Takazudo/zudo-scope10/reference/assets/pot/ASSET-NOTES.md

# RK09L1140A5L

Record: `c7419101`

3D status: **exact_manufacturer_step**

These assets support component selection and CAD inspection. Qualification of the selected manufacturing variant remains separate.

## Facts

{
  "electrical": [
    "Single 10 kΩ linear 1B; ±20%; 0.05 W; max 50 VAC / 10 VDC.",
    "Pins 1 and 3 are track ends; pin 2 is wiper."
  ],
  "mechanical": [
    "Vertical flat metal shaft, L1=15 mm; diameter 6 mm with drawing tolerances, flat dimension 4.5 mm.",
    "M9×0.75 bushing; LB=5 mm; flat length l1=7 mm.",
    "Drawing body width 12.1 mm; mounting-side hole drawing has three 1 mm electrical holes across a 5 mm span and 11.3 mm support spacing.",
    "300° ±5° rotation, no detent; drawing shows full CCW shaft position."
  ],
  "soldering": [
    "Manufacturer product page: dip 260±5 °C max, 5±1 s, max 2 passes; preheat underside 100 °C max, 2 min.",
    "Hand solder reference 350 °C max, 3 s, once; factory process must be agreed."
  ],
  "source": [
    "Exact product-page dimensional GIF and official RK09L catalog drawing 3."
  ]
}

## Gaps

[
  "Footprint must still be checked against the exact drawing and board stack.",
  "Factory process acceptance and current availability are not established by these files."
]
