Takazudo/zudo-scope10/doc/src/content/docs/components/records/c470p.mdx

---
# GENERATED by scripts/build_docs.py
title: "06035A471KAT2A"
sidebar_position: 24
---

## Identity

| Field | Value |
|---|---|
| Record | c470p |
| Manufacturer | Kyocera AVX |
| Orderable identity | 06035A471KAT2A |
| JLC/LCSC | C597169 |
| Package | 0603 |
| Identity | SPECIFICATION_ONLY |
| Fit | PROPOSED_NOT_ASSEMBLED |
| References | C101 C201 C301 C401 C501 C601 C701 C801 C901 C1001 |
| Footprint candidate | Capacitor_SMD:C_0603_1608Metric |

## Intended function

input filter

## Recorded findings

470pF; C0G 5% &gt;=25 V. Value specified by this design; not an exact orderable.

G08 candidate: LCSC C597169 (https://www.lcsc.com/product-detail/multilayer-ceramic-capacitors-mlcc-smd-smt_kyocera-avx-06035a471kat2a_C597169.html), checked 2026-09-26, stock 240. listing_not_allocation: a page listing is not allocated stock or an order.

## Pin map

Pin assignments below are electrical evidence or explicitly logical placeholders. They are not footprint qualification.

| Pin | Function |
|---|---|
| 1 | P1 |
| 2 | P2 |

## Documents and models

No original model or source binary was recovered for this record in this package. See the sources and the local download manifest; no nominal model is presented as an exact replacement.

## Coverage and unresolved questions

**Footprint independently qualified: NO. Factory order approved: NO. Bench result: NOT TESTED.**

- meets_spec: NO on tolerance. Value/dielectric/voltage/package match, but the page states +/-10% tolerance, looser than this design's stated 5% max. Do not fabricate against this candidate without a tighter-tolerance replacement or a design tolerance review.

The presence of a part number, datasheet or model closes none of these remaining gates automatically.

## Sources

Values and package constraints are authored design requirements, not manufacturer-verified specifications of a selected orderable part. Select the exact item and add its evidence before placement.
