Takazudo/zudo-scope10/doc/src/content/docs/components/records/display.mdx

---
# GENERATED by scripts/build_docs.py
title: "Pico-ResTouch-LCD-3.5 (SKU 19907)"
sidebar_position: 7
---

## Identity

| Field | Value |
|---|---|
| Record | display |
| Manufacturer | Waveshare |
| Orderable identity | Pico-ResTouch-LCD-3.5 (SKU 19907) |
| JLC/LCSC | NOT VERIFIED / NOT APPLICABLE |
| Package | 86 x 57.2 mm board |
| Identity | EXACT_MPN |
| Fit | PROPOSED_NOT_ASSEMBLED |
| References | External plug-in module |
| Footprint candidate | NOT ASSIGNED |

## Intended function

Single display with ten panes; touch and SD unused

## Recorded findings

480 x 320; portrait logical surface 320 x 480. Active area 48.96 x 73.44 mm in portrait.

5 V module; 3.3 V logic. Vendor module uses a serial-to-16-bit-parallel bridge and RGB565.

Factory female Pico socket headers are present.

Outline 86.00 x 57.20 x 1.6 mm PCB, R1.0 corners; two 1.0 mm recesses on the pin-1 edge (RUN 38.64-47.62, microSD 61.06-76.95 from the header-side edge).

Mounting holes 4.10 from each corner, 77.80 x 49.00 pitch; STEP models dia 5.5 x 4.0 mm standoffs (dia 2.5 bore) on the socket side. Drill diameter not dimensioned.

Female Pico sockets on the non-LCD side: pins 1-20 row 10.45 mm and pins 21-40 row 28.25 mm from the header-side edge (17.80 in STEP, 17.78 nominal); pin 1 and pin 40 at 1.62 mm from the pin-1 edge; pitch 2.54.

Socket housing extends 9.0 mm below the module PCB; modelled cavity depth 8.0 mm. Other underside parts &lt;= 4.0 mm (standoffs), RUN switch 3.5 mm.

Active area 73.44 x 48.96 mm at 3.60 (header side) / 8.96 / 3.97 (pin-1 edge) / 4.27 mm from the board edges; glass top 5.2 mm above module PCB top.

## Pin map

Pin assignments below are electrical evidence or explicitly logical placeholders. They are not footprint qualification.

| Pin | Function |
|---|---|
| 1 | GP0 |
| 2 | GP1 |
| 3 | GND |
| 4 | GP2 |
| 5 | GP3 |
| 6 | GP4 |
| 7 | GP5 |
| 8 | GND |
| 9 | GP6 |
| 10 | GP7 |
| 11 | GP8 |
| 12 | GP9 |
| 13 | GND |
| 14 | GP10 |
| 15 | GP11 |
| 16 | GP12 |
| 17 | GP13 |
| 18 | GND |
| 19 | GP14 |
| 20 | GP15 |
| 21 | GP16 |
| 22 | GP17 |
| 23 | GND |
| 24 | GP18 |
| 25 | GP19 |
| 26 | GP20 |
| 27 | GP21 |
| 28 | GND |
| 29 | GP22 |
| 30 | RUN |
| 31 | GP26_ADC0 |
| 32 | GP27_ADC1 |
| 33 | AGND |
| 34 | GP28_ADC2 |
| 35 | ADC_VREF |
| 36 | 3V3_OUT |
| 37 | 3V3_EN |
| 38 | GND |
| 39 | VSYS |
| 40 | VBUS |

## Documents and models

No original model or source binary was recovered for this record in this package. See the sources and the local download manifest; no nominal model is presented as an exact replacement.

## Coverage and unresolved questions

**Footprint independently qualified: NO. Factory order approved: NO. Bench result: NOT TESTED.**

- STOP: inspect R11/R12/R14/R15 regulator straps and module revision before connecting power.
- Do not tie Pico 3V3_OUT to the display regulator output.
- Verify high/low unused chip-select states and SPI word framing.
- Measure mounting-hole drill and standoff thread; confirm socket engagement spec on the received module.

The presence of a part number, datasheet or model closes none of these remaining gates automatically.

## Sources

### Waveshare SKU 19907

[https://www.waveshare.com/Pico-ResTouch-LCD-3.5.htm](https://www.waveshare.com/Pico-ResTouch-LCD-3.5.htm)

Evidence state: `read_online`. Manufacturer page: 480x320, 5 V, installed female Pico headers, 86x57.2 mm module.

### Waveshare interface and resources

[https://www.waveshare.net/wiki/Pico-ResTouch-LCD-3.5](https://www.waveshare.net/wiki/Pico-ResTouch-LCD-3.5)

Evidence state: `read_online`. Manufacturer pin assignment table and 16-bit parallel-to-SPI bridge explanation; RGB565.

### Waveshare module schematic

[https://files.waveshare.com/upload/8/85/Pico-ResTouch-LCD-3.5_Sch.pdf](https://files.waveshare.com/upload/8/85/Pico-ResTouch-LCD-3.5_Sch.pdf)

Evidence state: `read_online`. Parsed online. Page-image retrieval failed. Module regulator straps and power connections require visual verification locally.

### Waveshare module CAD archive

[https://files.waveshare.com/upload/e/e4/Pico-ResTouch-LCD-3_5.zip](https://files.waveshare.com/upload/e/e4/Pico-ResTouch-LCD-3_5.zip)

Evidence state: `download_unavailable`. Official link; binary download failed in this environment. NOT included.

### Waveshare example code

[https://files.waveshare.com/upload/f/fc/Pico-ResTouch-LCD-X_X_Code.zip](https://files.waveshare.com/upload/f/fc/Pico-ResTouch-LCD-X_X_Code.zip)

Evidence state: `download_unavailable`. Official link; binary download failed. Vendor driver integration remains open; do not use generic ILI9488 serial driver.
