Takazudo/zudo-scope10/doc/src/content/docs/components/records/fuse.mdx

---
# GENERATED by scripts/build_docs.py
title: "1206L050YR"
sidebar_position: 14
---

## Identity

| Field | Value |
|---|---|
| Record | fuse |
| Manufacturer | Littelfuse |
| Orderable identity | 1206L050YR |
| JLC/LCSC | C163512 |
| Package | 1206 PPTC candidate |
| Identity | SPECIFICATION_ONLY |
| Fit | PROPOSED_NOT_ASSEMBLED |
| References | F1 |
| Footprint candidate | NOT ASSIGNED |

## Intended function

Analog/display branch protection

## Recorded findings

Proposed 500 mA hold, &gt;=6 V. This does not limit Pico USB inrush before the carrier branch.

G08 candidate: LCSC C163512, Littelfuse 1206L050YR (https://lcsc.com/product-detail/Resettable-Fuses_Littelfuse-1206L050YR_C163512.html), checked 2026-09-26, stock 21130. listing_not_allocation: a page listing is not allocated stock or an order.

## Pin map

Pin assignments below are electrical evidence or explicitly logical placeholders. They are not footprint qualification.

| Pin | Function |
|---|---|
| 1 | IN |
| 2 | OUT |

## Documents and models

No original model or source binary was recovered for this record in this package. See the sources and the local download manifest; no nominal model is presented as an exact replacement.

## Coverage and unresolved questions

**Footprint independently qualified: NO. Factory order approved: NO. Bench result: NOT TESTED.**

- meets_spec: exact match at 500 mA hold / 6 V, no margin above the stated minimums. Sizing against the actual measured inrush budget is out of scope for this evidence pass (see G07). Select/confirm the actual part and qualify trip time, cold resistance and USB current budget before fabrication.

The presence of a part number, datasheet or model closes none of these remaining gates automatically.

## Sources

Values and package constraints are authored design requirements, not manufacturer-verified specifications of a selected orderable part. Select the exact item and add its evidence before placement.
