Takazudo/zudo-scope10/doc/src/content/docs/components/records/pico-h.mdx

---
# GENERATED by scripts/build_docs.py
title: "Raspberry Pi Pico H"
sidebar_position: 6
---

## Identity

| Field | Value |
|---|---|
| Record | pico-h |
| Manufacturer | Raspberry Pi |
| Orderable identity | Raspberry Pi Pico H |
| JLC/LCSC | NOT VERIFIED / NOT APPLICABLE |
| Package | 51 x 21 mm board |
| Identity | EXACT_MPN |
| Fit | PROPOSED_NOT_ASSEMBLED |
| References | External plug-in module |
| Footprint candidate | NOT ASSIGNED |

## Intended function

Socketed RP2040 module with factory-populated headers and USB

## Recorded findings

Factory H version only; the ordinary bare-header Pico does not meet the no-soldering purchase specification.

Pico ADC inputs are GP26-28; GP29 is not a free external ADC pin on this board.

500 kS/s is aggregate. Ten inputs are acquired sequentially.

51 x 21 x 1.0 mm; pin rows 17.78 apart, 48.26 first-to-last, 2.54 pitch; micro-USB overhangs the pin-1 edge by 1.3 mm; 4 x dia 2.1 holes 11.4 apart, 2.0 from the USB edge and 2.4 from the far edge.

Physical numbering: pin 1 top-left beside USB, 1-20 down the left, 40 top-right. Orderable SC0917.

## Pin map

Pin assignments below are electrical evidence or explicitly logical placeholders. They are not footprint qualification.

| Pin | Function |
|---|---|
| 1 | GP0 |
| 2 | GP1 |
| 3 | GND |
| 4 | GP2 |
| 5 | GP3 |
| 6 | GP4 |
| 7 | GP5 |
| 8 | GND |
| 9 | GP6 |
| 10 | GP7 |
| 11 | GP8 |
| 12 | GP9 |
| 13 | GND |
| 14 | GP10 |
| 15 | GP11 |
| 16 | GP12 |
| 17 | GP13 |
| 18 | GND |
| 19 | GP14 |
| 20 | GP15 |
| 21 | GP16 |
| 22 | GP17 |
| 23 | GND |
| 24 | GP18 |
| 25 | GP19 |
| 26 | GP20 |
| 27 | GP21 |
| 28 | GND |
| 29 | GP22 |
| 30 | RUN |
| 31 | GP26_ADC0 |
| 32 | GP27_ADC1 |
| 33 | AGND |
| 34 | GP28_ADC2 |
| 35 | ADC_VREF |
| 36 | 3V3_OUT |
| 37 | 3V3_EN |
| 38 | GND |
| 39 | VSYS |
| 40 | VBUS |

## Documents and models

No original model or source binary was recovered for this record in this package. See the sources and the local download manifest; no nominal model is presented as an exact replacement.

## Coverage and unresolved questions

**Footprint independently qualified: NO. Factory order approved: NO. Bench result: NOT TESTED.**

- Module socket exact MPN, standoff height and USB access; verify Pico H module pinout against assembly.
- Pico H factory header insulator height and pin length are not dimensioned in the Pico datasheet/product brief; measure a unit or obtain a Raspberry Pi drawing.

The presence of a part number, datasheet or model closes none of these remaining gates automatically.

## Sources

### Raspberry Pi Pico / Pico H

[https://www.raspberrypi.com/products/raspberry-pi-pico/](https://www.raspberrypi.com/products/raspberry-pi-pico/)

Evidence state: `read_online`. Manufacturer product page. Order H version with installed headers, not an unsoldered Pico.

### Pico pinout

[https://datasheets.raspberrypi.com/pico/Pico-R3-A4-Pinout.pdf](https://datasheets.raspberrypi.com/pico/Pico-R3-A4-Pinout.pdf)

Evidence state: `read_online`. Pinout inspected online as page image. Same header numbering used for both carrier interfaces.

### Pico SDK ADC documentation

[https://www.raspberrypi.com/documentation/pico-sdk/hardware.html](https://www.raspberrypi.com/documentation/pico-sdk/hardware.html)

Evidence state: `read_online`. RP2040: 12-bit ADC, 500 ksample/s aggregate; 8.7 ENOB. Sequential channels, not simultaneous sample-and-hold.
