Takazudo/zudo-scope10/doc/src/content/docs/components/records/r100.mdx

---
# GENERATED by scripts/build_docs.py
title: "0603 \u00b11% 100\u03a9 (VO)"
sidebar_position: 21
---

## Identity

| Field | Value |
|---|---|
| Record | r100 |
| Manufacturer | VO |
| Orderable identity | 0603 ±1% 100Ω (VO) |
| JLC/LCSC | C2889384 |
| Package | 0603 |
| Identity | SPECIFICATION_ONLY |
| Fit | PROPOSED_NOT_ASSEMBLED |
| References | R20 R21 R22 |
| Footprint candidate | Resistor_SMD:R_0603_1608Metric |

## Intended function

ADC isolation

## Recorded findings

100; 1%. Value specified by this design; not an exact orderable.

G08 candidate: LCSC C2889384 (https://www.lcsc.com/product-detail/Chip-Resistor-Surface-Mount_VO_C2889384.html), checked 2026-09-26, meets spec. Page states "Not available now". listing_not_allocation: a page listing is not allocated stock or an order.

## Pin map

Pin assignments below are electrical evidence or explicitly logical placeholders. They are not footprint qualification.

| Pin | Function |
|---|---|
| 1 | P1 |
| 2 | P2 |

## Documents and models

No original model or source binary was recovered for this record in this package. See the sources and the local download manifest; no nominal model is presented as an exact replacement.

## Coverage and unresolved questions

**Footprint independently qualified: NO. Factory order approved: NO. Bench result: NOT TESTED.**

- RFQ/allocate stock before fabrication; page shows zero availability at the time checked.

The presence of a part number, datasheet or model closes none of these remaining gates automatically.

## Sources

Values and package constraints are authored design requirements, not manufacturer-verified specifications of a selected orderable part. Select the exact item and add its evidence before placement.
