Takazudo/zudo-scope10/doc/src/content/docs/components/records/r100k.mdx

---
# GENERATED by scripts/build_docs.py
title: "0603WAF1003T5E"
sidebar_position: 20
---

## Identity

| Field | Value |
|---|---|
| Record | r100k |
| Manufacturer | UNI-ROYAL |
| Orderable identity | 0603WAF1003T5E |
| JLC/LCSC | C25803 |
| Package | 0603 |
| Identity | SPECIFICATION_ONLY |
| Fit | PROPOSED_NOT_ASSEMBLED |
| References | R80 R81 R82 R83 R84 R85 R86 R87 R88 |
| Footprint candidate | Resistor_SMD:R_0603_1608Metric |

## Intended function

digital/default pulls

## Recorded findings

100k; 1%. Value specified by this design; not an exact orderable.

G08 candidate: LCSC C25803 (https://www.lcsc.com/product-detail/C25803.html), checked 2026-09-26, meets spec, stock 17040200. listing_not_allocation: a page listing is not allocated stock or an order.

## Pin map

Pin assignments below are electrical evidence or explicitly logical placeholders. They are not footprint qualification.

| Pin | Function |
|---|---|
| 1 | P1 |
| 2 | P2 |

## Documents and models

No original model or source binary was recovered for this record in this package. See the sources and the local download manifest; no nominal model is presented as an exact replacement.

## Coverage and unresolved questions

**Footprint independently qualified: NO. Factory order approved: NO. Bench result: NOT TESTED.**

- RFQ/allocate stock before fabrication; listing is not an order.

The presence of a part number, datasheet or model closes none of these remaining gates automatically.

## Sources

Values and package constraints are authored design requirements, not manufacturer-verified specifications of a selected orderable part. Select the exact item and add its evidence before placement.
