Takazudo/zudo-scope10/doc/src/content/docs/components/records/r10k.mdx

---
# GENERATED by scripts/build_docs.py
title: "0603WAF1002T5E"
sidebar_position: 19
---

## Identity

| Field | Value |
|---|---|
| Record | r10k |
| Manufacturer | UNI-ROYAL |
| Orderable identity | 0603WAF1002T5E |
| JLC/LCSC | C25804 |
| Package | 0603 |
| Identity | SPECIFICATION_ONLY |
| Fit | PROPOSED_NOT_ASSEMBLED |
| References | R40 R41 R51 R52 |
| Footprint candidate | Resistor_SMD:R_0603_1608Metric |

## Intended function

switch ladder, pulls

## Recorded findings

10k; 1%. Value specified by this design; not an exact orderable.

G08 candidate: LCSC C25804 (https://www.lcsc.com/product-detail/C25804.html), checked 2026-09-26, meets spec. Page states "Out of Stock" with a "Notify Me" option. listing_not_allocation: a page listing is not allocated stock or an order.

## Pin map

Pin assignments below are electrical evidence or explicitly logical placeholders. They are not footprint qualification.

| Pin | Function |
|---|---|
| 1 | P1 |
| 2 | P2 |

## Documents and models

No original model or source binary was recovered for this record in this package. See the sources and the local download manifest; no nominal model is presented as an exact replacement.

## Coverage and unresolved questions

**Footprint independently qualified: NO. Factory order approved: NO. Bench result: NOT TESTED.**

- RFQ/allocate stock before fabrication; page shows zero stock at the time checked.

The presence of a part number, datasheet or model closes none of these remaining gates automatically.

## Sources

Values and package constraints are authored design requirements, not manufacturer-verified specifications of a selected orderable part. Select the exact item and add its evidence before placement.
