Takazudo/zudo-scope10/doc/src/content/docs/components/records/r1k.mdx

---
# GENERATED by scripts/build_docs.py
title: "0603WAF1001T5E"
sidebar_position: 22
---

## Identity

| Field | Value |
|---|---|
| Record | r1k |
| Manufacturer | UNI-ROYAL |
| Orderable identity | 0603WAF1001T5E |
| JLC/LCSC | C21190 |
| Package | 0603 |
| Identity | SPECIFICATION_ONLY |
| Fit | PROPOSED_NOT_ASSEMBLED |
| References | R1111 R1112 R1121 R1122 R1131 R1132 R1141 R1142 R1151 R1152 R1161 R1162 R1171 R1172 R1181 R1182 R1191 R1192 R1201 R1202 R30 |
| Footprint candidate | Resistor_SMD:R_0603_1608Metric |

## Intended function

control isolation/rail bleed

## Recorded findings

1k; 1%. Value specified by this design; not an exact orderable.

G08 candidate: LCSC C21190 (https://www.lcsc.com/product-detail/C21190.html), checked 2026-09-26, meets spec, stock 7514000. listing_not_allocation: a page listing is not allocated stock or an order.

## Pin map

Pin assignments below are electrical evidence or explicitly logical placeholders. They are not footprint qualification.

| Pin | Function |
|---|---|
| 1 | P1 |
| 2 | P2 |

## Documents and models

No original model or source binary was recovered for this record in this package. See the sources and the local download manifest; no nominal model is presented as an exact replacement.

## Coverage and unresolved questions

**Footprint independently qualified: NO. Factory order approved: NO. Bench result: NOT TESTED.**

- RFQ/allocate stock before fabrication; listing is not an order.

The presence of a part number, datasheet or model closes none of these remaining gates automatically.

## Sources

Values and package constraints are authored design requirements, not manufacturer-verified specifications of a selected orderable part. Select the exact item and add its evidence before placement.
