Takazudo/zudo-scope10/doc/src/content/docs/components/records/r1m.mdx

---
# GENERATED by scripts/build_docs.py
title: "RT0603BRD071ML"
sidebar_position: 15
---

## Identity

| Field | Value |
|---|---|
| Record | r1m |
| Manufacturer | YAGEO |
| Orderable identity | RT0603BRD071ML |
| JLC/LCSC | C326730 |
| Package | 0603 |
| Identity | SPECIFICATION_ONLY |
| Fit | PROPOSED_NOT_ASSEMBLED |
| References | R101 R201 R301 R401 R501 R601 R701 R801 R901 R1001 |
| Footprint candidate | Resistor_SMD:R_0603_1608Metric |

## Intended function

input impedance/current limit

## Recorded findings

1M; 0.1% 25 ppm/C; &gt;=50 V. Value specified by this design; not an exact orderable.

G08 candidate: LCSC C326730 (https://www.lcsc.com/product-detail/C326730.html), checked 2026-09-26, meets spec, stock 8540. listing_not_allocation: a page listing is not allocated stock or an order.

## Pin map

Pin assignments below are electrical evidence or explicitly logical placeholders. They are not footprint qualification.

| Pin | Function |
|---|---|
| 1 | P1 |
| 2 | P2 |

## Documents and models

No original model or source binary was recovered for this record in this package. See the sources and the local download manifest; no nominal model is presented as an exact replacement.

## Coverage and unresolved questions

**Footprint independently qualified: NO. Factory order approved: NO. Bench result: NOT TESTED.**

- RFQ/allocate stock before fabrication; listing is not an order.

The presence of a part number, datasheet or model closes none of these remaining gates automatically.

## Sources

Values and package constraints are authored design requirements, not manufacturer-verified specifications of a selected orderable part. Select the exact item and add its evidence before placement.
