Takazudo/zudo-scope10/doc/src/content/docs/components/records/r200k.mdx

---
# GENERATED by scripts/build_docs.py
title: "RT0603BRD07200KL"
sidebar_position: 16
---

## Identity

| Field | Value |
|---|---|
| Record | r200k |
| Manufacturer | YAGEO |
| Orderable identity | RT0603BRD07200KL |
| JLC/LCSC | C728585 |
| Package | 0603 |
| Identity | SPECIFICATION_ONLY |
| Fit | PROPOSED_NOT_ASSEMBLED |
| References | R102 R202 R302 R402 R502 R602 R702 R802 R902 R1002 |
| Footprint candidate | Resistor_SMD:R_0603_1608Metric |

## Intended function

bias divider

## Recorded findings

200k; 0.1% 25 ppm/C. Value specified by this design; not an exact orderable.

G08 candidate: LCSC C728585 (https://lcsc.com/product-detail/chip-resistor-surface-mount_yageo-rt0603brd07200kl_C728585.html), checked 2026-09-26, meets spec, stock 248120. listing_not_allocation: a page listing is not allocated stock or an order.

## Pin map

Pin assignments below are electrical evidence or explicitly logical placeholders. They are not footprint qualification.

| Pin | Function |
|---|---|
| 1 | P1 |
| 2 | P2 |

## Documents and models

No original model or source binary was recovered for this record in this package. See the sources and the local download manifest; no nominal model is presented as an exact replacement.

## Coverage and unresolved questions

**Footprint independently qualified: NO. Factory order approved: NO. Bench result: NOT TESTED.**

- RFQ/allocate stock before fabrication; listing is not an order.

The presence of a part number, datasheet or model closes none of these remaining gates automatically.

## Sources

Values and package constraints are authored design requirements, not manufacturer-verified specifications of a selected orderable part. Select the exact item and add its evidence before placement.
