Takazudo/zudo-scope10/doc/src/content/docs/components/records/r249k.mdx

---
# GENERATED by scripts/build_docs.py
title: "r249k / supplier selection open"
sidebar_position: 17
---

## Identity

| Field | Value |
|---|---|
| Record | r249k |
| Manufacturer | RFQ value/package selection |
| Orderable identity | NOT SELECTED |
| JLC/LCSC | NOT VERIFIED / NOT APPLICABLE |
| Package | 0603 |
| Identity | SPECIFICATION_ONLY |
| Fit | PROPOSED_NOT_ASSEMBLED |
| References | R103 R203 R303 R403 R503 R603 R703 R803 R903 R1003 |
| Footprint candidate | Resistor_SMD:R_0603_1608Metric |

## Intended function

bias divider

## Recorded findings

249k; 0.1% 25 ppm/C. Value specified by this design; not an exact orderable.

G08 (#9): manufacturer spec sheet confirms YAGEO RT0603BRD07249KL exists at this value, but no LCSC product-detail page was found or fetched; no C-number is recorded here without a fetched citation.

## Pin map

Pin assignments below are electrical evidence or explicitly logical placeholders. They are not footprint qualification.

| Pin | Function |
|---|---|
| 1 | P1 |
| 2 | P2 |

## Documents and models

No original model or source binary was recovered for this record in this package. See the sources and the local download manifest; no nominal model is presented as an exact replacement.

## Coverage and unresolved questions

**Footprint independently qualified: NO. Factory order approved: NO. Bench result: NOT TESTED.**

- OPEN: no cited LCSC/JLC listing found for the 249k value; assign a stocked exact MPN/C-code and source its datasheet before fabrication.

The presence of a part number, datasheet or model closes none of these remaining gates automatically.

## Sources

Values and package constraints are authored design requirements, not manufacturer-verified specifications of a selected orderable part. Select the exact item and add its evidence before placement.
