Takazudo/zudo-scope10/doc/src/content/docs/components/records/r33.mdx

---
# GENERATED by scripts/build_docs.py
title: "RC0603FR-0733RL"
sidebar_position: 23
---

## Identity

| Field | Value |
|---|---|
| Record | r33 |
| Manufacturer | YAGEO |
| Orderable identity | RC0603FR-0733RL |
| JLC/LCSC | C108661 |
| Package | 0603 |
| Identity | SPECIFICATION_ONLY |
| Fit | PROPOSED_NOT_ASSEMBLED |
| References | R60 R61 R62 R63 R64 R65 R66 R67 R68 R69 |
| Footprint candidate | Resistor_SMD:R_0603_1608Metric |

## Intended function

SPI source termination

## Recorded findings

33; 1%. Value specified by this design; not an exact orderable.

G08 candidate: LCSC C108661 (https://www.lcsc.com/product-detail/C108661.html), checked 2026-09-26, meets spec, stock 85500. listing_not_allocation: a page listing is not allocated stock or an order.

G08 rejected a false match found in the same search: 0603WAF3300T5E / C23138 is 330Ω, not 33Ω; not used.

## Pin map

Pin assignments below are electrical evidence or explicitly logical placeholders. They are not footprint qualification.

| Pin | Function |
|---|---|
| 1 | P1 |
| 2 | P2 |

## Documents and models

No original model or source binary was recovered for this record in this package. See the sources and the local download manifest; no nominal model is presented as an exact replacement.

## Coverage and unresolved questions

**Footprint independently qualified: NO. Factory order approved: NO. Bench result: NOT TESTED.**

- RFQ/allocate stock before fabrication; listing is not an order.

The presence of a part number, datasheet or model closes none of these remaining gates automatically.

## Sources

Values and package constraints are authored design requirements, not manufacturer-verified specifications of a selected orderable part. Select the exact item and add its evidence before placement.
