Takazudo/zudo-scope10/doc/src/content/docs/components/records/r4k7.mdx

---
# GENERATED by scripts/build_docs.py
title: "HoLTT0603-1/10W-4.7K-1%"
sidebar_position: 18
---

## Identity

| Field | Value |
|---|---|
| Record | r4k7 |
| Manufacturer | Milliohm |
| Orderable identity | HoLTT0603-1/10W-4.7K-1% |
| JLC/LCSC | C2904521 |
| Package | 0603 |
| Identity | SPECIFICATION_ONLY |
| Fit | PROPOSED_NOT_ASSEMBLED |
| References | R104 R204 R304 R404 R504 R604 R704 R804 R904 R1004 |
| Footprint candidate | Resistor_SMD:R_0603_1608Metric |

## Intended function

second filter

## Recorded findings

4.7k; 1%. Value specified by this design; not an exact orderable.

G08 candidate: LCSC C2904521 (https://www.lcsc.com/product-detail/C2904521.html), checked 2026-09-26, meets spec, stock 820. listing_not_allocation: a page listing is not allocated stock or an order.

## Pin map

Pin assignments below are electrical evidence or explicitly logical placeholders. They are not footprint qualification.

| Pin | Function |
|---|---|
| 1 | P1 |
| 2 | P2 |

## Documents and models

No original model or source binary was recovered for this record in this package. See the sources and the local download manifest; no nominal model is presented as an exact replacement.

## Coverage and unresolved questions

**Footprint independently qualified: NO. Factory order approved: NO. Bench result: NOT TESTED.**

- RFQ/allocate stock before fabrication; listing is not an order.

The presence of a part number, datasheet or model closes none of these remaining gates automatically.

## Sources

Values and package constraints are authored design requirements, not manufacturer-verified specifications of a selected orderable part. Select the exact item and add its evidence before placement.
