Takazudo/zudo-scope10/doc/src/content/docs/components/records/ref.mdx

---
# GENERATED by scripts/build_docs.py
title: "REF3330AIDBZR"
sidebar_position: 4
---

## Identity

| Field | Value |
|---|---|
| Record | ref |
| Manufacturer | Texas Instruments |
| Orderable identity | REF3330AIDBZR |
| JLC/LCSC | C140329 |
| Package | SOT-23-3 |
| Identity | EXACT_MPN |
| Fit | PROPOSED_NOT_ASSEMBLED |
| References | U11 |
| Footprint candidate | Package_TO_SOT_SMD:SOT-23 |

## Intended function

3.0 V reference buffered by U6D

## Recorded findings

3.0 V version; 0.15% initial accuracy and 30 ppm/C maximum drift are family specifications.

G08 (#9) fetched LCSC C140329 (https://www.lcsc.com/product-detail/C140329.html), checked 2026-09-26, exact MPN match confirmed (REF3330AIDBZR, TI, SOT-23, 3V, +/-0.15%, 30ppm/C max), stock 5102. This verifies, via LCSC, the previously unverified note; JLCPCB's own partdetail page was not independently fetched. listing_not_allocation: a page listing is not allocated stock or an order.

## Pin map

Pin assignments below are electrical evidence or explicitly logical placeholders. They are not footprint qualification.

| Pin | Function |
|---|---|
| 1 | IN |
| 2 | OUT |
| 3 | GND |

## Documents and models

No original model or source binary was recovered for this record in this package. See the sources and the local download manifest; no nominal model is presented as an exact replacement.

## Coverage and unresolved questions

**Footprint independently qualified: NO. Factory order approved: NO. Bench result: NOT TESTED.**

- Visual pin review, full supply/headroom check; no claim that reference fixes RP2040 ADC nonlinearity.

The presence of a part number, datasheet or model closes none of these remaining gates automatically.

## Sources

### TI REF33 datasheet

[https://www.ti.com/lit/ds/symlink/ref33.pdf](https://www.ti.com/lit/ds/symlink/ref33.pdf)

Evidence state: `read_online`. DBZ/SOT23 pin table parsed: 1 IN, 2 OUT, 3 GND. Pin diagram screenshot unavailable; independent visual check open.
