Takazudo/zudo-scope10/doc/src/content/docs/components/records/socket20.mdx

---
# GENERATED by scripts/build_docs.py
title: "socket20 / supplier selection open"
sidebar_position: 12
---

## Identity

| Field | Value |
|---|---|
| Record | socket20 |
| Manufacturer | RFQ exact manufacturer |
| Orderable identity | NOT SELECTED |
| JLC/LCSC | NOT VERIFIED / NOT APPLICABLE |
| Package | 2.54 mm; height TBD |
| Identity | SPECIFICATION_ONLY |
| Fit | PROPOSED_NOT_ASSEMBLED |
| References | J20 J21 |
| Footprint candidate | Connector_PinSocket_2.54mm:PinSocket_1x20_P2.54mm_Vertical |

## Intended function

Two 1x20 female sockets for Pico H

## Recorded findings

Exact mating length, insulator height, retention and shoulder clearance are NOT defined by 2.54 mm pitch alone.

Pico H clearance = socket height + Pico H seated header height (OPEN). Allow 1.3 mm USB overhang beyond the pin-1 edge plus plug access. If the Pico sits under the display, the display gap must exceed the Pico stack.

## Pin map

Pin assignments below are electrical evidence or explicitly logical placeholders. They are not footprint qualification.

| Pin | Function |
|---|---|
| 1 | CONTACT |
| 2 | CONTACT |
| 3 | CONTACT |
| 4 | CONTACT |
| 5 | CONTACT |
| 6 | CONTACT |
| 7 | CONTACT |
| 8 | CONTACT |
| 9 | CONTACT |
| 10 | CONTACT |
| 11 | CONTACT |
| 12 | CONTACT |
| 13 | CONTACT |
| 14 | CONTACT |
| 15 | CONTACT |
| 16 | CONTACT |
| 17 | CONTACT |
| 18 | CONTACT |
| 19 | CONTACT |
| 20 | CONTACT |

## Documents and models

No original model or source binary was recovered for this record in this package. See the sources and the local download manifest; no nominal model is presented as an exact replacement.

## Coverage and unresolved questions

**Footprint independently qualified: NO. Factory order approved: NO. Bench result: NOT TESTED.**

- STOP: select exact orderable and mechanical stack. Factory-populate all four strips.

The presence of a part number, datasheet or model closes none of these remaining gates automatically.

## Sources

### Pico pinout

[https://datasheets.raspberrypi.com/pico/Pico-R3-A4-Pinout.pdf](https://datasheets.raspberrypi.com/pico/Pico-R3-A4-Pinout.pdf)

Evidence state: `read_online`. Pinout inspected online as page image. Same header numbering used for both carrier interfaces.
