Takazudo/zudo-scope10/doc/src/content/docs/components/records/clamp.mdx

---
# GENERATED by scripts/build_docs.py
title: "BAV199,215"
sidebar_position: 5
---

## Identity

| Field | Value |
|---|---|
| Record | clamp |
| Manufacturer | Nexperia |
| Orderable identity | BAV199,215 |
| JLC/LCSC | C40919 |
| Package | SOT-23 |
| Identity | EXACT_MPN |
| Fit | PROPOSED_NOT_ASSEMBLED |
| References | D1 D2 D3 D4 D5 D6 D7 D8 D9 D10 |
| Footprint candidate | Package_TO_SOT_SMD:SOT-23 |

## Intended function

Low-leakage input clamp support

## Recorded findings

Two series silicon diodes, junction pin 3.

External diodes are not guaranteed to conduct before op-amp internal clamps; the 1 Mohm series resistor is the primary current limit.

## Pin map

Pin assignments below are electrical evidence or explicitly logical placeholders. They are not footprint qualification.

| Pin | Function |
|---|---|
| 1 | ANODE_LOW |
| 2 | CATHODE_HIGH |
| 3 | JUNCTION |

## Documents and models

No original model or source binary was recovered for this record in this package. See the sources and the local download manifest; no nominal model is presented as an exact replacement.

## Coverage and unresolved questions

**Footprint independently qualified: NO. Factory order approved: NO. Bench result: NOT TESTED.**

- Leakage at temperature; powered and unpowered ±24 V fault tests; combined-channel backfeed.

The presence of a part number, datasheet or model closes none of these remaining gates automatically.

## Sources

### Nexperia BAV199 datasheet

[https://assets.nexperia.com/documents/data-sheet/BAV199.pdf](https://assets.nexperia.com/documents/data-sheet/BAV199.pdf)

Evidence state: `read_online`. Pin diagram visually inspected: 1 A1, 2 K2, 3 K1/A2. Low-leakage silicon, NOT Schottky.

### TI TLV906x datasheet

[https://www.ti.com/lit/ds/symlink/tlv9064.pdf](https://www.ti.com/lit/ds/symlink/tlv9064.pdf)

Evidence state: `read_online`. D/SOIC14 pin diagram visually inspected; 1.8-5.5 V, RRIO, unity stable; overload-current limiting discussion. Parsed version N vs cached figure version M recorded: reacquire one consistent revision before release.
