Takazudo/zudo-scope10/doc/src/content/docs/components/records/ldo.mdx

---
# GENERATED by scripts/build_docs.py
title: "TLV75533PDBVR"
sidebar_position: 3
---

## Identity

| Field | Value |
|---|---|
| Record | ldo |
| Manufacturer | Texas Instruments |
| Orderable identity | TLV75533PDBVR |
| JLC/LCSC | C404027 |
| Package | SOT-23-5 |
| Identity | EXACT_MPN |
| Fit | PROPOSED_NOT_ASSEMBLED |
| References | U10 |
| Footprint candidate | Package_TO_SOT_SMD:SOT-23-5 |

## Intended function

Separate analog 3.3 V regulator

## Recorded findings

Recommended VIN at most 5.5 V; absolute max 6 V. No USB-PD voltages.

1 uF or larger input and output capacitors; actual effective capacitance must satisfy datasheet.

## Pin map

Pin assignments below are electrical evidence or explicitly logical placeholders. They are not footprint qualification.

| Pin | Function |
|---|---|
| 1 | IN |
| 2 | GND |
| 3 | EN |
| 4 | NC |
| 5 | OUT |

## Documents and models

No original model or source binary was recovered for this record in this package. See the sources and the local download manifest; no nominal model is presented as an exact replacement.

## Coverage and unresolved questions

**Footprint independently qualified: NO. Factory order approved: NO. Bench result: NOT TESTED.**

- Thermal, inrush and reverse current/power-down checks.

The presence of a part number, datasheet or model closes none of these remaining gates automatically.

## Sources

### TI TLV755P datasheet

[https://www.ti.com/lit/ds/symlink/tlv755p.pdf](https://www.ti.com/lit/ds/symlink/tlv755p.pdf)

Evidence state: `read_online`. DBV pin table parsed; ratings page visually inspected. 5.5 V recommended maximum input, 6 V absolute maximum.
