Takazudo/zudo-scope10/doc/src/content/docs/components/records/mux.mdx

---
# GENERATED by scripts/build_docs.py
title: "74HC4067PW,118"
sidebar_position: 2
---

## Identity

| Field | Value |
|---|---|
| Record | mux |
| Manufacturer | Nexperia |
| Orderable identity | 74HC4067PW,118 |
| JLC/LCSC | C179326 |
| Package | TSSOP-24 |
| Identity | EXACT_MPN |
| Fit | PROPOSED_NOT_ASSEMBLED |
| References | U7 U8 U9 |
| Footprint candidate | Package_SO:TSSOP-24_4.4x7.8mm_P0.65mm |

## Intended function

Separate signal, TIME and RANGE mux banks with shared four-bit address

## Recorded findings

16:1 analog multiplexer; enable HIGH disconnects all channels.

The 80 ohm headline is not a guaranteed 3.3 V on-resistance; do not use it as such.

## Pin map

Pin assignments below are electrical evidence or explicitly logical placeholders. They are not footprint qualification.

| Pin | Function |
|---|---|
| 1 | Z |
| 2 | Y7 |
| 3 | Y6 |
| 4 | Y5 |
| 5 | Y4 |
| 6 | Y3 |
| 7 | Y2 |
| 8 | Y1 |
| 9 | Y0 |
| 10 | S0 |
| 11 | S1 |
| 12 | GND |
| 13 | S3 |
| 14 | S2 |
| 15 | E_N |
| 16 | Y15 |
| 17 | Y14 |
| 18 | Y13 |
| 19 | Y12 |
| 20 | Y11 |
| 21 | Y10 |
| 22 | Y9 |
| 23 | Y8 |
| 24 | VCC |

## Documents and models

No original model or source binary was recovered for this record in this package. See the sources and the local download manifest; no nominal model is presented as an exact replacement.

## Coverage and unresolved questions

**Footprint independently qualified: NO. Factory order approved: NO. Bench result: NOT TESTED.**

- Measure full-scale channel-to-channel settling, charge injection and cross-talk at 3.3 V.

The presence of a part number, datasheet or model closes none of these remaining gates automatically.

## Sources

### Nexperia 74HC/HCT4067 datasheet

[https://assets.nexperia.com/documents/data-sheet/74HC_HCT4067.pdf](https://assets.nexperia.com/documents/data-sheet/74HC_HCT4067.pdf)

Evidence state: `read_online`. PW/TSSOP24 pin diagram visually inspected; HC part selected, not HCT.
