Takazudo/zudo-scope10/doc/src/content/docs/components/records/tlv9064.mdx

---
# GENERATED by scripts/build_docs.py
title: "TLV9064IDR"
sidebar_position: 1
---

## Identity

| Field | Value |
|---|---|
| Record | tlv9064 |
| Manufacturer | Texas Instruments |
| Orderable identity | TLV9064IDR |
| JLC/LCSC | C388176 |
| Package | SOIC-14 |
| Identity | EXACT_MPN |
| Fit | PROPOSED_NOT_ASSEMBLED |
| References | U1 U2 U3 U4 U5 U6 |
| Footprint candidate | Package_SO:SOIC-14_3.9x8.7mm_P1.27mm |

## Intended function

Six quad amplifiers: two stages per input plus three ADC buffers and reference buffer

## Recorded findings

Quad RRIO amplifier on +3V3A. Supply range 1.8-5.5 V. 10 MHz is a nominal device property, not system bandwidth.

The exact D package uses no shutdown pin. Catalog descriptions of an enable/shutdown feature apply to other variants.

## Pin map

Pin assignments below are electrical evidence or explicitly logical placeholders. They are not footprint qualification.

| Pin | Function |
|---|---|
| 1 | OUT_A |
| 2 | IN_A_MINUS |
| 3 | IN_A_PLUS |
| 4 | VCC |
| 5 | IN_B_PLUS |
| 6 | IN_B_MINUS |
| 7 | OUT_B |
| 8 | OUT_C |
| 9 | IN_C_MINUS |
| 10 | IN_C_PLUS |
| 11 | GND |
| 12 | IN_D_PLUS |
| 13 | IN_D_MINUS |
| 14 | OUT_D |

## Documents and models

No original model or source binary was recovered for this record in this package. See the sources and the local download manifest; no nominal model is presented as an exact replacement.

## Coverage and unresolved questions

**Footprint independently qualified: NO. Factory order approved: NO. Bench result: NOT TESTED.**

- Check worst-case offset and output drive at actual 3.3 V supply; stability with PCB parasitics.

The presence of a part number, datasheet or model closes none of these remaining gates automatically.

## Sources

### TI TLV906x datasheet

[https://www.ti.com/lit/ds/symlink/tlv9064.pdf](https://www.ti.com/lit/ds/symlink/tlv9064.pdf)

Evidence state: `read_online`. D/SOIC14 pin diagram visually inspected; 1.8-5.5 V, RRIO, unity stable; overload-current limiting discussion. Parsed version N vs cached figure version M recorded: reacquire one consistent revision before release.
