Takazudo/zudo-scope10/hardware/kicad/acquisition.kicad_sch

## KiCad design hardware/kicad/acquisition.kicad_sch (2026-09-26)

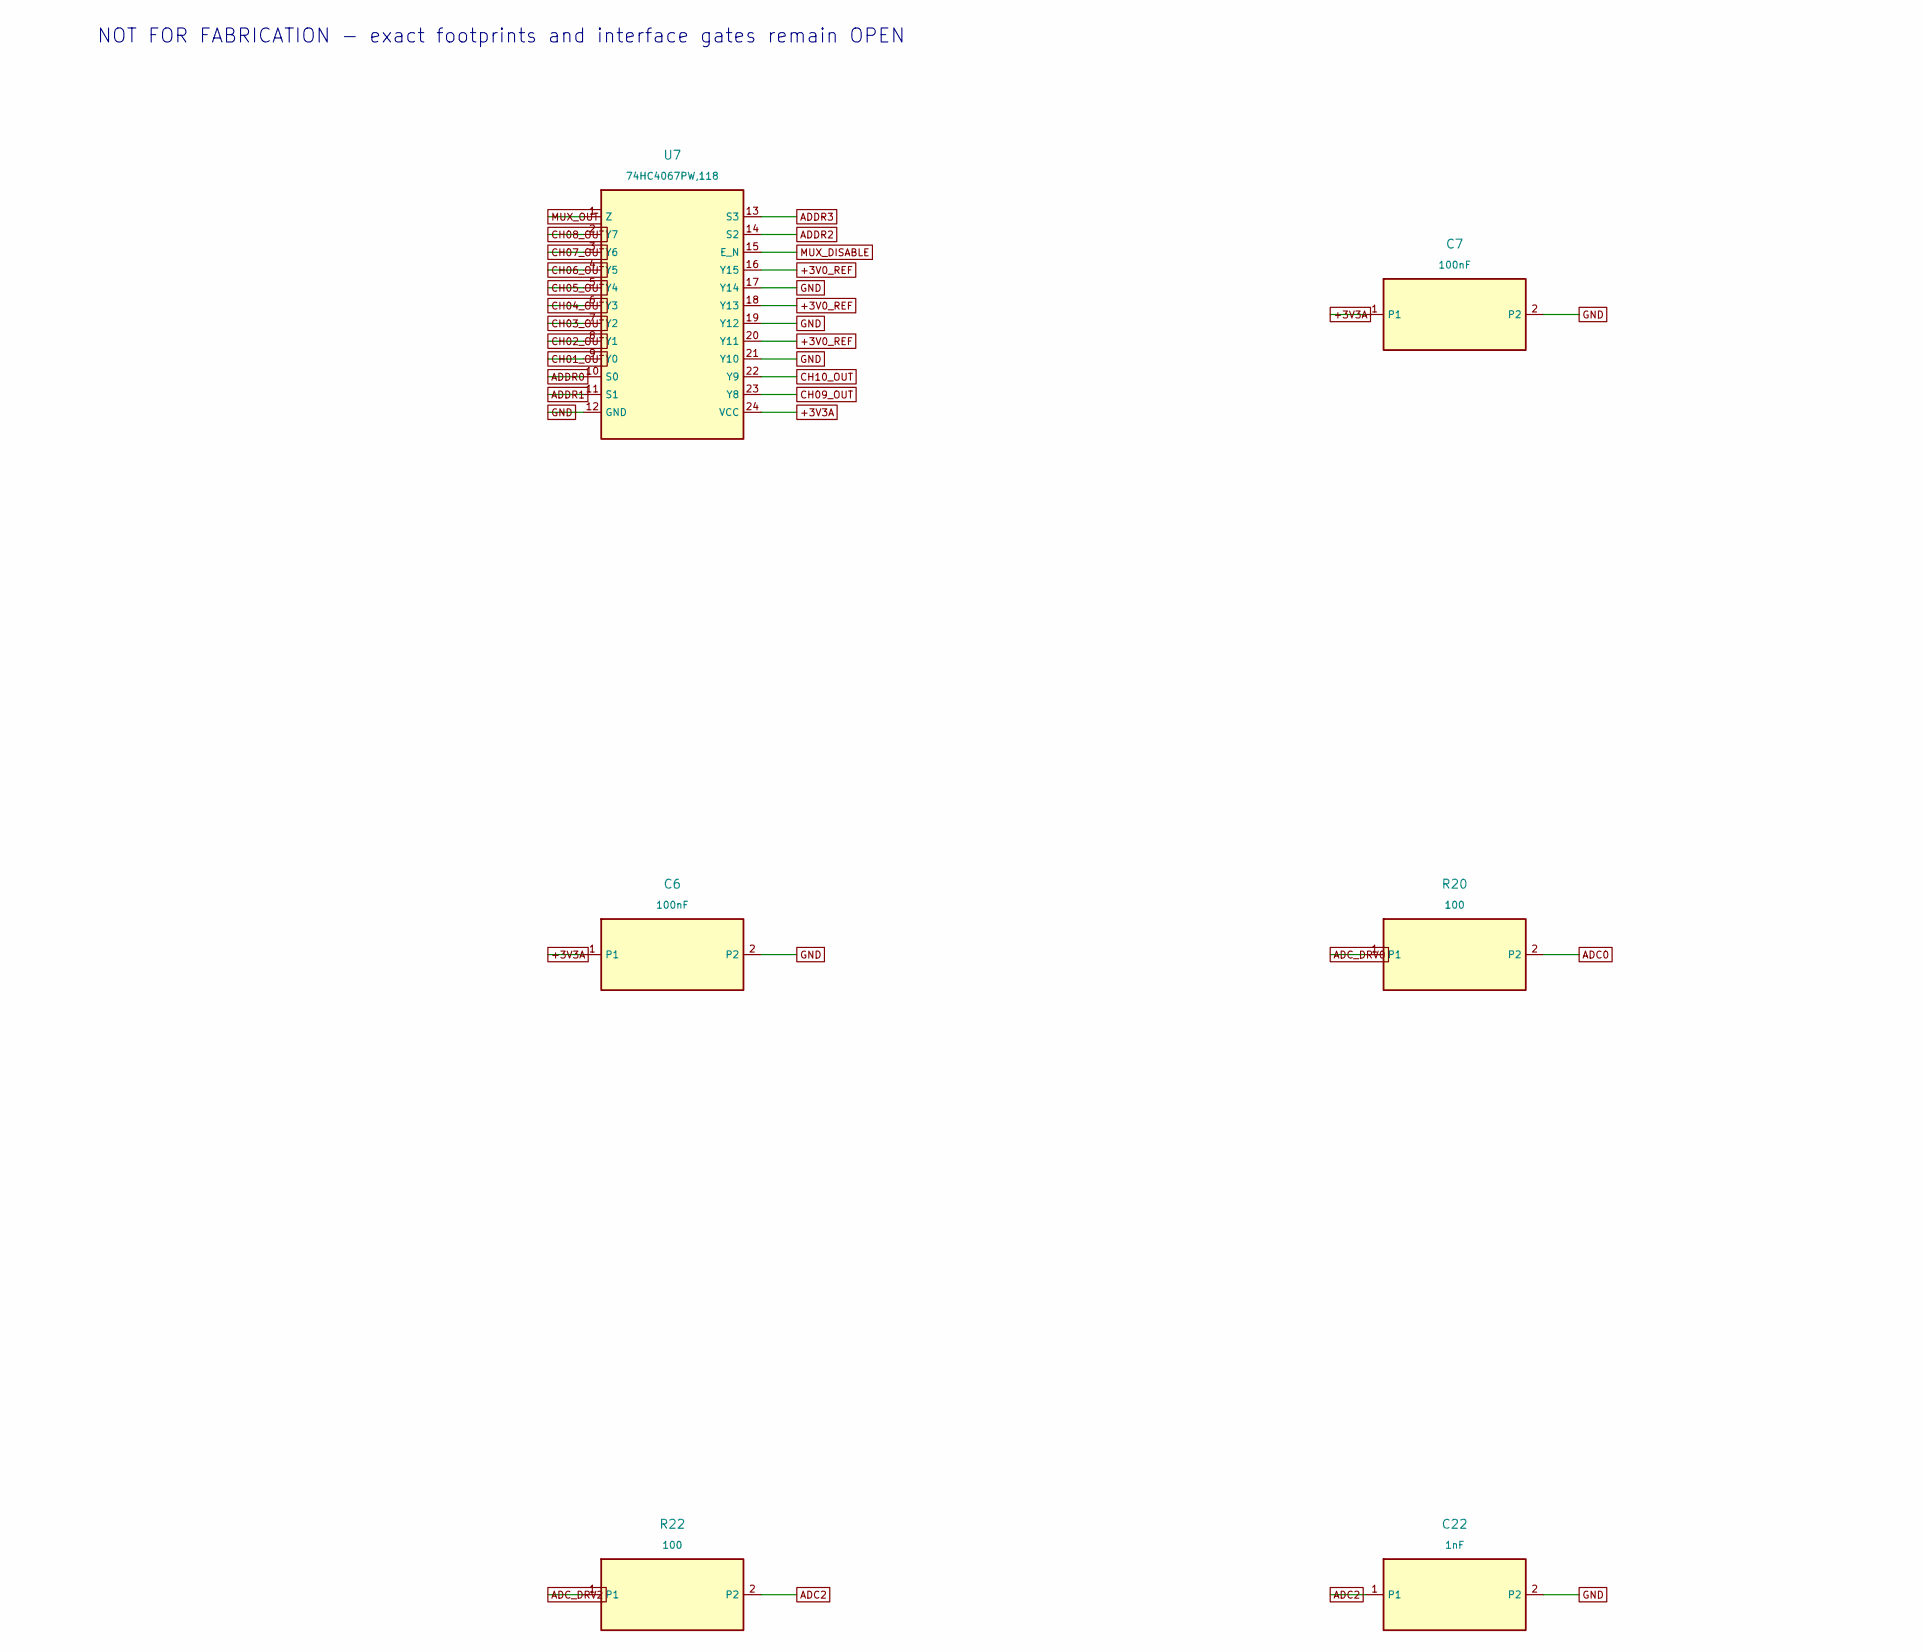
[picture p14: schematic acquisition.kicad_sch, part in row 1, column 1]

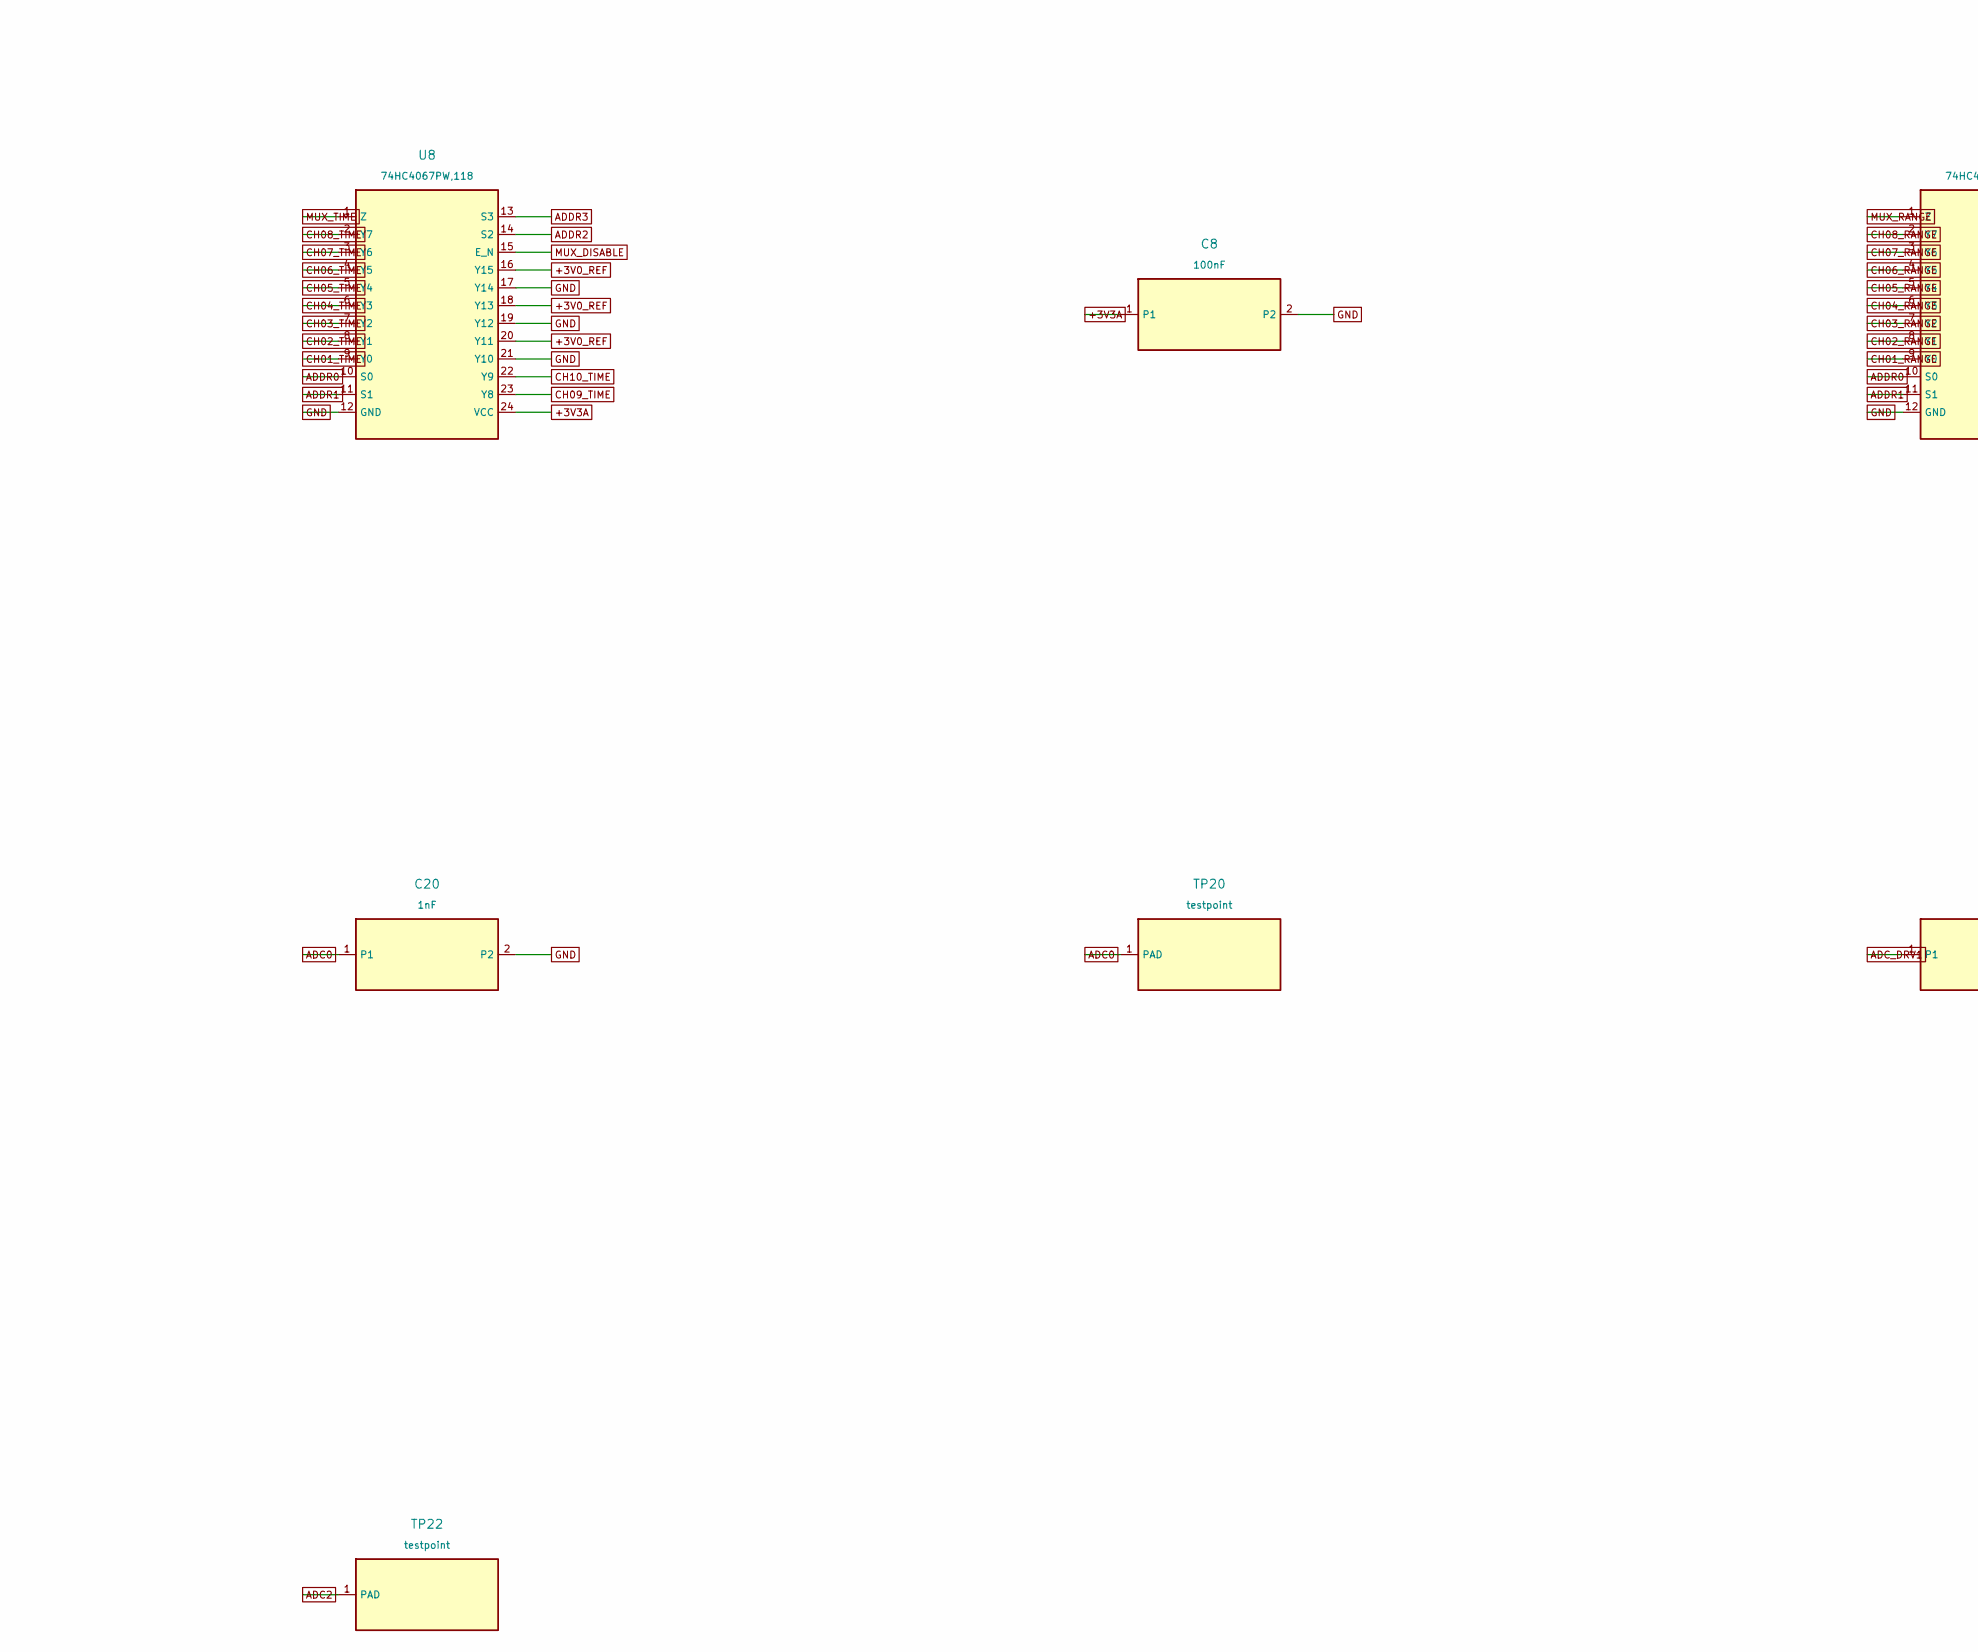
[picture p15: schematic acquisition.kicad_sch, part in row 1, column 2]

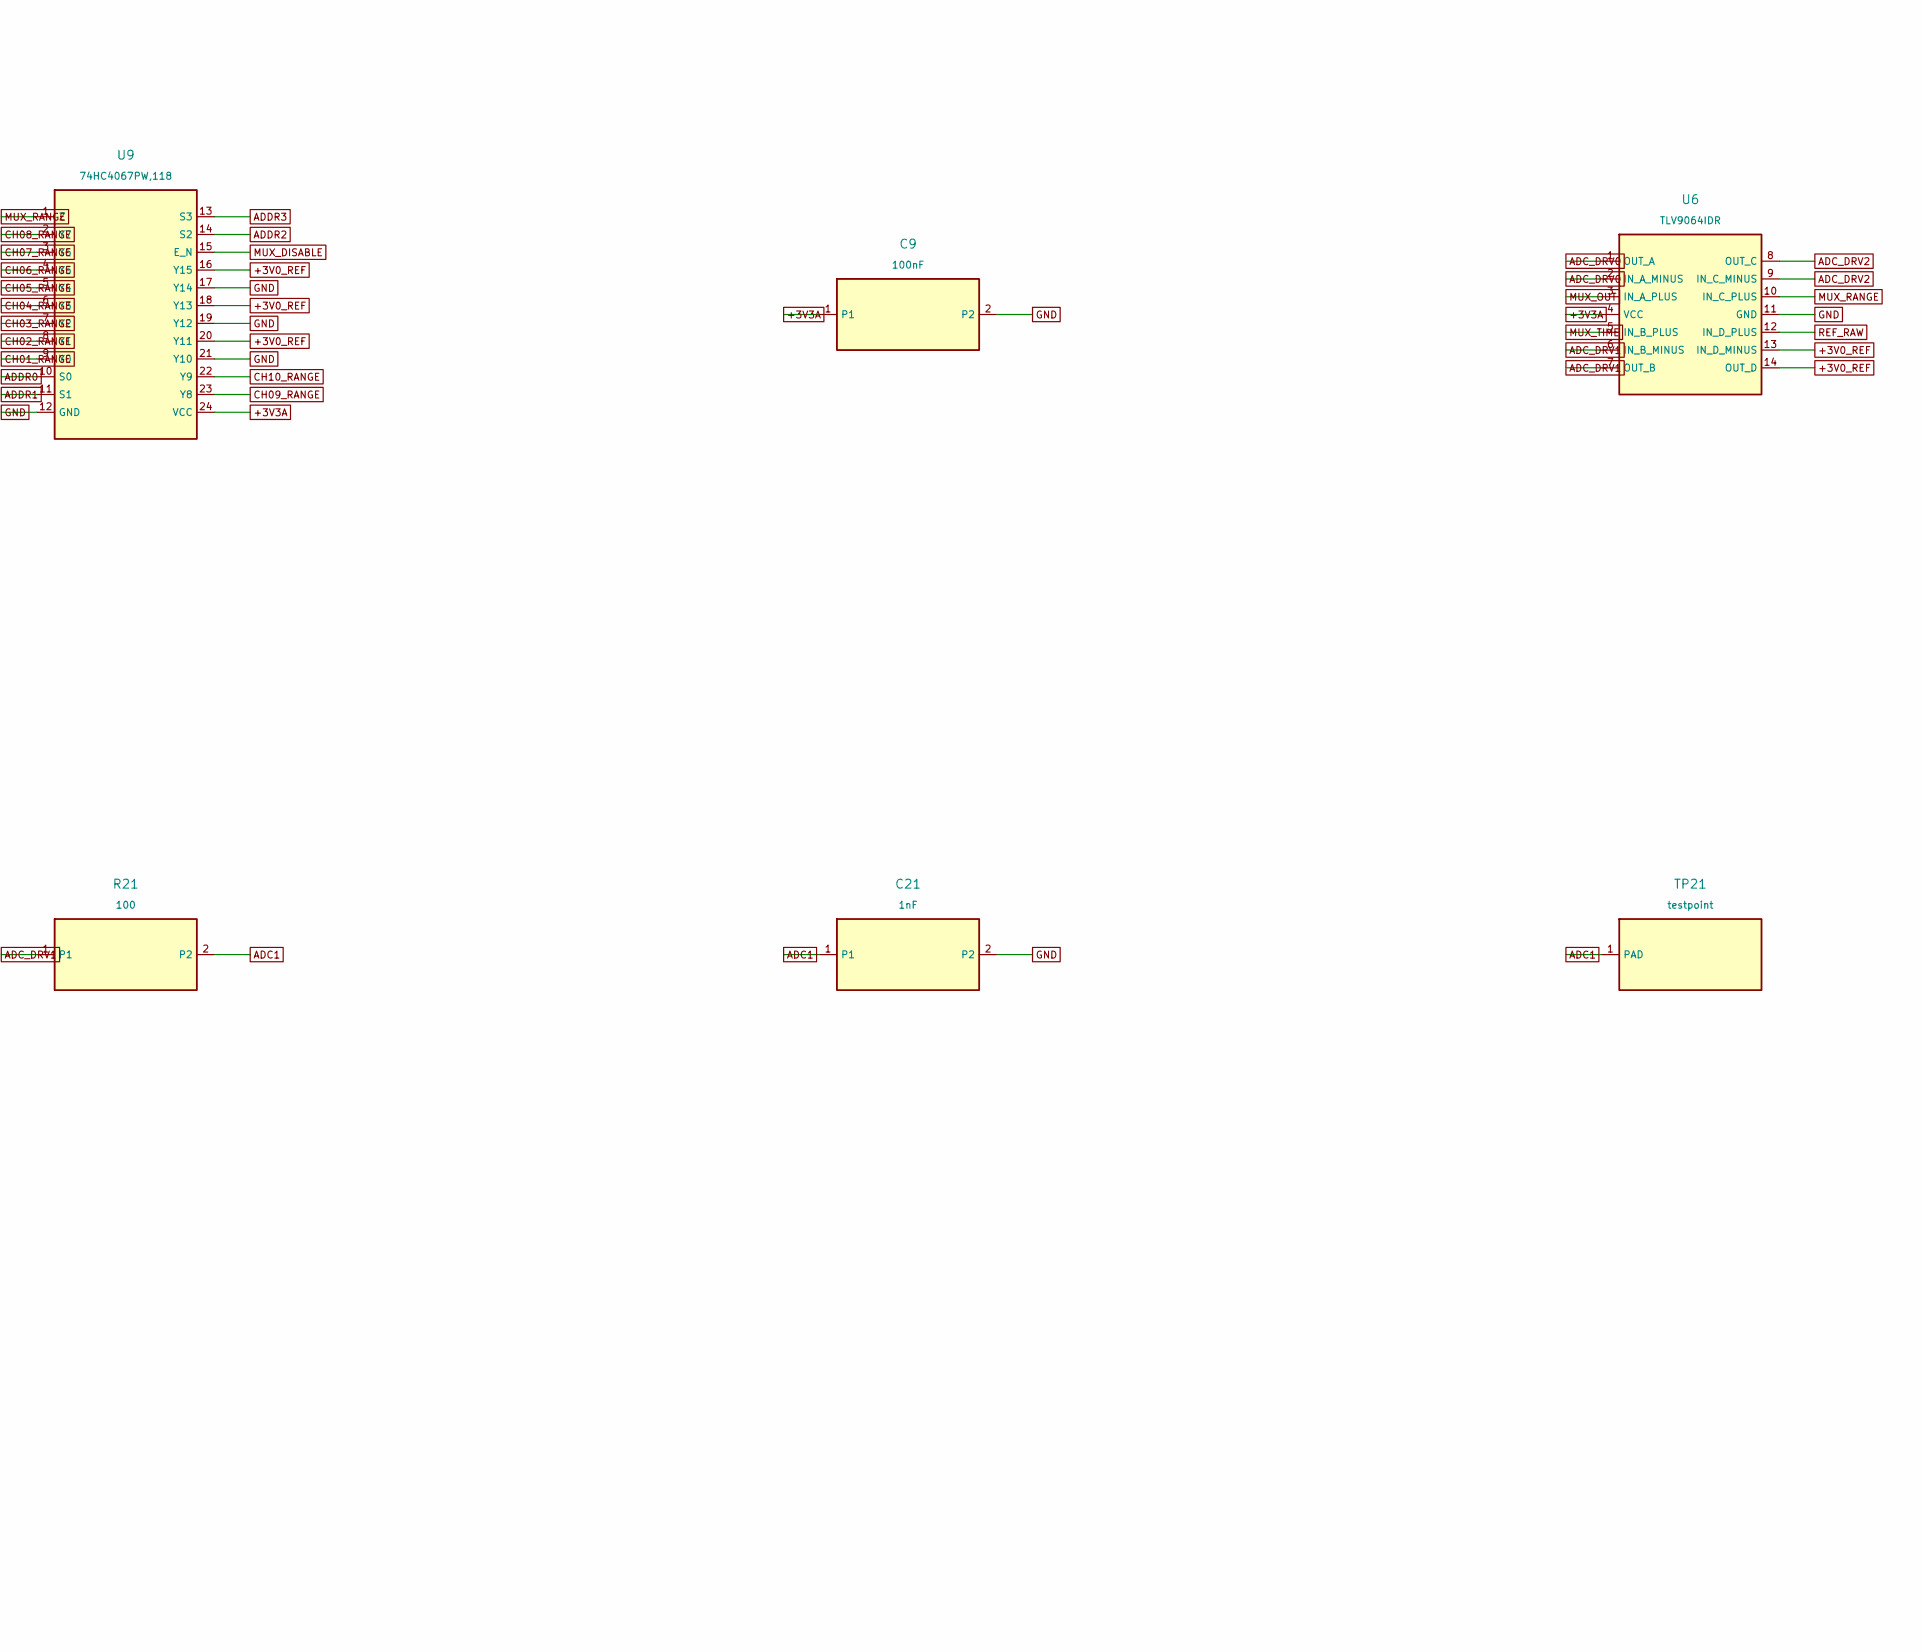
[picture p16: schematic acquisition.kicad_sch, part in row 1, column 3]

Parts:
C6, C7, C8, C9: 100nF; C_0603_1608Metric
C20, C21, C22: 1nF; C_0603_1608Metric
R20, R21, R22: 100; R_0603_1608Metric
TP20, TP21, TP22: testpoint; TestPoint_Pad_D1.0mm
U6: TLV9064IDR; SOIC-14_3.9x8.7mm_P1.27mm
U7, U8, U9: 74HC4067PW,118; TSSOP-24_4.4x7.8mm_P0.65mm

Connections:
+3V0_REF: U6.13 (IN_D_MINUS), U6.14 (OUT_D), U7.16 (Y15), U7.18 (Y13), U7.20 (Y11), U8.16 (Y15), U8.18 (Y13), U8.20 (Y11), U9.16 (Y15), U9.18 (Y13), U9.20 (Y11)
+3V3A: C6.1, C7.1, C8.1, C9.1, U6.4 (VCC), U7.24 (VCC), U8.24 (VCC), U9.24 (VCC)
ADC0: C20.1, R20.2, TP20.1
ADC1: C21.1, R21.2, TP21.1
ADC2: C22.1, R22.2, TP22.1
ADC_DRV0: R20.1, U6.1 (OUT_A), U6.2 (IN_A_MINUS)
ADC_DRV1: R21.1, U6.6 (IN_B_MINUS), U6.7 (OUT_B)
ADC_DRV2: R22.1, U6.8 (OUT_C), U6.9 (IN_C_MINUS)
ADDR0: U7.10 (S0), U8.10 (S0), U9.10 (S0)
ADDR1: U7.11 (S1), U8.11 (S1), U9.11 (S1)
ADDR2: U7.14 (S2), U8.14 (S2), U9.14 (S2)
ADDR3: U7.13 (S3), U8.13 (S3), U9.13 (S3)
CH01_OUT: U7.9 (Y0)
CH01_RANGE: U9.9 (Y0)
CH01_TIME: U8.9 (Y0)
CH02_OUT: U7.8 (Y1)
CH02_RANGE: U9.8 (Y1)
CH02_TIME: U8.8 (Y1)
CH03_OUT: U7.7 (Y2)
CH03_RANGE: U9.7 (Y2)
CH03_TIME: U8.7 (Y2)
CH04_OUT: U7.6 (Y3)
CH04_RANGE: U9.6 (Y3)
CH04_TIME: U8.6 (Y3)
CH05_OUT: U7.5 (Y4)
CH05_RANGE: U9.5 (Y4)
CH05_TIME: U8.5 (Y4)
CH06_OUT: U7.4 (Y5)
CH06_RANGE: U9.4 (Y5)
CH06_TIME: U8.4 (Y5)
CH07_OUT: U7.3 (Y6)
CH07_RANGE: U9.3 (Y6)
CH07_TIME: U8.3 (Y6)
CH08_OUT: U7.2 (Y7)
CH08_RANGE: U9.2 (Y7)
CH08_TIME: U8.2 (Y7)
CH09_OUT: U7.23 (Y8)
CH09_RANGE: U9.23 (Y8)
CH09_TIME: U8.23 (Y8)
CH10_OUT: U7.22 (Y9)
CH10_RANGE: U9.22 (Y9)
CH10_TIME: U8.22 (Y9)
GND: C6.2, C7.2, C8.2, C9.2, C20.2, C21.2, C22.2, U6.11 (GND), U7.12 (GND), U7.17 (Y14), U7.19 (Y12), U7.21 (Y10), U8.12 (GND), U8.17 (Y14), U8.19 (Y12), U8.21 (Y10), U9.12 (GND), U9.17 (Y14), U9.19 (Y12), U9.21 (Y10)
MUX_DISABLE: U7.15 (E_N), U8.15 (E_N), U9.15 (E_N)
MUX_OUT: U6.3 (IN_A_PLUS), U7.1 (Z)
MUX_RANGE: U6.10 (IN_C_PLUS), U9.1 (Z)
MUX_TIME: U6.5 (IN_B_PLUS), U8.1 (Z)
REF_RAW: U6.12 (IN_D_PLUS)

Notes on the sheet:
NOT FOR FABRICATION - exact footprints and interface gates remain OPEN
