Takazudo/zudo-scope10/hardware/kicad/controls-left.kicad_sch

## KiCad design hardware/kicad/controls-left.kicad_sch (2026-09-26)

Schematic: controls-left.kicad_sch

Parts:
C1111, C1112, C1121, C1122, C1131, C1132, C1141, C1142, C1151, C1152: 100nF; C_0603_1608Metric
R40, R41: 10k; R_0603_1608Metric
R1111, R1112, R1121, R1122, R1131, R1132, R1141, R1142, R1151, R1152: 1k; R_0603_1608Metric
RV1, RV2, RV3, RV4, RV5: RK09L1140A5L
SW1, SW2, SW3, SW4, SW5: SS14MDP2

Connections:
+3V3A: R40.1, RV1.3 (HIGH), RV2.3 (HIGH), RV3.3 (HIGH), RV4.3 (HIGH), RV5.3 (HIGH), SW1.4 (THROW_RIGHT), SW2.4 (THROW_RIGHT), SW3.4 (THROW_RIGHT), SW4.4 (THROW_RIGHT), SW5.4 (THROW_RIGHT)
CH01_RANGE: C1112.1, R1112.2
CH01_RANGE_W: R1112.1, SW1.3 (COMMON)
CH01_TIME: C1111.1, R1111.2
CH01_TIME_W: R1111.1, RV1.2 (WIPER)
CH02_RANGE: C1122.1, R1122.2
CH02_RANGE_W: R1122.1, SW2.3 (COMMON)
CH02_TIME: C1121.1, R1121.2
CH02_TIME_W: R1121.1, RV2.2 (WIPER)
CH03_RANGE: C1132.1, R1132.2
CH03_RANGE_W: R1132.1, SW3.3 (COMMON)
CH03_TIME: C1131.1, R1131.2
CH03_TIME_W: R1131.1, RV3.2 (WIPER)
CH04_RANGE: C1142.1, R1142.2
CH04_RANGE_W: R1142.1, SW4.3 (COMMON)
CH04_TIME: C1141.1, R1141.2
CH04_TIME_W: R1141.1, RV4.2 (WIPER)
CH05_RANGE: C1152.1, R1152.2
CH05_RANGE_W: R1152.1, SW5.3 (COMMON)
CH05_TIME: C1151.1, R1151.2
CH05_TIME_W: R1151.1, RV5.2 (WIPER)
GND: C1111.2, C1112.2, C1121.2, C1122.2, C1131.2, C1132.2, C1141.2, C1142.2, C1151.2, C1152.2, R41.2, RV1.1 (LOW), RV2.1 (LOW), RV3.1 (LOW), RV4.1 (LOW), RV5.1 (LOW), SW1.1 (THROW_LEFT), SW2.1 (THROW_LEFT), SW3.1 (THROW_LEFT), SW4.1 (THROW_LEFT), SW5.1 (THROW_LEFT)
RANGE_MID: R40.2, R41.1, SW1.2 (THROW_CENTER), SW2.2 (THROW_CENTER), SW3.2 (THROW_CENTER), SW4.2 (THROW_CENTER), SW5.2 (THROW_CENTER)

Notes on the sheet:
NOT FOR FABRICATION - exact footprints and interface gates remain OPEN
