Takazudo/zudo-scope10/hardware/kicad/controls-right.kicad_sch

## KiCad design hardware/kicad/controls-right.kicad_sch (2026-09-26)

Schematic: controls-right.kicad_sch

Parts:
C51, C52, C1161, C1162, C1171, C1172, C1181, C1182, C1191, C1192, C1201, C1202: 100nF; C_0603_1608Metric
R51, R52: 10k; R_0603_1608Metric
R1161, R1162, R1171, R1172, R1181, R1182, R1191, R1192, R1201, R1202: 1k; R_0603_1608Metric
RV6, RV7, RV8, RV9, RV10: RK09L1140A5L
SW6, SW7, SW8, SW9, SW10: SS14MDP2
SW11, SW12: TS-1088-AR02016; SW_XUNPU_TS1088_AR02016_REVIEW

Connections:
+3V3A: RV6.3 (HIGH), RV7.3 (HIGH), RV8.3 (HIGH), RV9.3 (HIGH), RV10.3 (HIGH), SW6.4 (THROW_RIGHT), SW7.4 (THROW_RIGHT), SW8.4 (THROW_RIGHT), SW9.4 (THROW_RIGHT), SW10.4 (THROW_RIGHT)
+3V3D: R51.1, R52.1
CH06_RANGE: C1162.1, R1162.2
CH06_RANGE_W: R1162.1, SW6.3 (COMMON)
CH06_TIME: C1161.1, R1161.2
CH06_TIME_W: R1161.1, RV6.2 (WIPER)
CH07_RANGE: C1172.1, R1172.2
CH07_RANGE_W: R1172.1, SW7.3 (COMMON)
CH07_TIME: C1171.1, R1171.2
CH07_TIME_W: R1171.1, RV7.2 (WIPER)
CH08_RANGE: C1182.1, R1182.2
CH08_RANGE_W: R1182.1, SW8.3 (COMMON)
CH08_TIME: C1181.1, R1181.2
CH08_TIME_W: R1181.1, RV8.2 (WIPER)
CH09_RANGE: C1192.1, R1192.2
CH09_RANGE_W: R1192.1, SW9.3 (COMMON)
CH09_TIME: C1191.1, R1191.2
CH09_TIME_W: R1191.1, RV9.2 (WIPER)
CH10_RANGE: C1202.1, R1202.2
CH10_RANGE_W: R1202.1, SW10.3 (COMMON)
CH10_TIME: C1201.1, R1201.2
CH10_TIME_W: R1201.1, RV10.2 (WIPER)
GND: C51.2, C52.2, C1161.2, C1162.2, C1171.2, C1172.2, C1181.2, C1182.2, C1191.2, C1192.2, C1201.2, C1202.2, RV6.1 (LOW), RV7.1 (LOW), RV8.1 (LOW), RV9.1 (LOW), RV10.1 (LOW), SW6.1 (THROW_LEFT), SW7.1 (THROW_LEFT), SW8.1 (THROW_LEFT), SW9.1 (THROW_LEFT), SW10.1 (THROW_LEFT), SW11.2 (NO_CONTACT_2), SW12.2 (NO_CONTACT_2)
HOLD_N: C51.1, R51.2, SW11.1 (NO_CONTACT_1)
LINK_N: C52.1, R52.2, SW12.1 (NO_CONTACT_1)
RANGE_MID: SW6.2 (THROW_CENTER), SW7.2 (THROW_CENTER), SW8.2 (THROW_CENTER), SW9.2 (THROW_CENTER), SW10.2 (THROW_CENTER)

Notes on the sheet:
NOT FOR FABRICATION - exact footprints and interface gates remain OPEN
