Takazudo/zudo-scope10/hardware/kicad/inputs-01-02.kicad_sch

## KiCad design hardware/kicad/inputs-01-02.kicad_sch (2026-09-26)

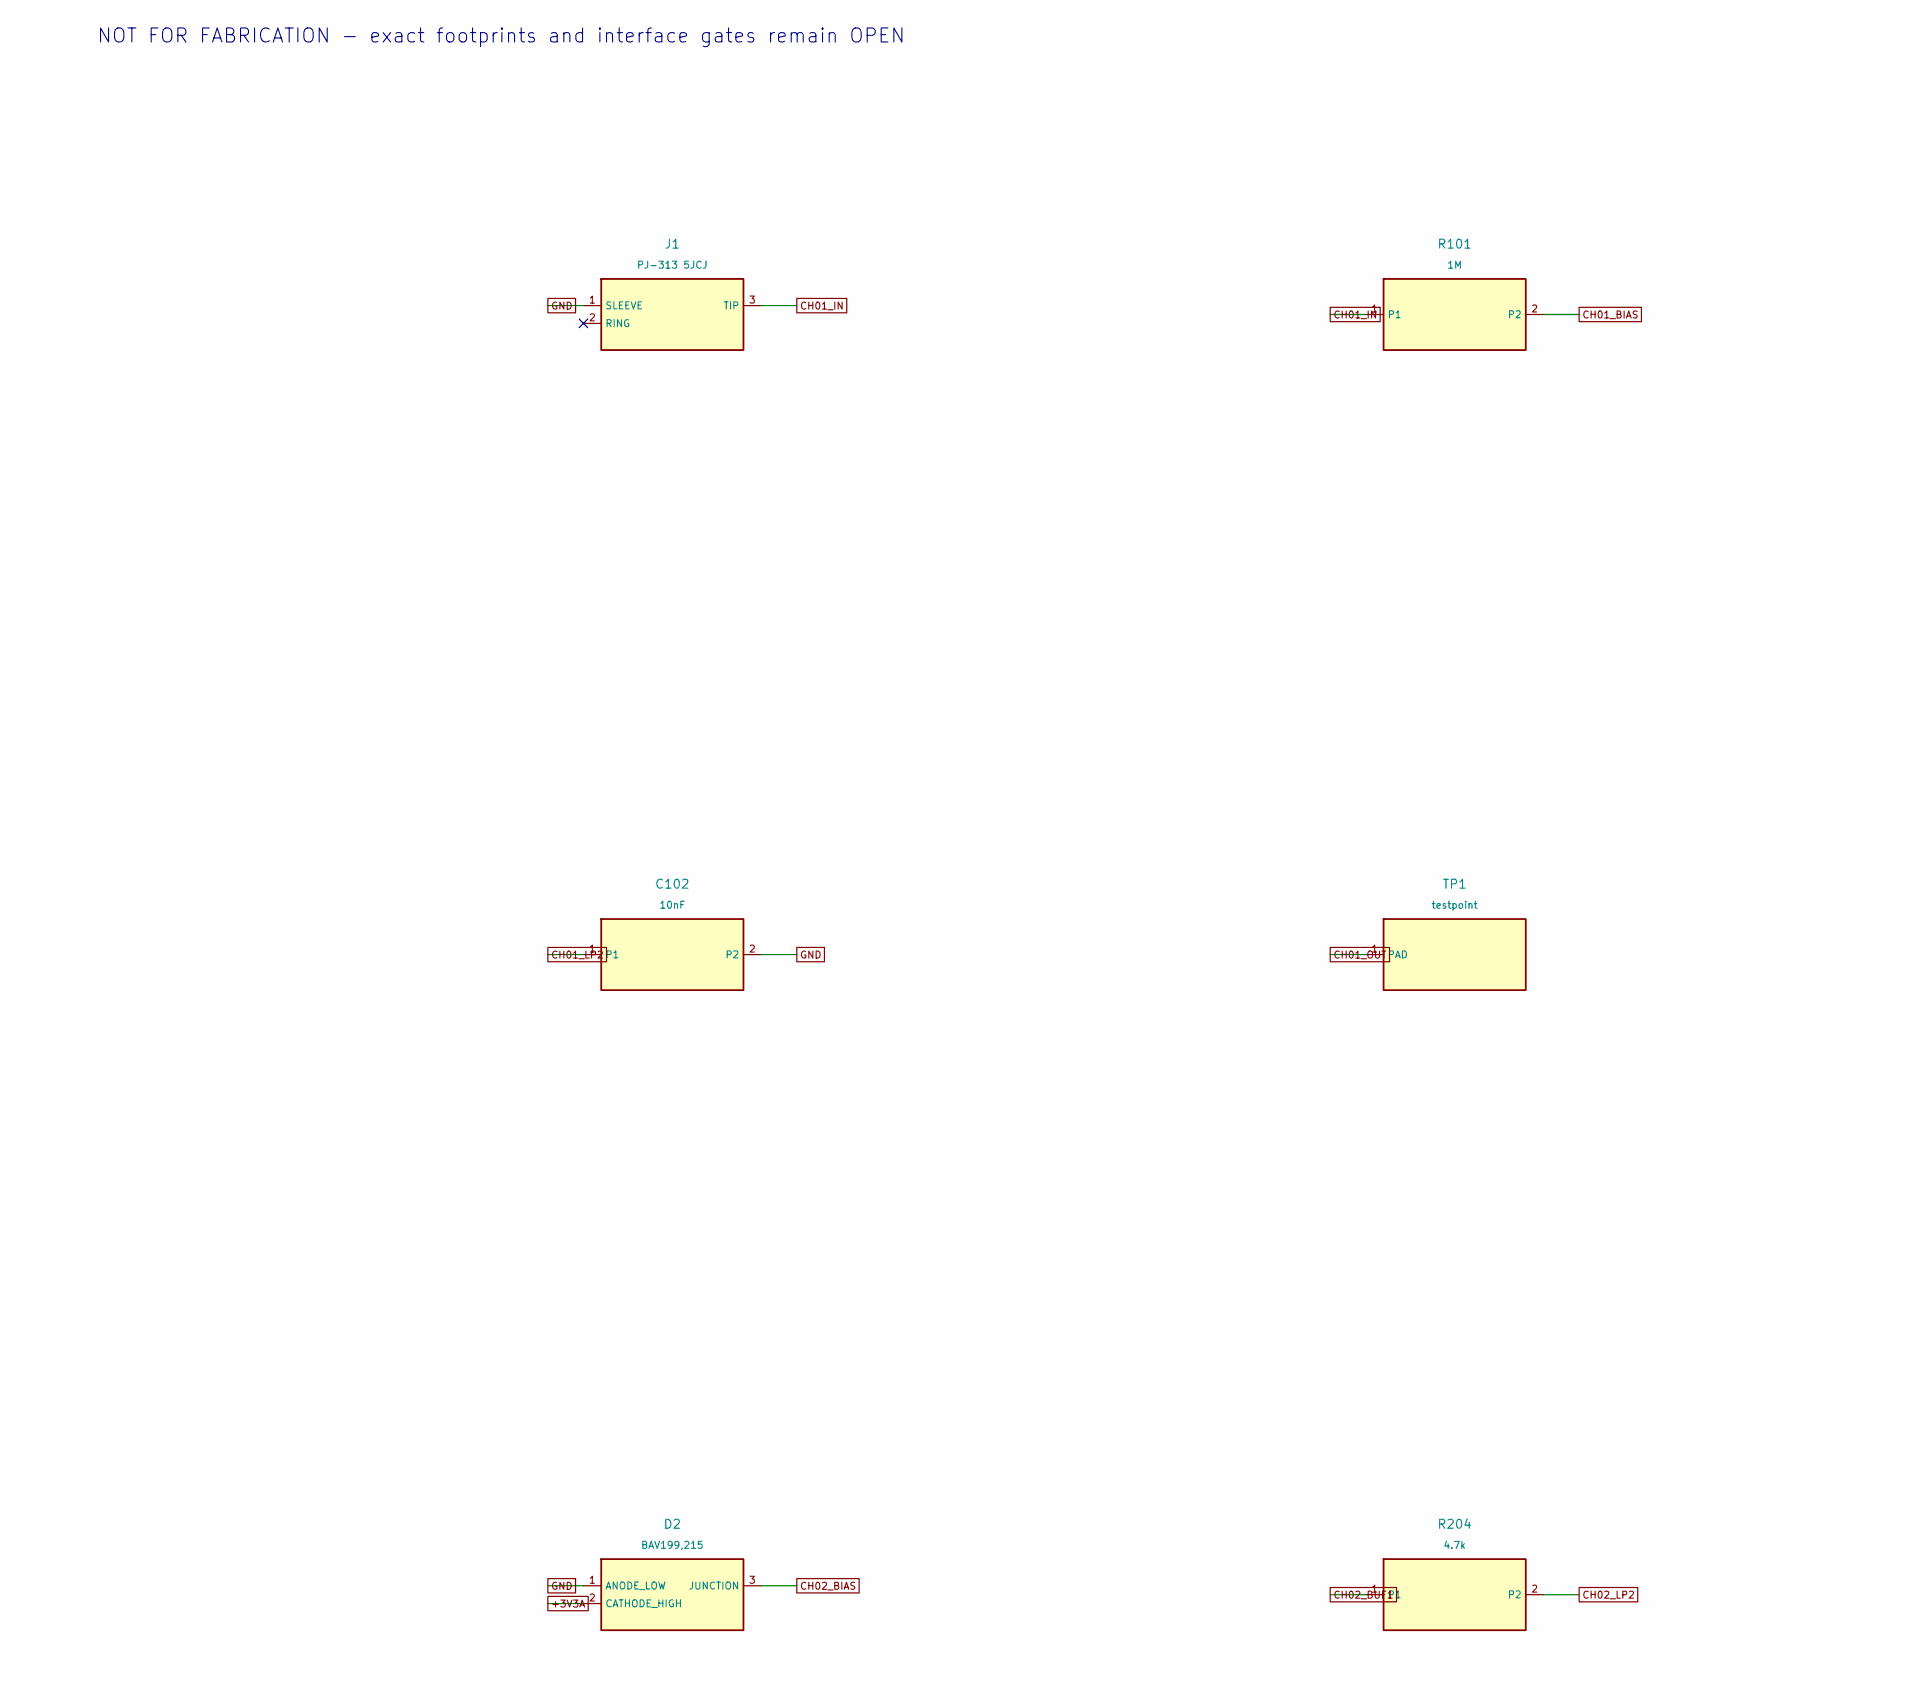
[picture p17: schematic inputs-01-02.kicad_sch, part in row 1, column 1]

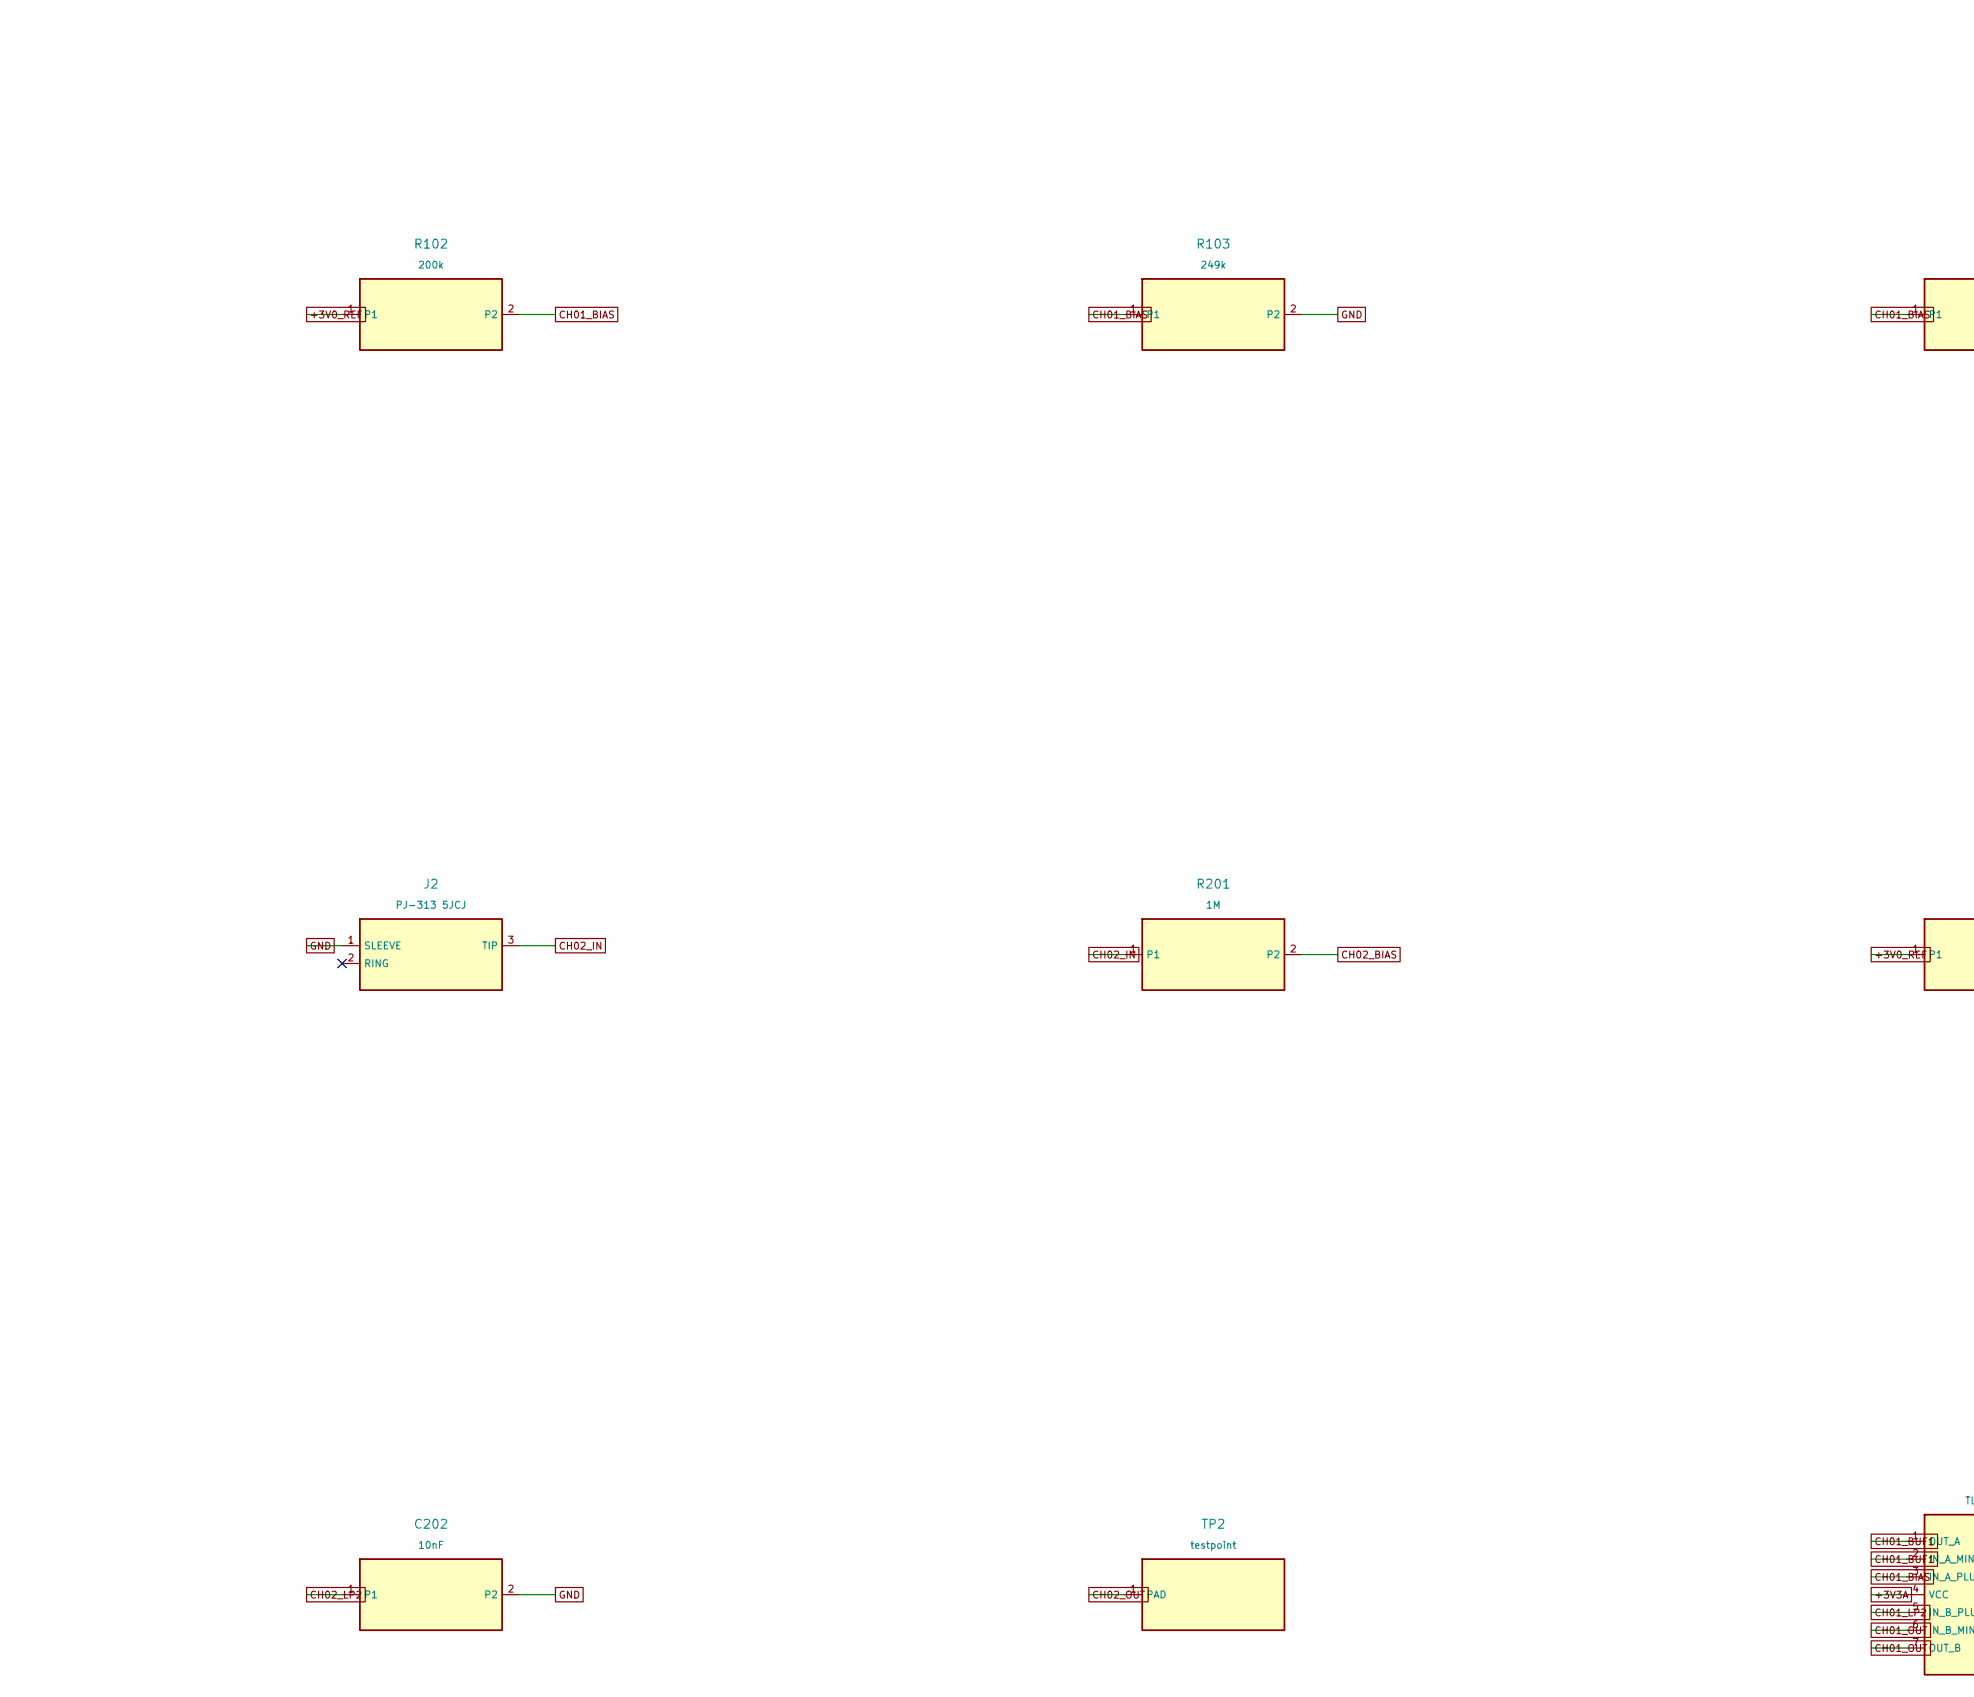
[picture p18: schematic inputs-01-02.kicad_sch, part in row 1, column 2]

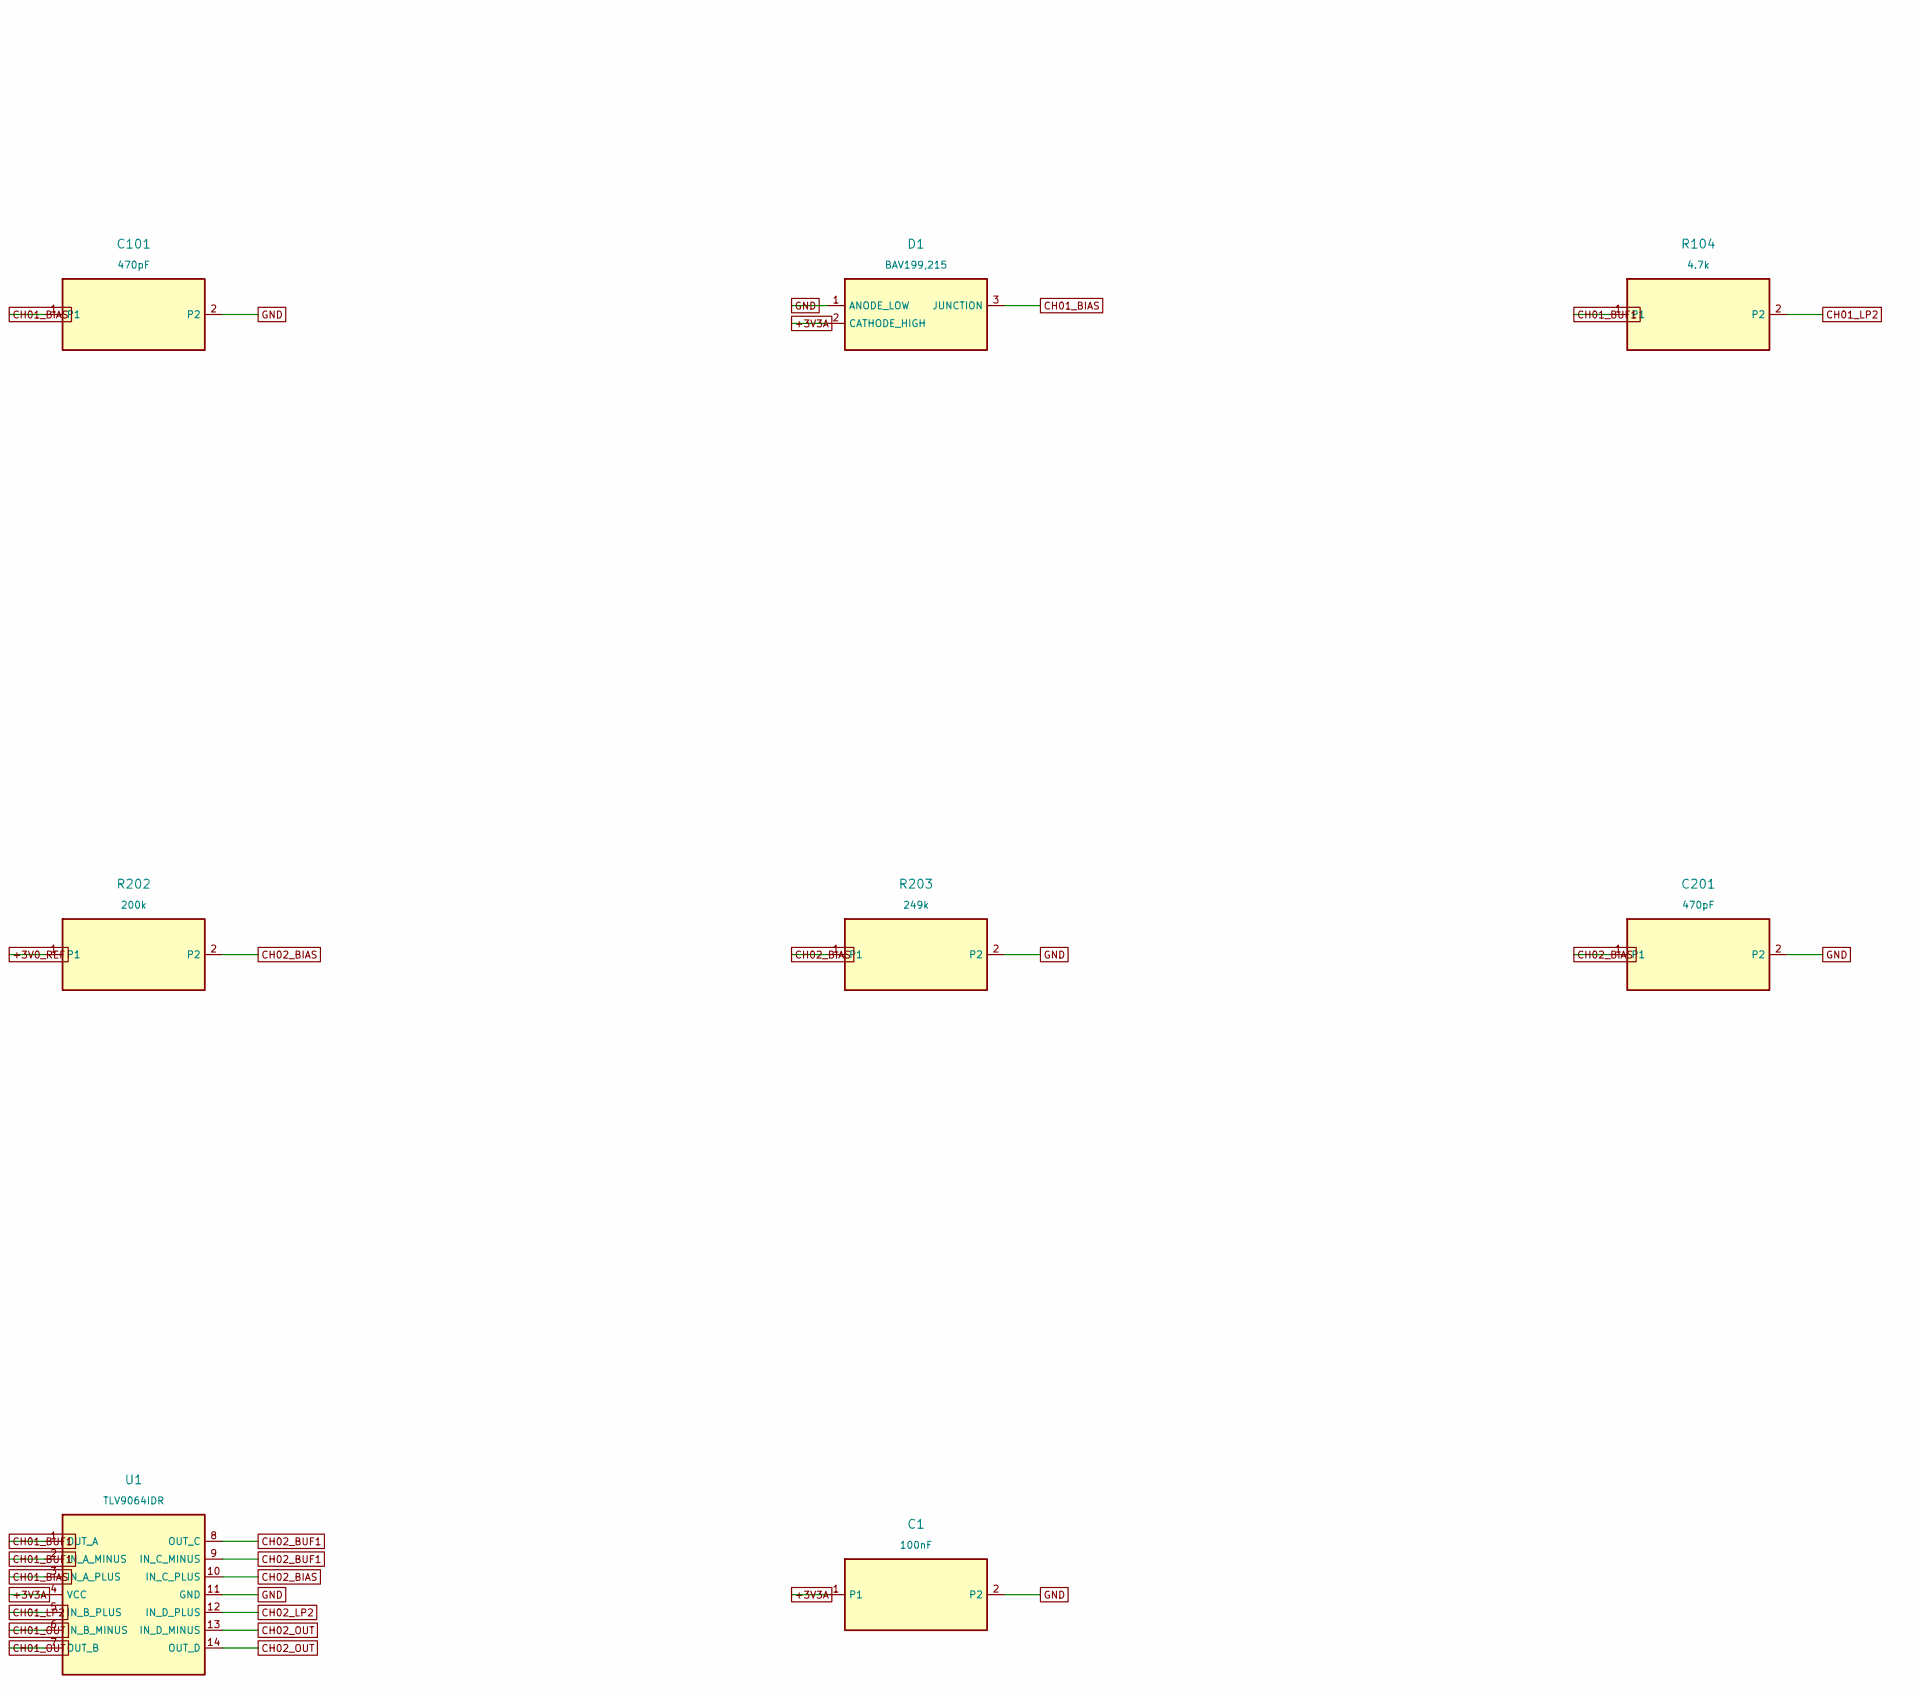
[picture p19: schematic inputs-01-02.kicad_sch, part in row 1, column 3]

Parts:
C1: 100nF; C_0603_1608Metric
C101, C201: 470pF; C_0603_1608Metric
C102, C202: 10nF; C_0603_1608Metric
D1, D2: BAV199,215; SOT-23
J1, J2: PJ-313 5JCJ
R101, R201: 1M; R_0603_1608Metric
R102, R202: 200k; R_0603_1608Metric
R103, R203: 249k; R_0603_1608Metric
R104, R204: 4.7k; R_0603_1608Metric
TP1, TP2: testpoint; TestPoint_Pad_D1.0mm
U1: TLV9064IDR; SOIC-14_3.9x8.7mm_P1.27mm

Connections:
+3V0_REF: R102.1, R202.1
+3V3A: C1.1, D1.2 (CATHODE_HIGH), D2.2 (CATHODE_HIGH), U1.4 (VCC)
CH01_BIAS: C101.1, D1.3 (JUNCTION), R101.2, R102.2, R103.1, U1.3 (IN_A_PLUS)
CH01_BUF1: R104.1, U1.1 (OUT_A), U1.2 (IN_A_MINUS)
CH01_IN: J1.3 (TIP), R101.1
CH01_LP2: C102.1, R104.2, U1.5 (IN_B_PLUS)
CH01_OUT: TP1.1, U1.6 (IN_B_MINUS), U1.7 (OUT_B)
CH02_BIAS: C201.1, D2.3 (JUNCTION), R201.2, R202.2, R203.1, U1.10 (IN_C_PLUS)
CH02_BUF1: R204.1, U1.8 (OUT_C), U1.9 (IN_C_MINUS)
CH02_IN: J2.3 (TIP), R201.1
CH02_LP2: C202.1, R204.2, U1.12 (IN_D_PLUS)
CH02_OUT: TP2.1, U1.13 (IN_D_MINUS), U1.14 (OUT_D)
GND: C1.2, C101.2, C102.2, C201.2, C202.2, D1.1 (ANODE_LOW), D2.1 (ANODE_LOW), J1.1 (SLEEVE), J2.1 (SLEEVE), R103.2, R203.2, U1.11 (GND)

Notes on the sheet:
NOT FOR FABRICATION - exact footprints and interface gates remain OPEN
