Takazudo/zudo-scope10/hardware/kicad/inputs-03-04.kicad_sch

## KiCad design hardware/kicad/inputs-03-04.kicad_sch (2026-09-26)

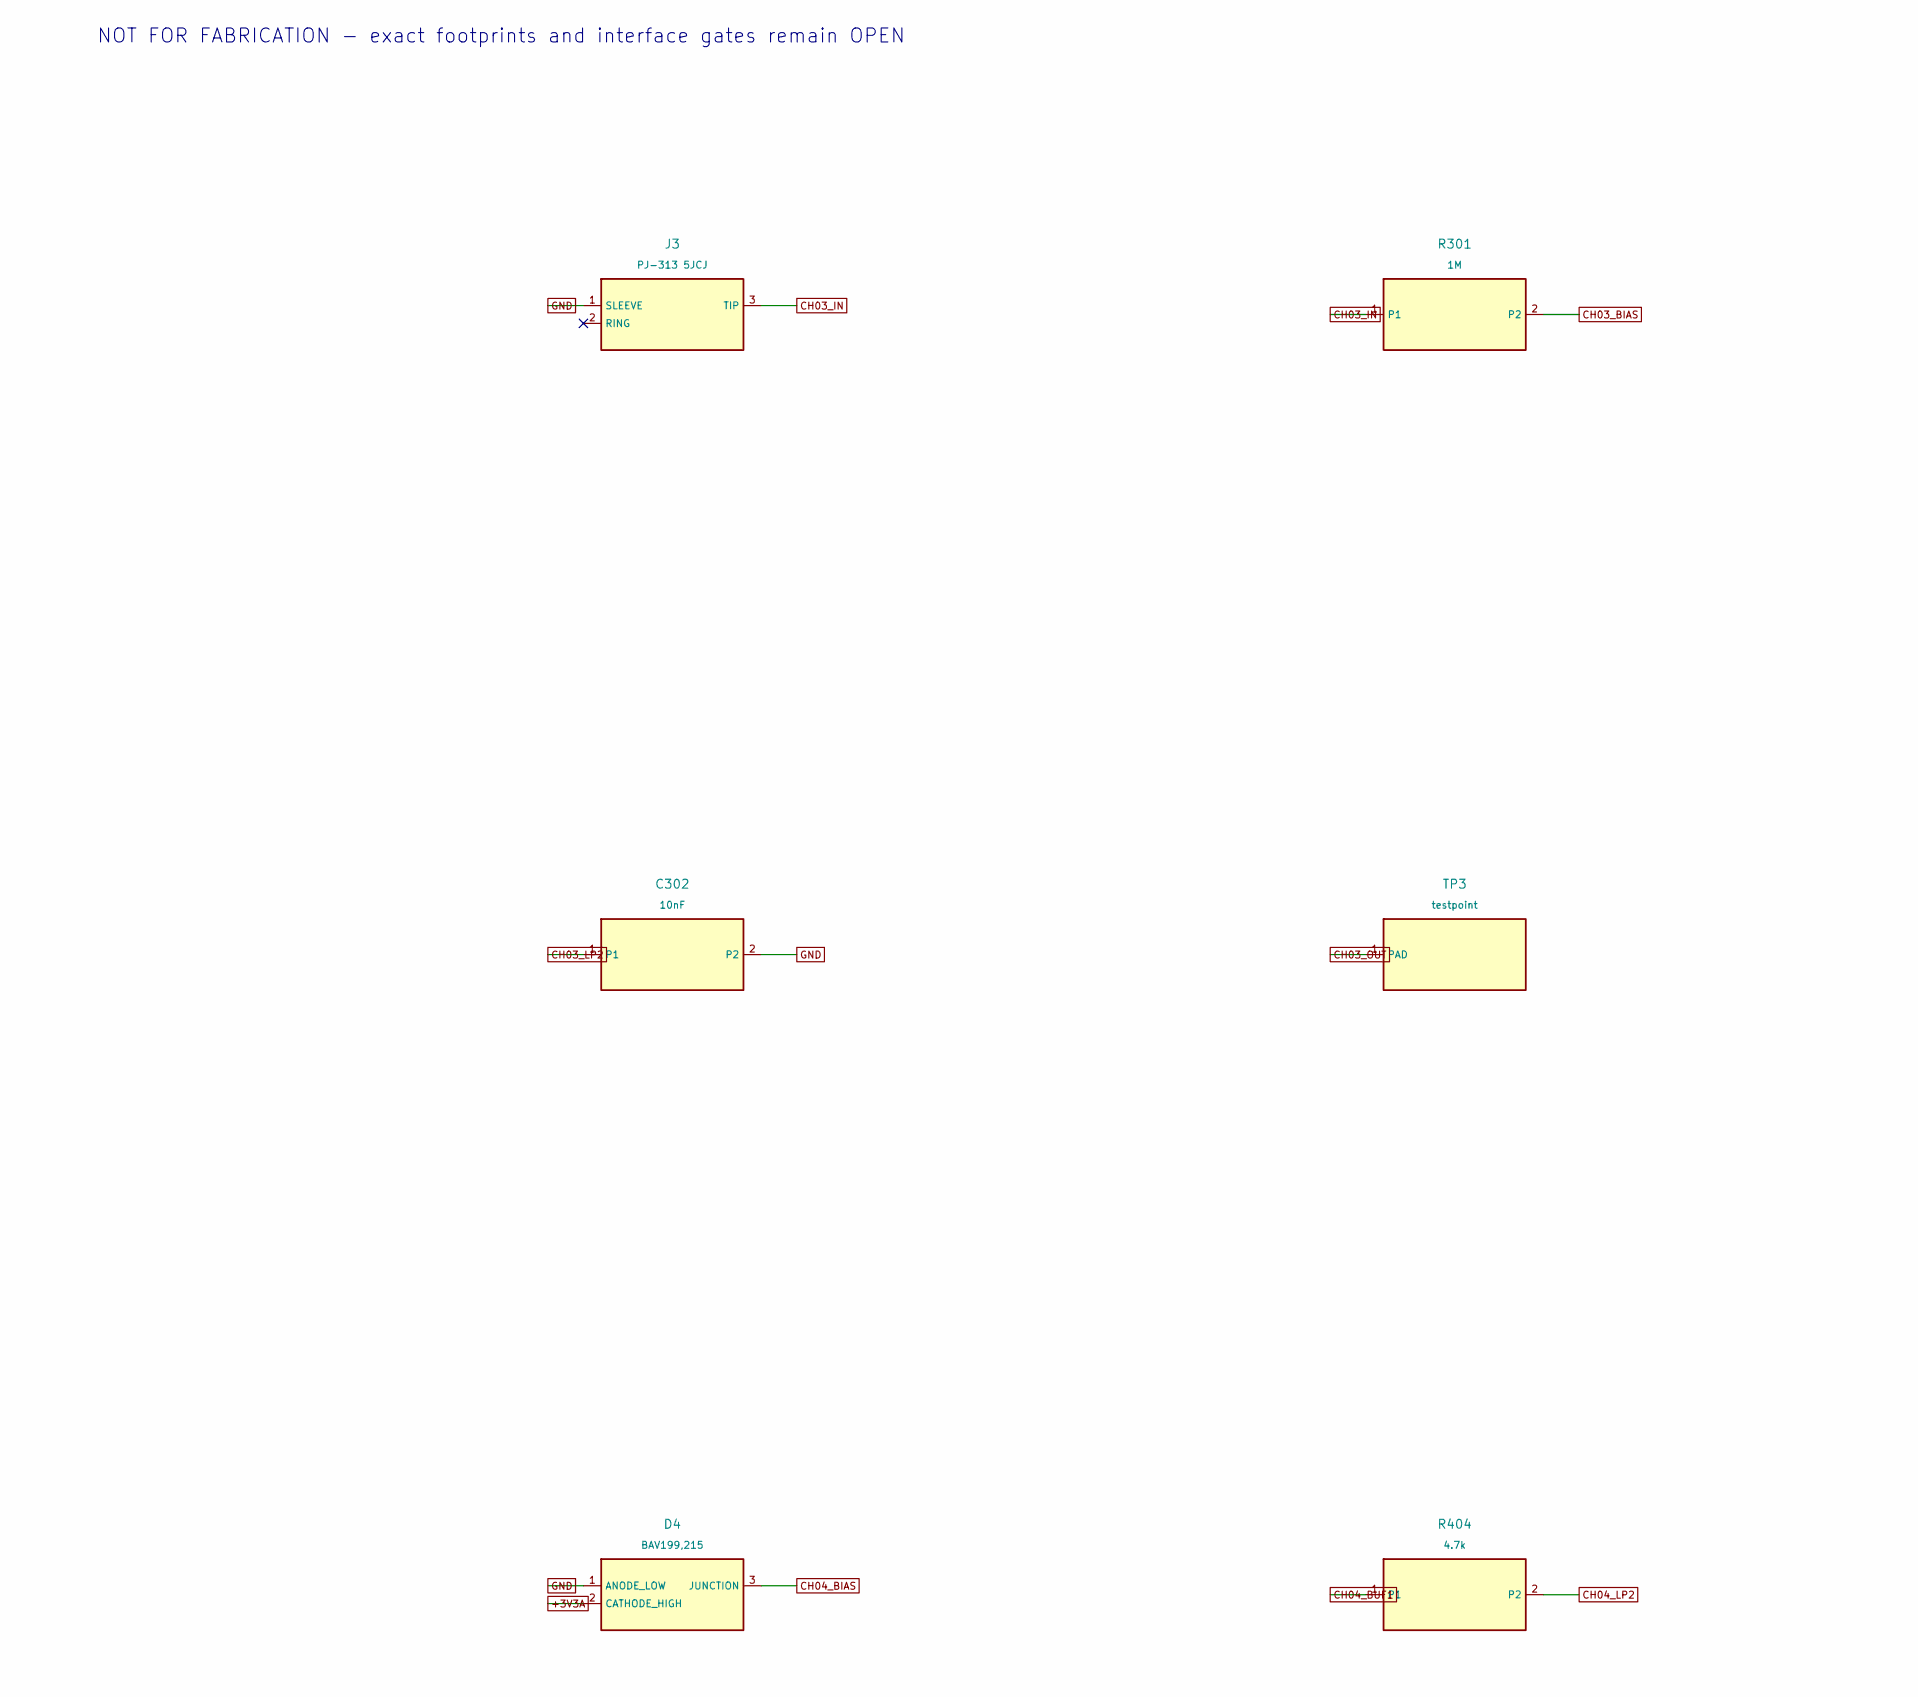
[picture p20: schematic inputs-03-04.kicad_sch, part in row 1, column 1]

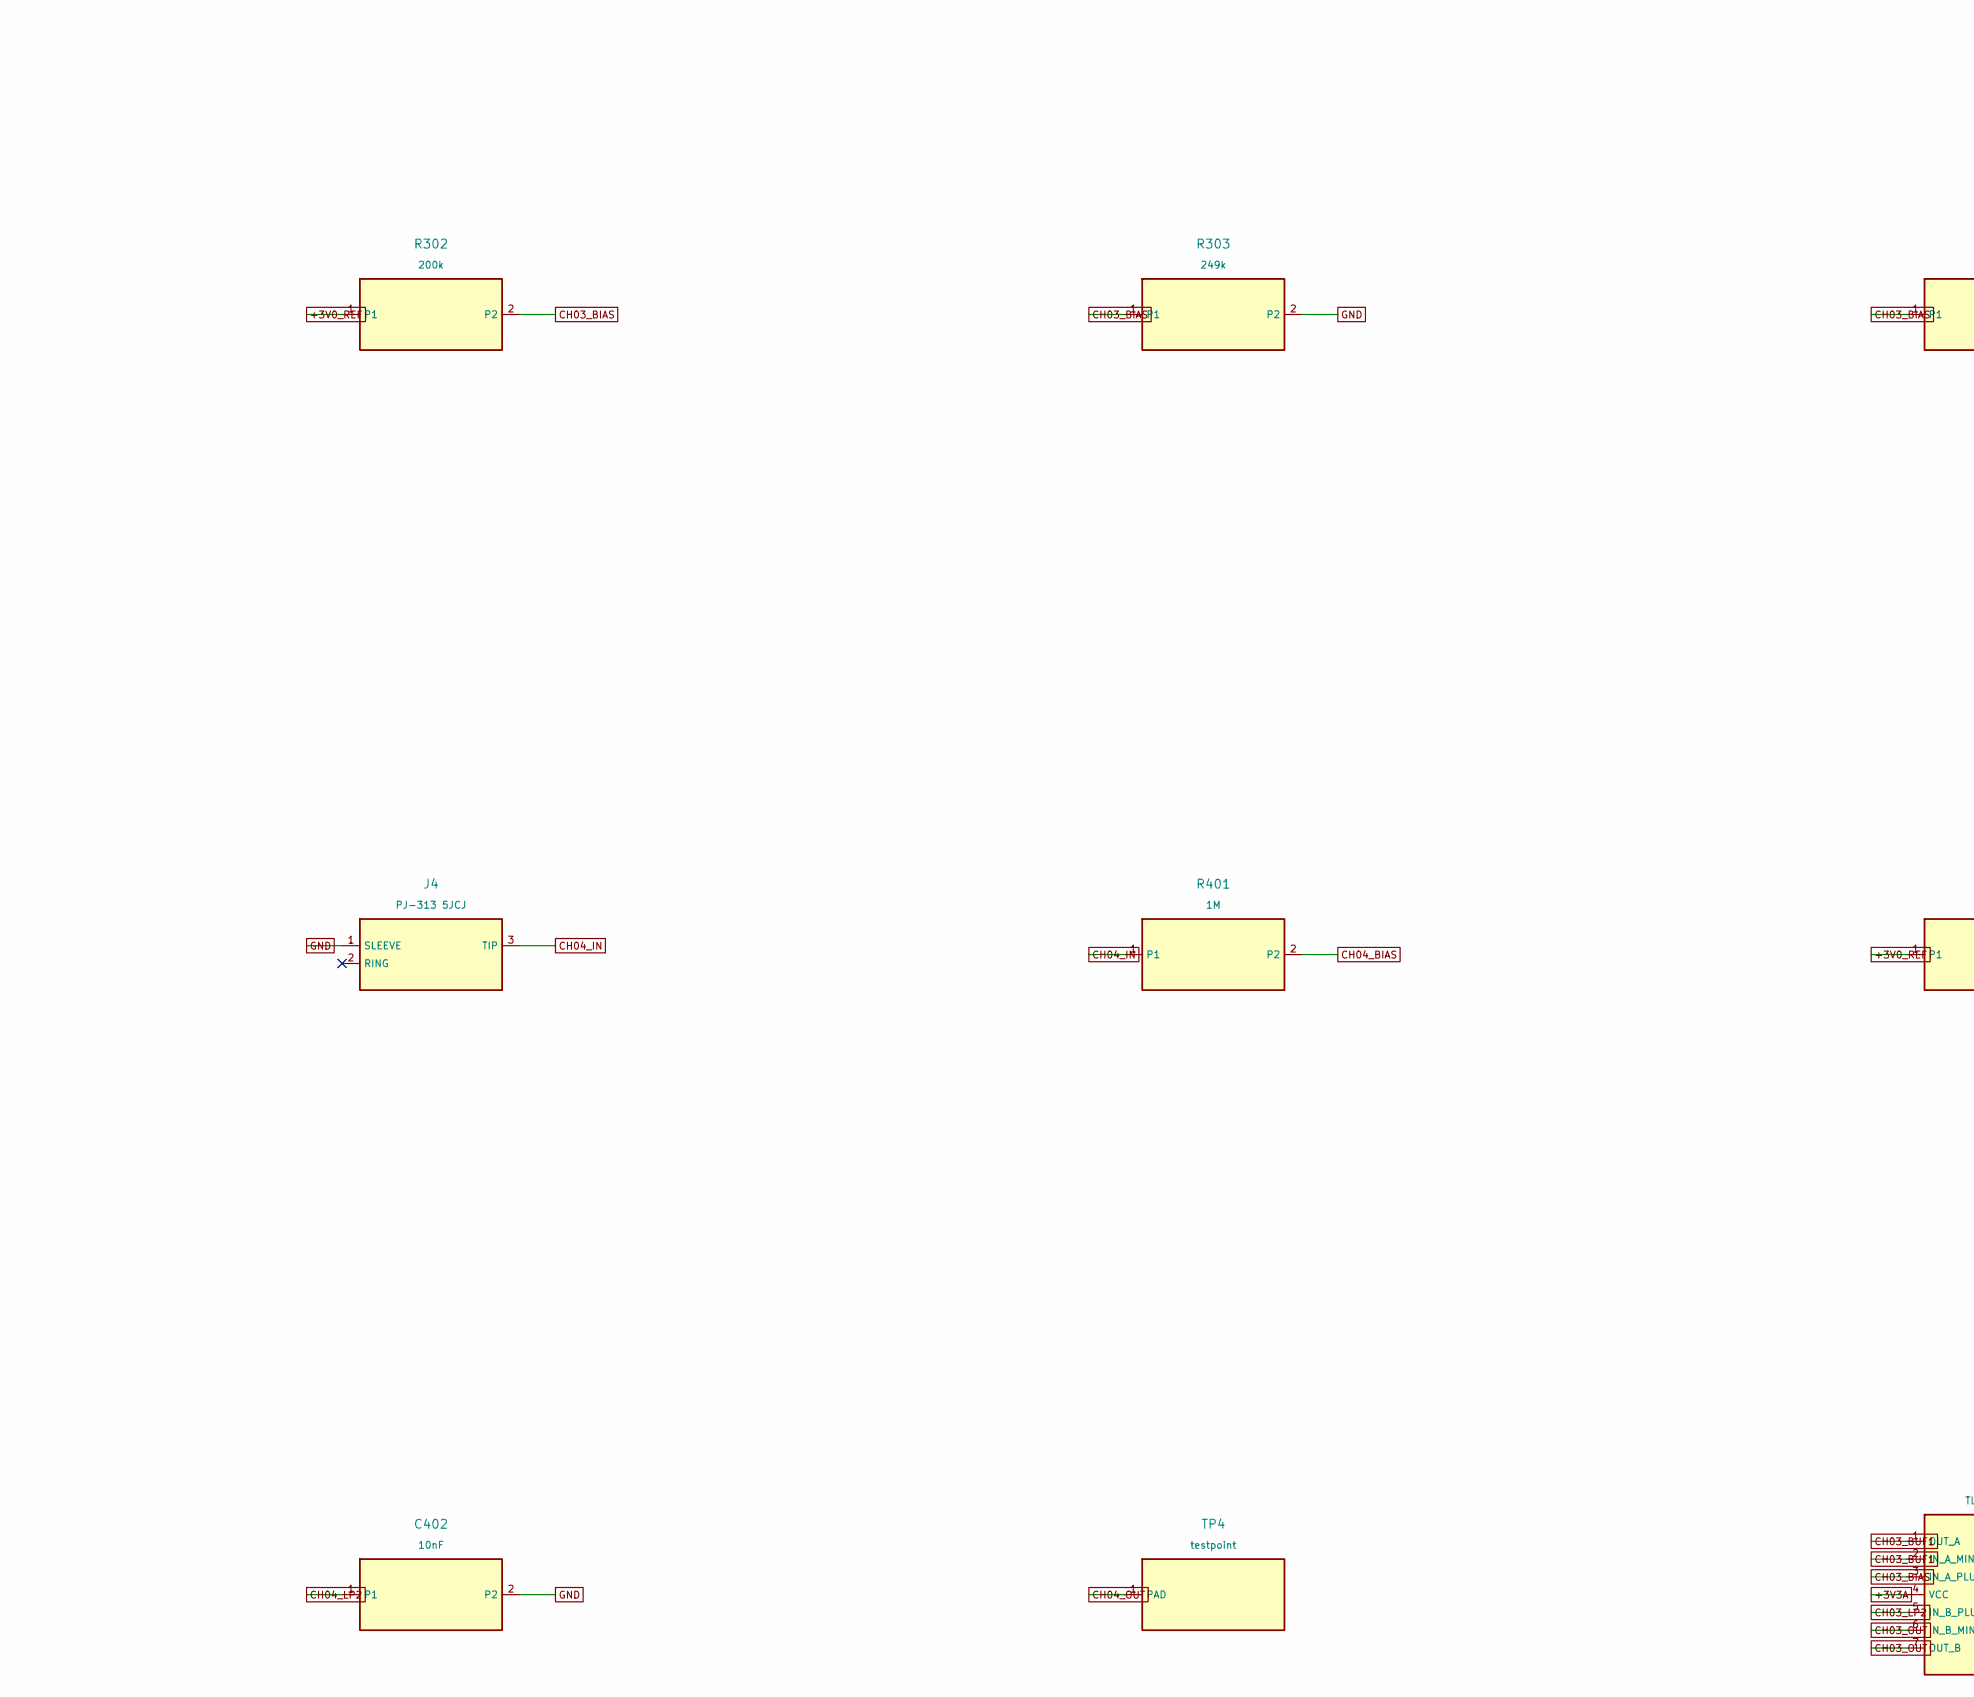
[picture p21: schematic inputs-03-04.kicad_sch, part in row 1, column 2]

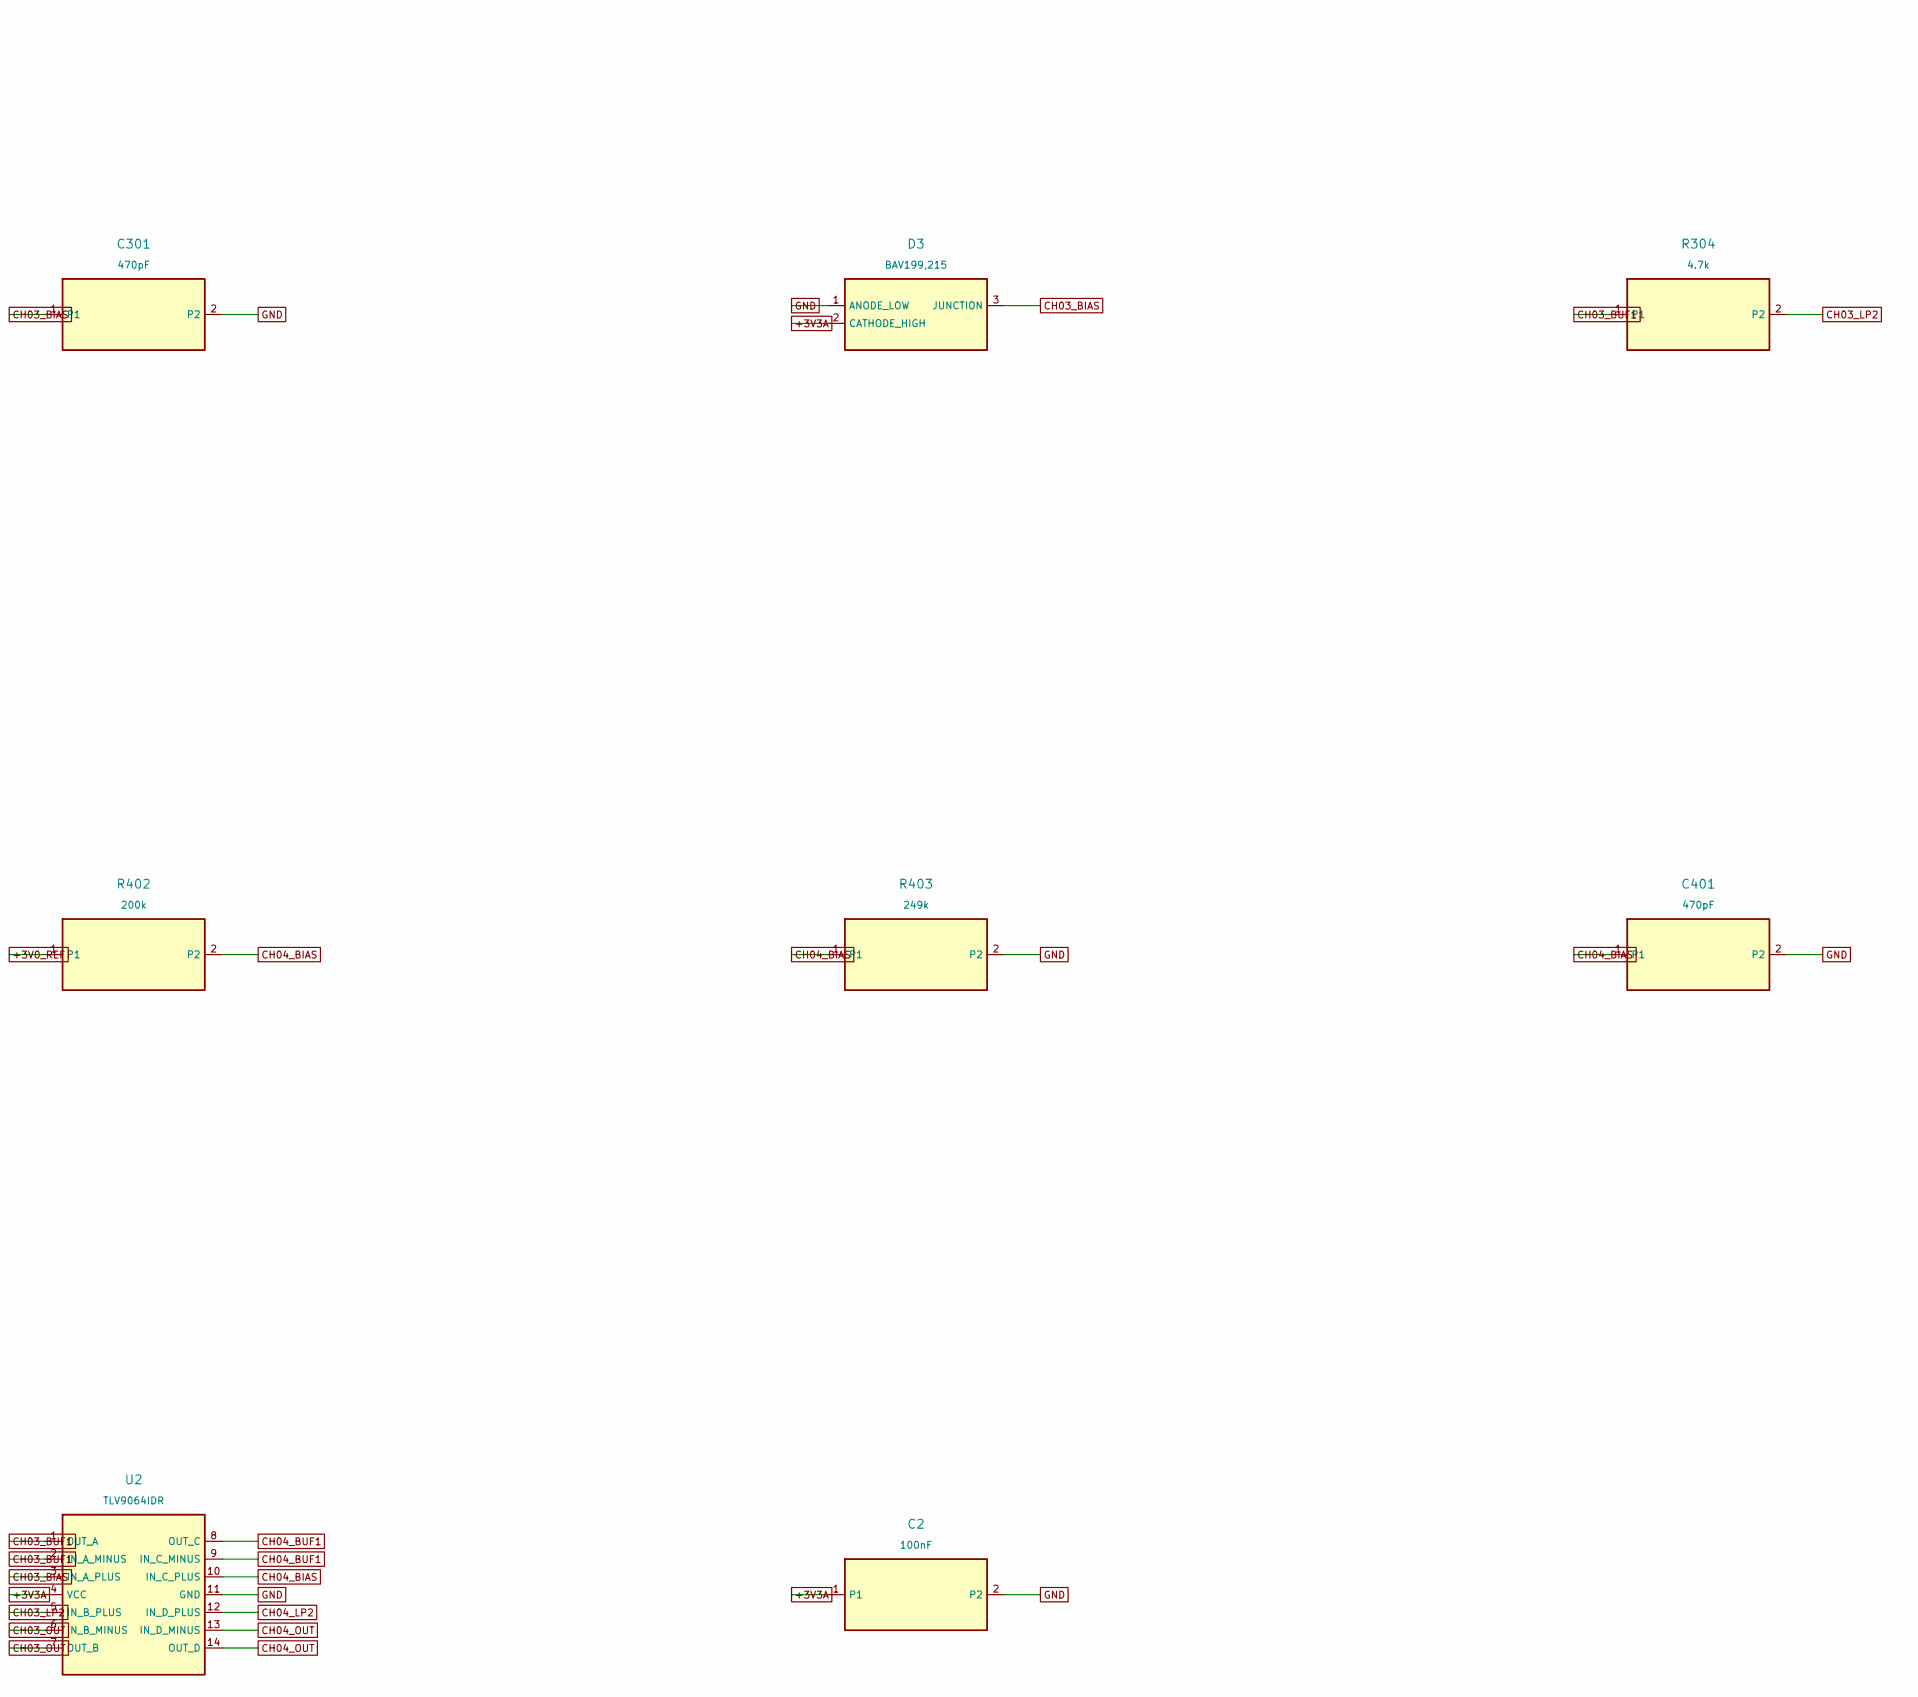
[picture p22: schematic inputs-03-04.kicad_sch, part in row 1, column 3]

Parts:
C2: 100nF; C_0603_1608Metric
C301, C401: 470pF; C_0603_1608Metric
C302, C402: 10nF; C_0603_1608Metric
D3, D4: BAV199,215; SOT-23
J3, J4: PJ-313 5JCJ
R301, R401: 1M; R_0603_1608Metric
R302, R402: 200k; R_0603_1608Metric
R303, R403: 249k; R_0603_1608Metric
R304, R404: 4.7k; R_0603_1608Metric
TP3, TP4: testpoint; TestPoint_Pad_D1.0mm
U2: TLV9064IDR; SOIC-14_3.9x8.7mm_P1.27mm

Connections:
+3V0_REF: R302.1, R402.1
+3V3A: C2.1, D3.2 (CATHODE_HIGH), D4.2 (CATHODE_HIGH), U2.4 (VCC)
CH03_BIAS: C301.1, D3.3 (JUNCTION), R301.2, R302.2, R303.1, U2.3 (IN_A_PLUS)
CH03_BUF1: R304.1, U2.1 (OUT_A), U2.2 (IN_A_MINUS)
CH03_IN: J3.3 (TIP), R301.1
CH03_LP2: C302.1, R304.2, U2.5 (IN_B_PLUS)
CH03_OUT: TP3.1, U2.6 (IN_B_MINUS), U2.7 (OUT_B)
CH04_BIAS: C401.1, D4.3 (JUNCTION), R401.2, R402.2, R403.1, U2.10 (IN_C_PLUS)
CH04_BUF1: R404.1, U2.8 (OUT_C), U2.9 (IN_C_MINUS)
CH04_IN: J4.3 (TIP), R401.1
CH04_LP2: C402.1, R404.2, U2.12 (IN_D_PLUS)
CH04_OUT: TP4.1, U2.13 (IN_D_MINUS), U2.14 (OUT_D)
GND: C2.2, C301.2, C302.2, C401.2, C402.2, D3.1 (ANODE_LOW), D4.1 (ANODE_LOW), J3.1 (SLEEVE), J4.1 (SLEEVE), R303.2, R403.2, U2.11 (GND)

Notes on the sheet:
NOT FOR FABRICATION - exact footprints and interface gates remain OPEN
