Takazudo/zudo-scope10/hardware/kicad/inputs-05-06.kicad_sch

## KiCad design hardware/kicad/inputs-05-06.kicad_sch (2026-09-26)

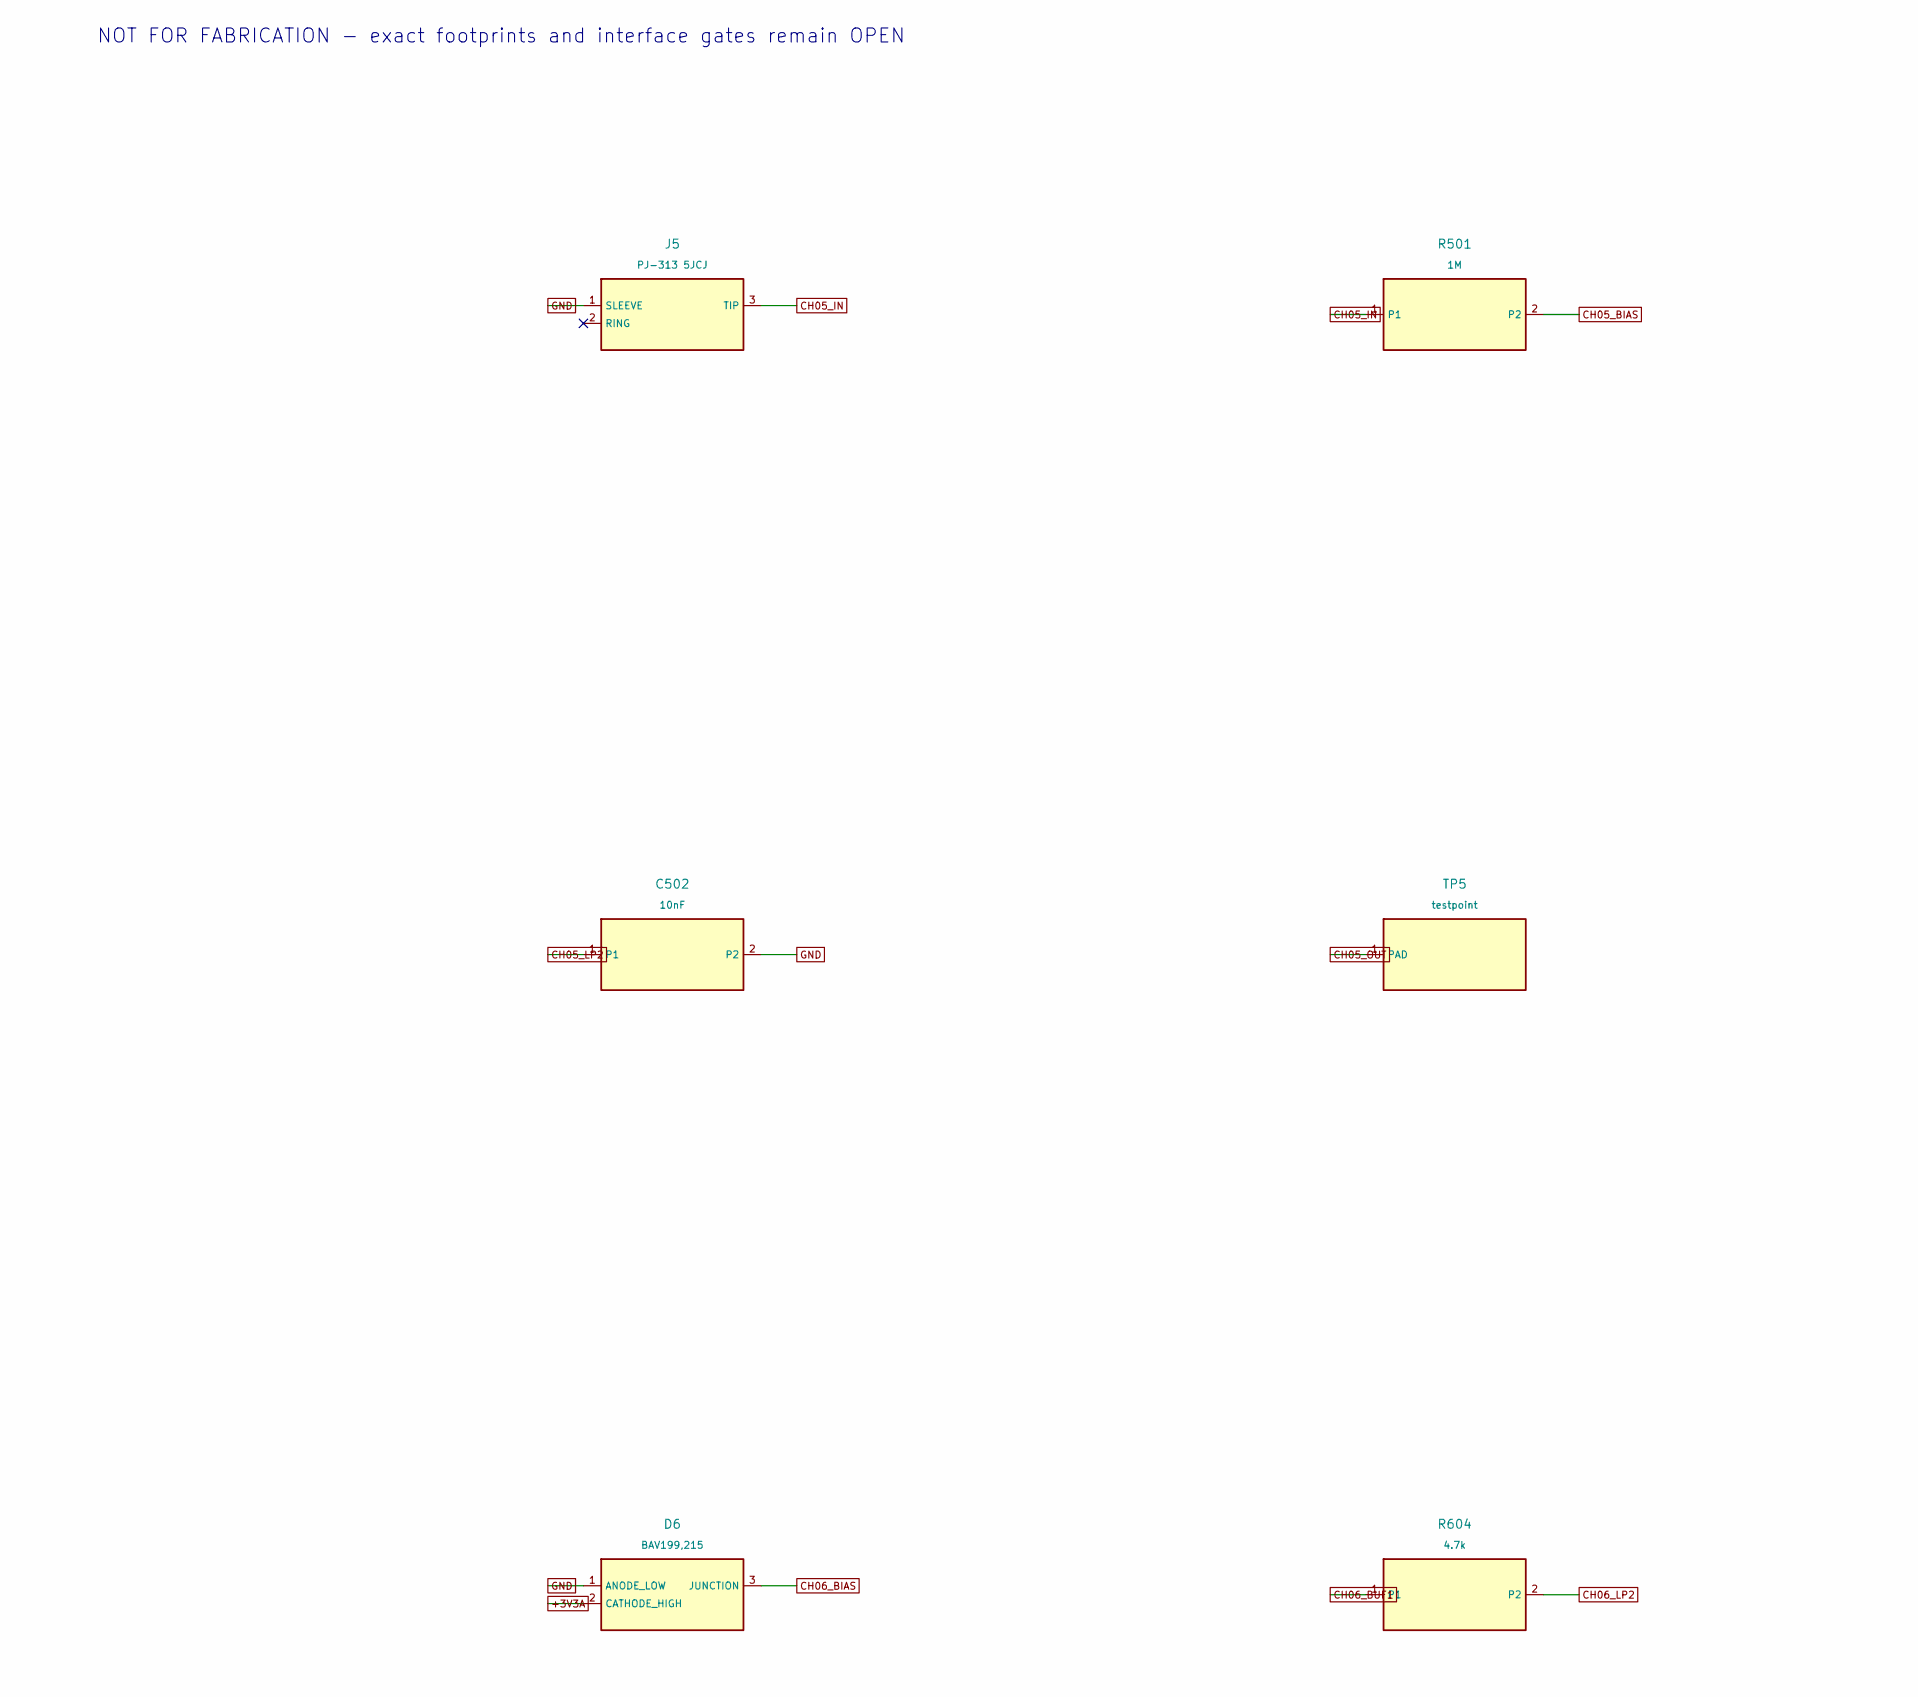
[picture p23: schematic inputs-05-06.kicad_sch, part in row 1, column 1]

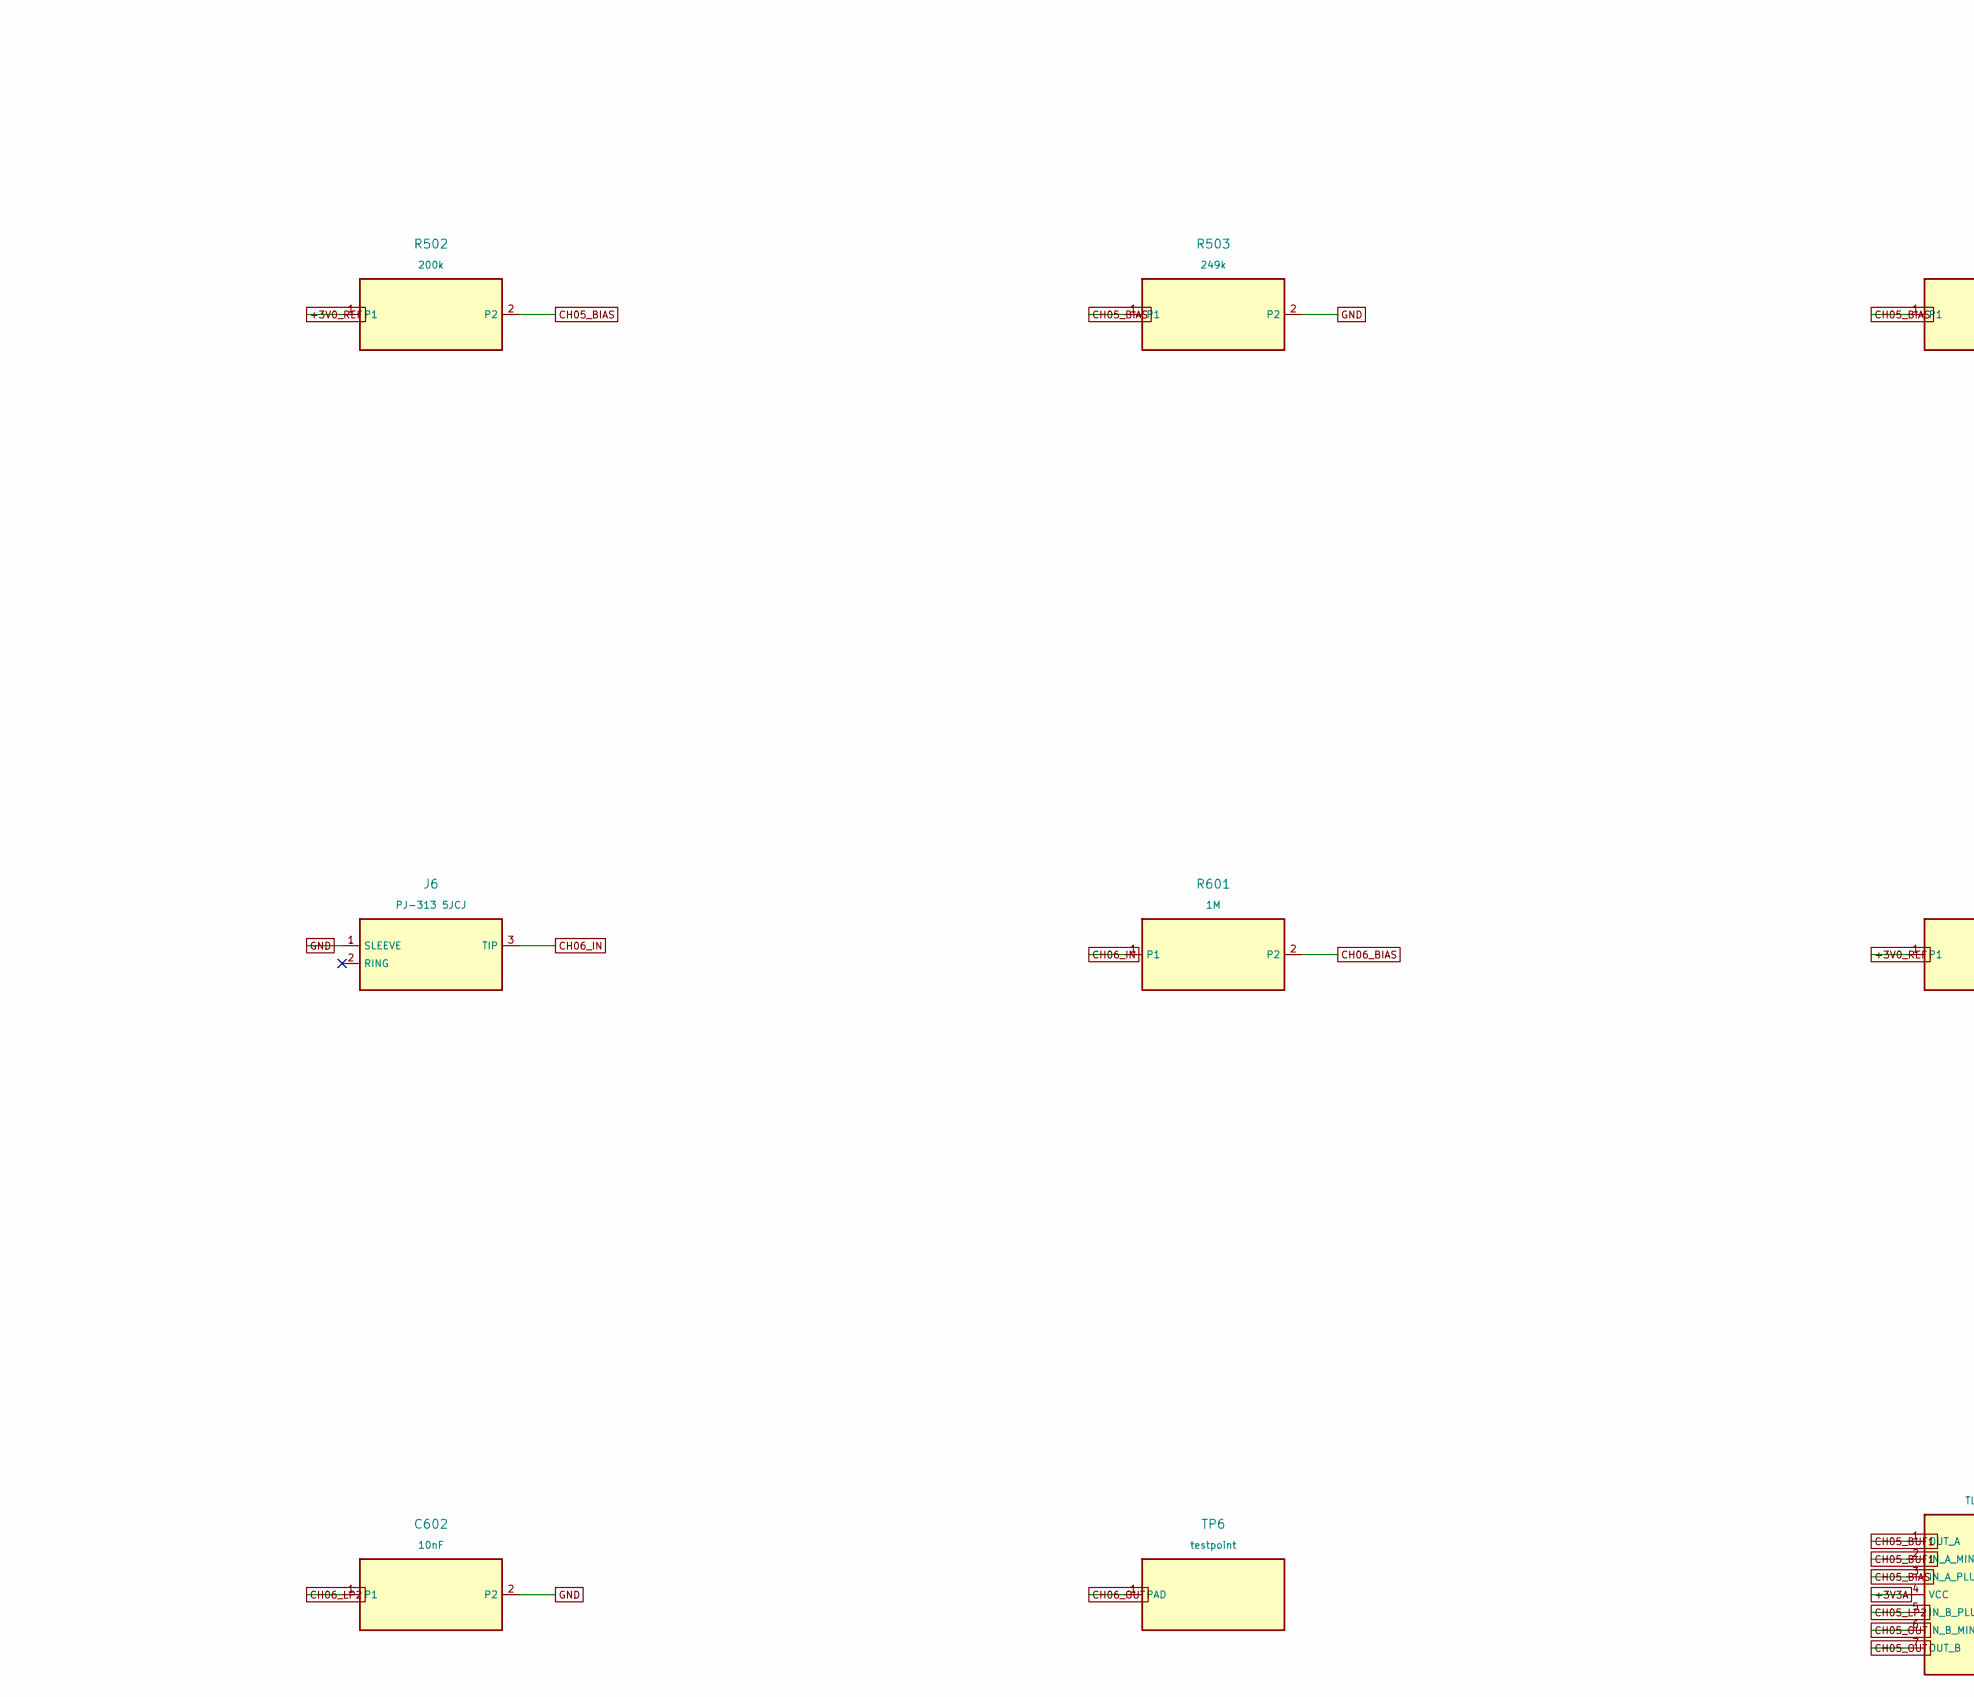
[picture p24: schematic inputs-05-06.kicad_sch, part in row 1, column 2]

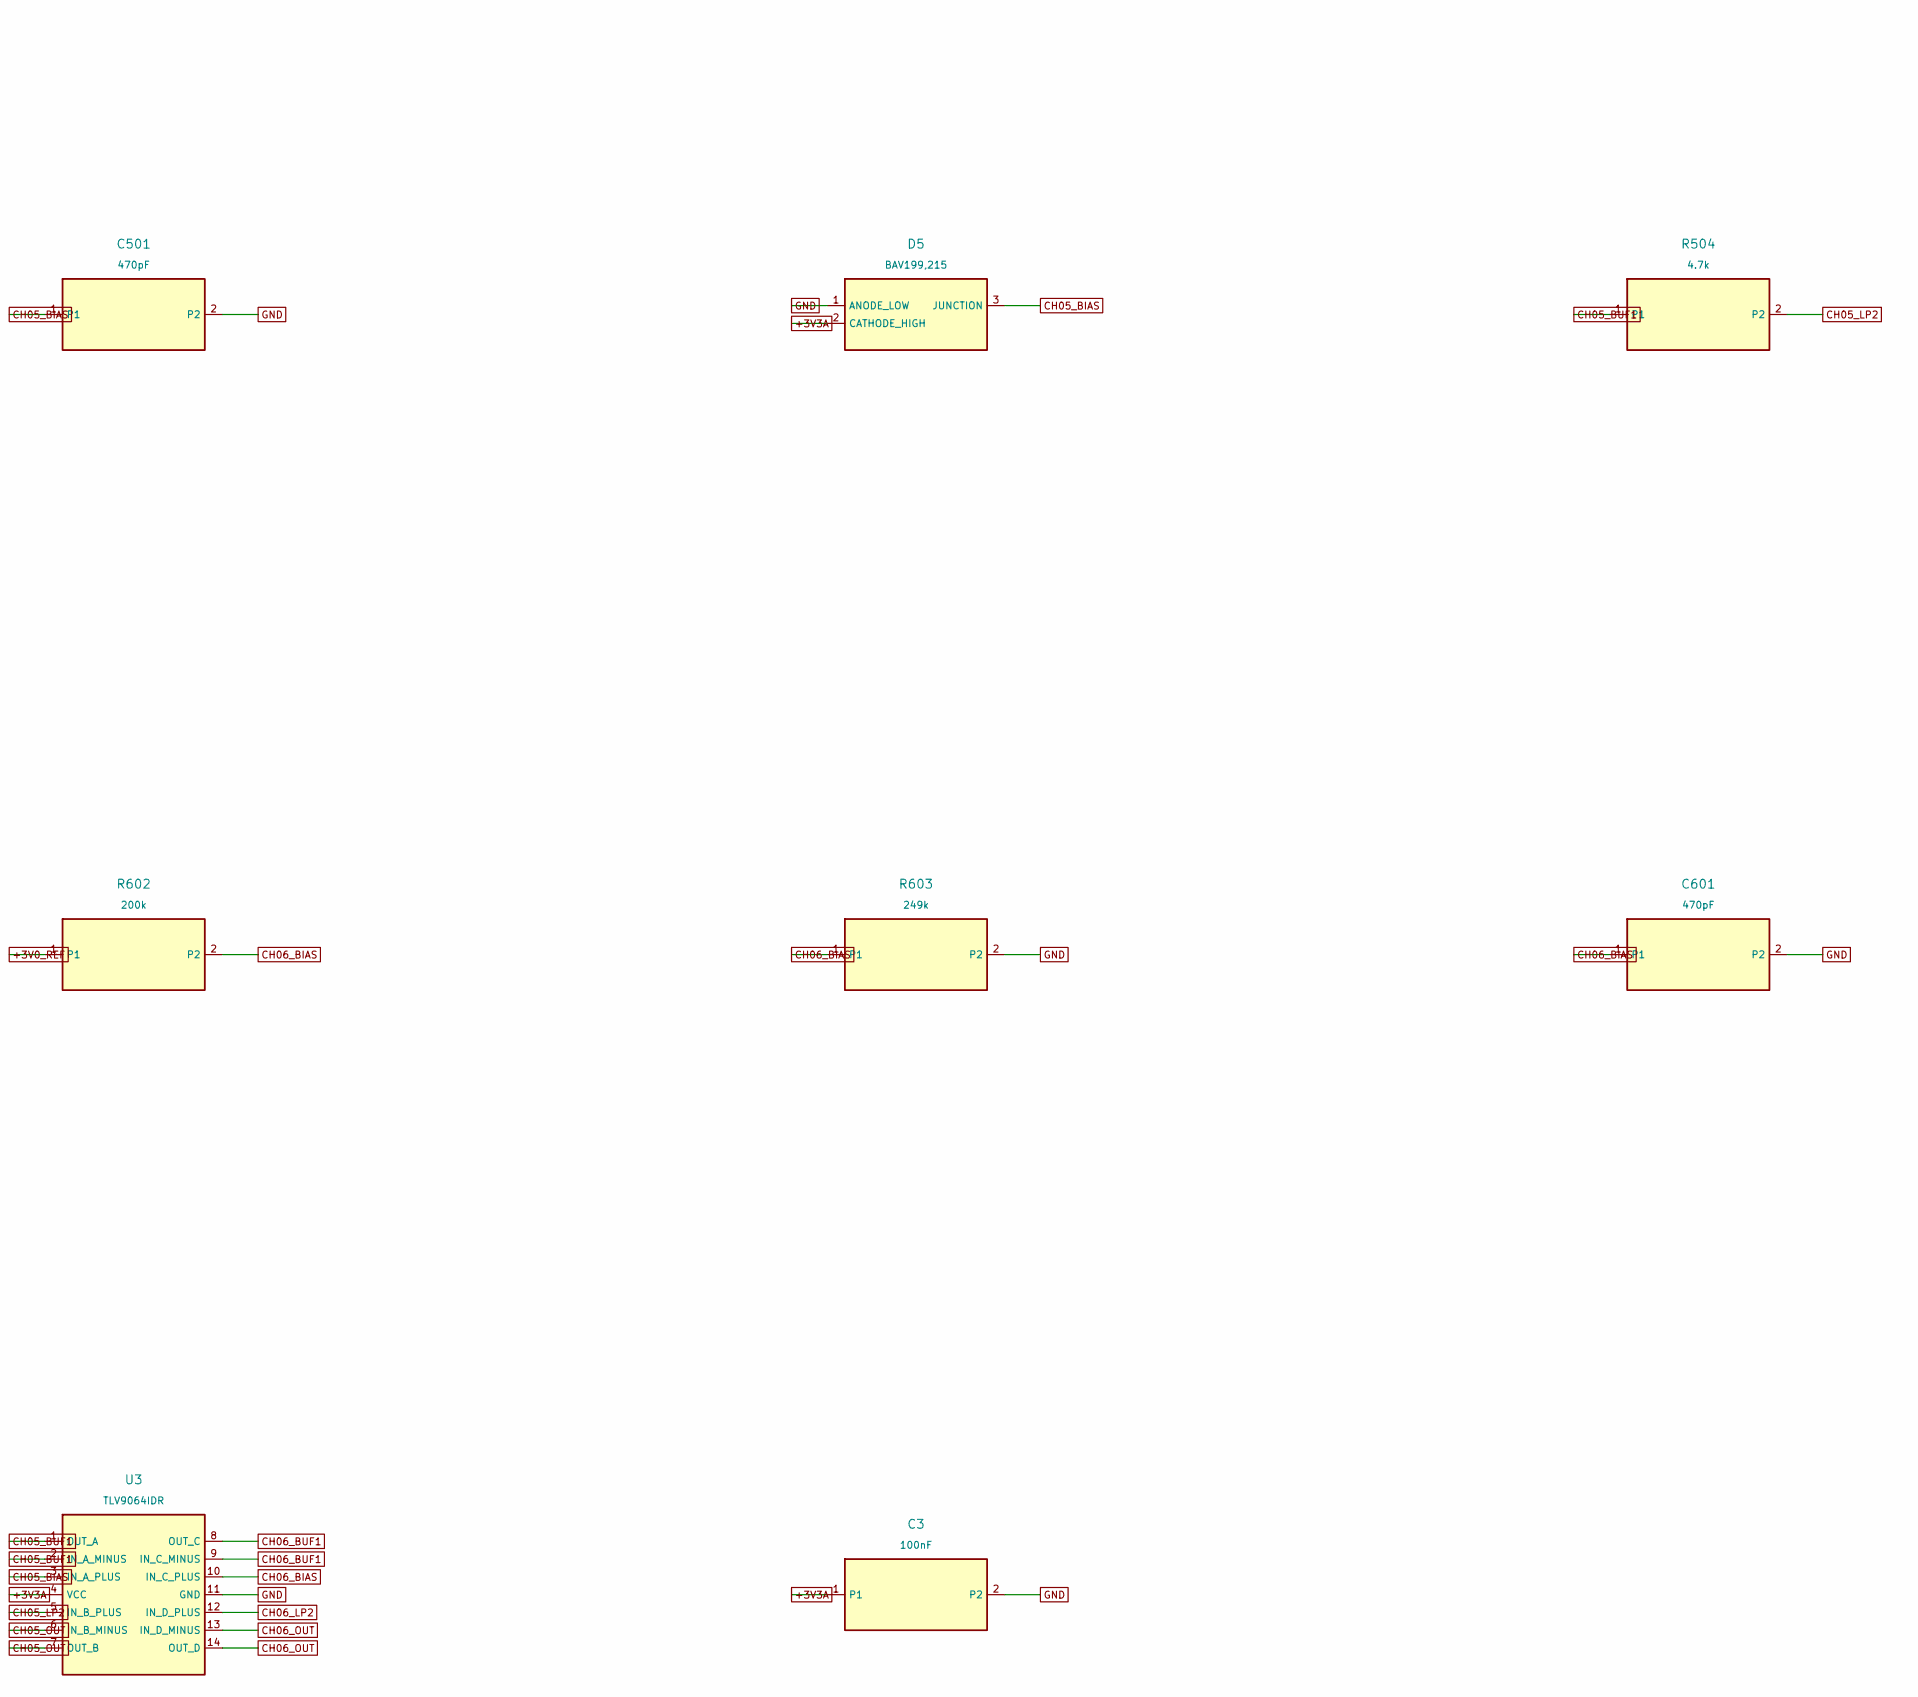
[picture p25: schematic inputs-05-06.kicad_sch, part in row 1, column 3]

Parts:
C3: 100nF; C_0603_1608Metric
C501, C601: 470pF; C_0603_1608Metric
C502, C602: 10nF; C_0603_1608Metric
D5, D6: BAV199,215; SOT-23
J5, J6: PJ-313 5JCJ
R501, R601: 1M; R_0603_1608Metric
R502, R602: 200k; R_0603_1608Metric
R503, R603: 249k; R_0603_1608Metric
R504, R604: 4.7k; R_0603_1608Metric
TP5, TP6: testpoint; TestPoint_Pad_D1.0mm
U3: TLV9064IDR; SOIC-14_3.9x8.7mm_P1.27mm

Connections:
+3V0_REF: R502.1, R602.1
+3V3A: C3.1, D5.2 (CATHODE_HIGH), D6.2 (CATHODE_HIGH), U3.4 (VCC)
CH05_BIAS: C501.1, D5.3 (JUNCTION), R501.2, R502.2, R503.1, U3.3 (IN_A_PLUS)
CH05_BUF1: R504.1, U3.1 (OUT_A), U3.2 (IN_A_MINUS)
CH05_IN: J5.3 (TIP), R501.1
CH05_LP2: C502.1, R504.2, U3.5 (IN_B_PLUS)
CH05_OUT: TP5.1, U3.6 (IN_B_MINUS), U3.7 (OUT_B)
CH06_BIAS: C601.1, D6.3 (JUNCTION), R601.2, R602.2, R603.1, U3.10 (IN_C_PLUS)
CH06_BUF1: R604.1, U3.8 (OUT_C), U3.9 (IN_C_MINUS)
CH06_IN: J6.3 (TIP), R601.1
CH06_LP2: C602.1, R604.2, U3.12 (IN_D_PLUS)
CH06_OUT: TP6.1, U3.13 (IN_D_MINUS), U3.14 (OUT_D)
GND: C3.2, C501.2, C502.2, C601.2, C602.2, D5.1 (ANODE_LOW), D6.1 (ANODE_LOW), J5.1 (SLEEVE), J6.1 (SLEEVE), R503.2, R603.2, U3.11 (GND)

Notes on the sheet:
NOT FOR FABRICATION - exact footprints and interface gates remain OPEN
