Takazudo/zudo-scope10/hardware/kicad/inputs-07-08.kicad_sch

## KiCad design hardware/kicad/inputs-07-08.kicad_sch (2026-09-26)

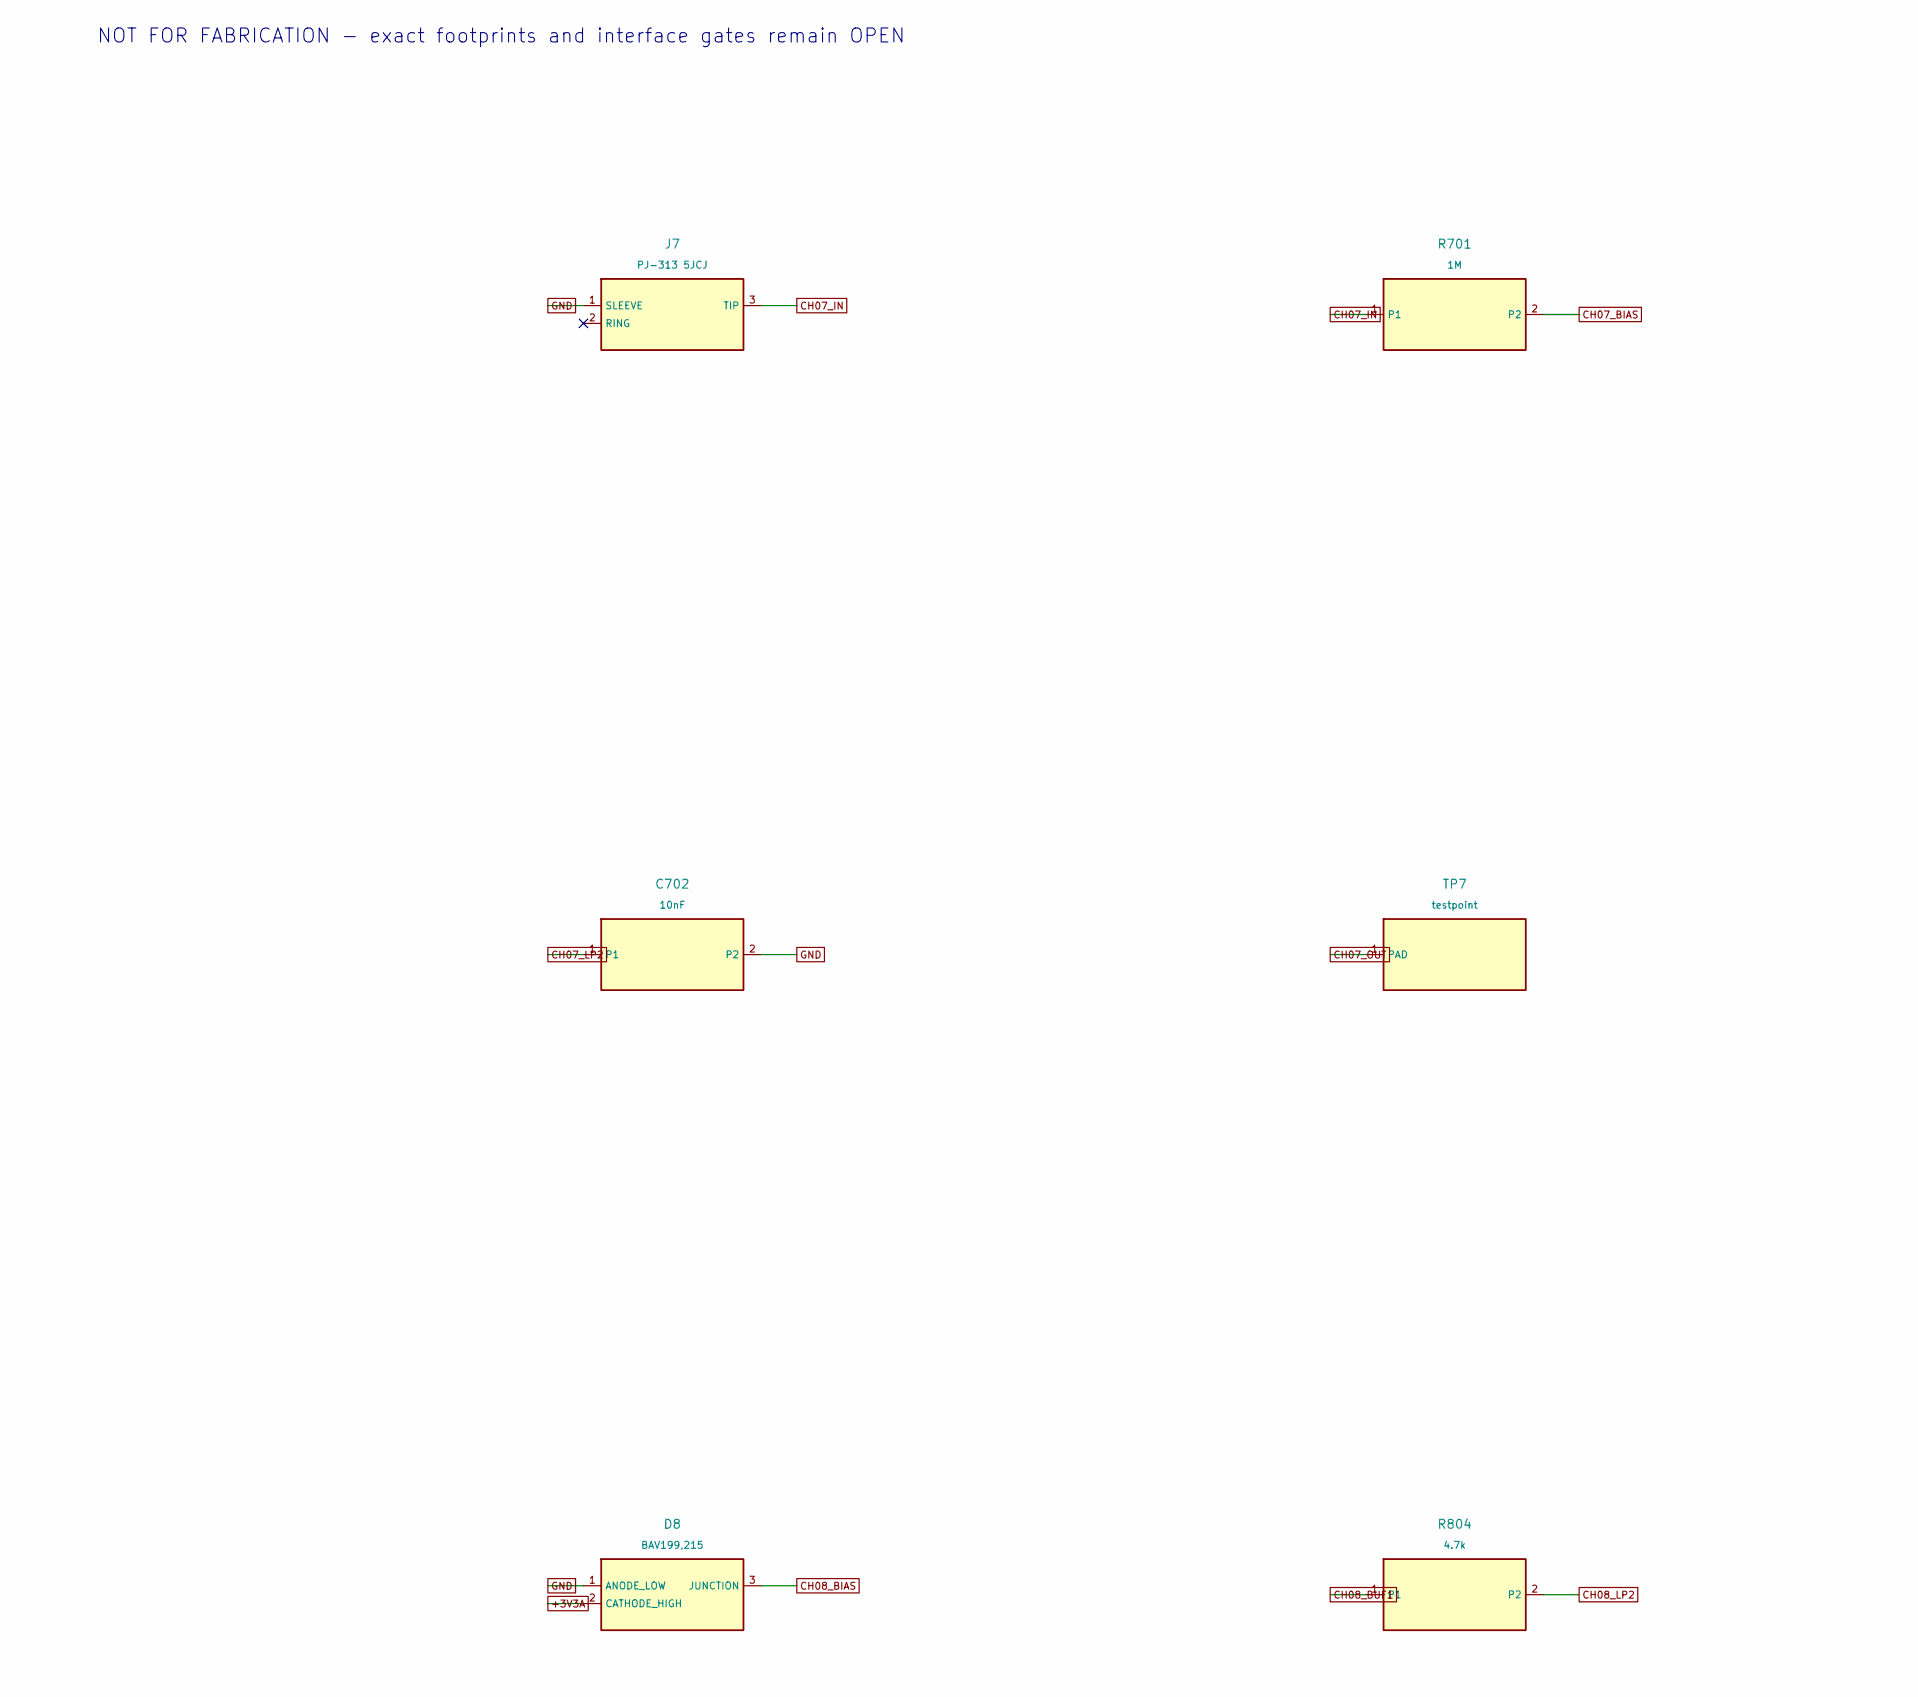
[picture p26: schematic inputs-07-08.kicad_sch, part in row 1, column 1]

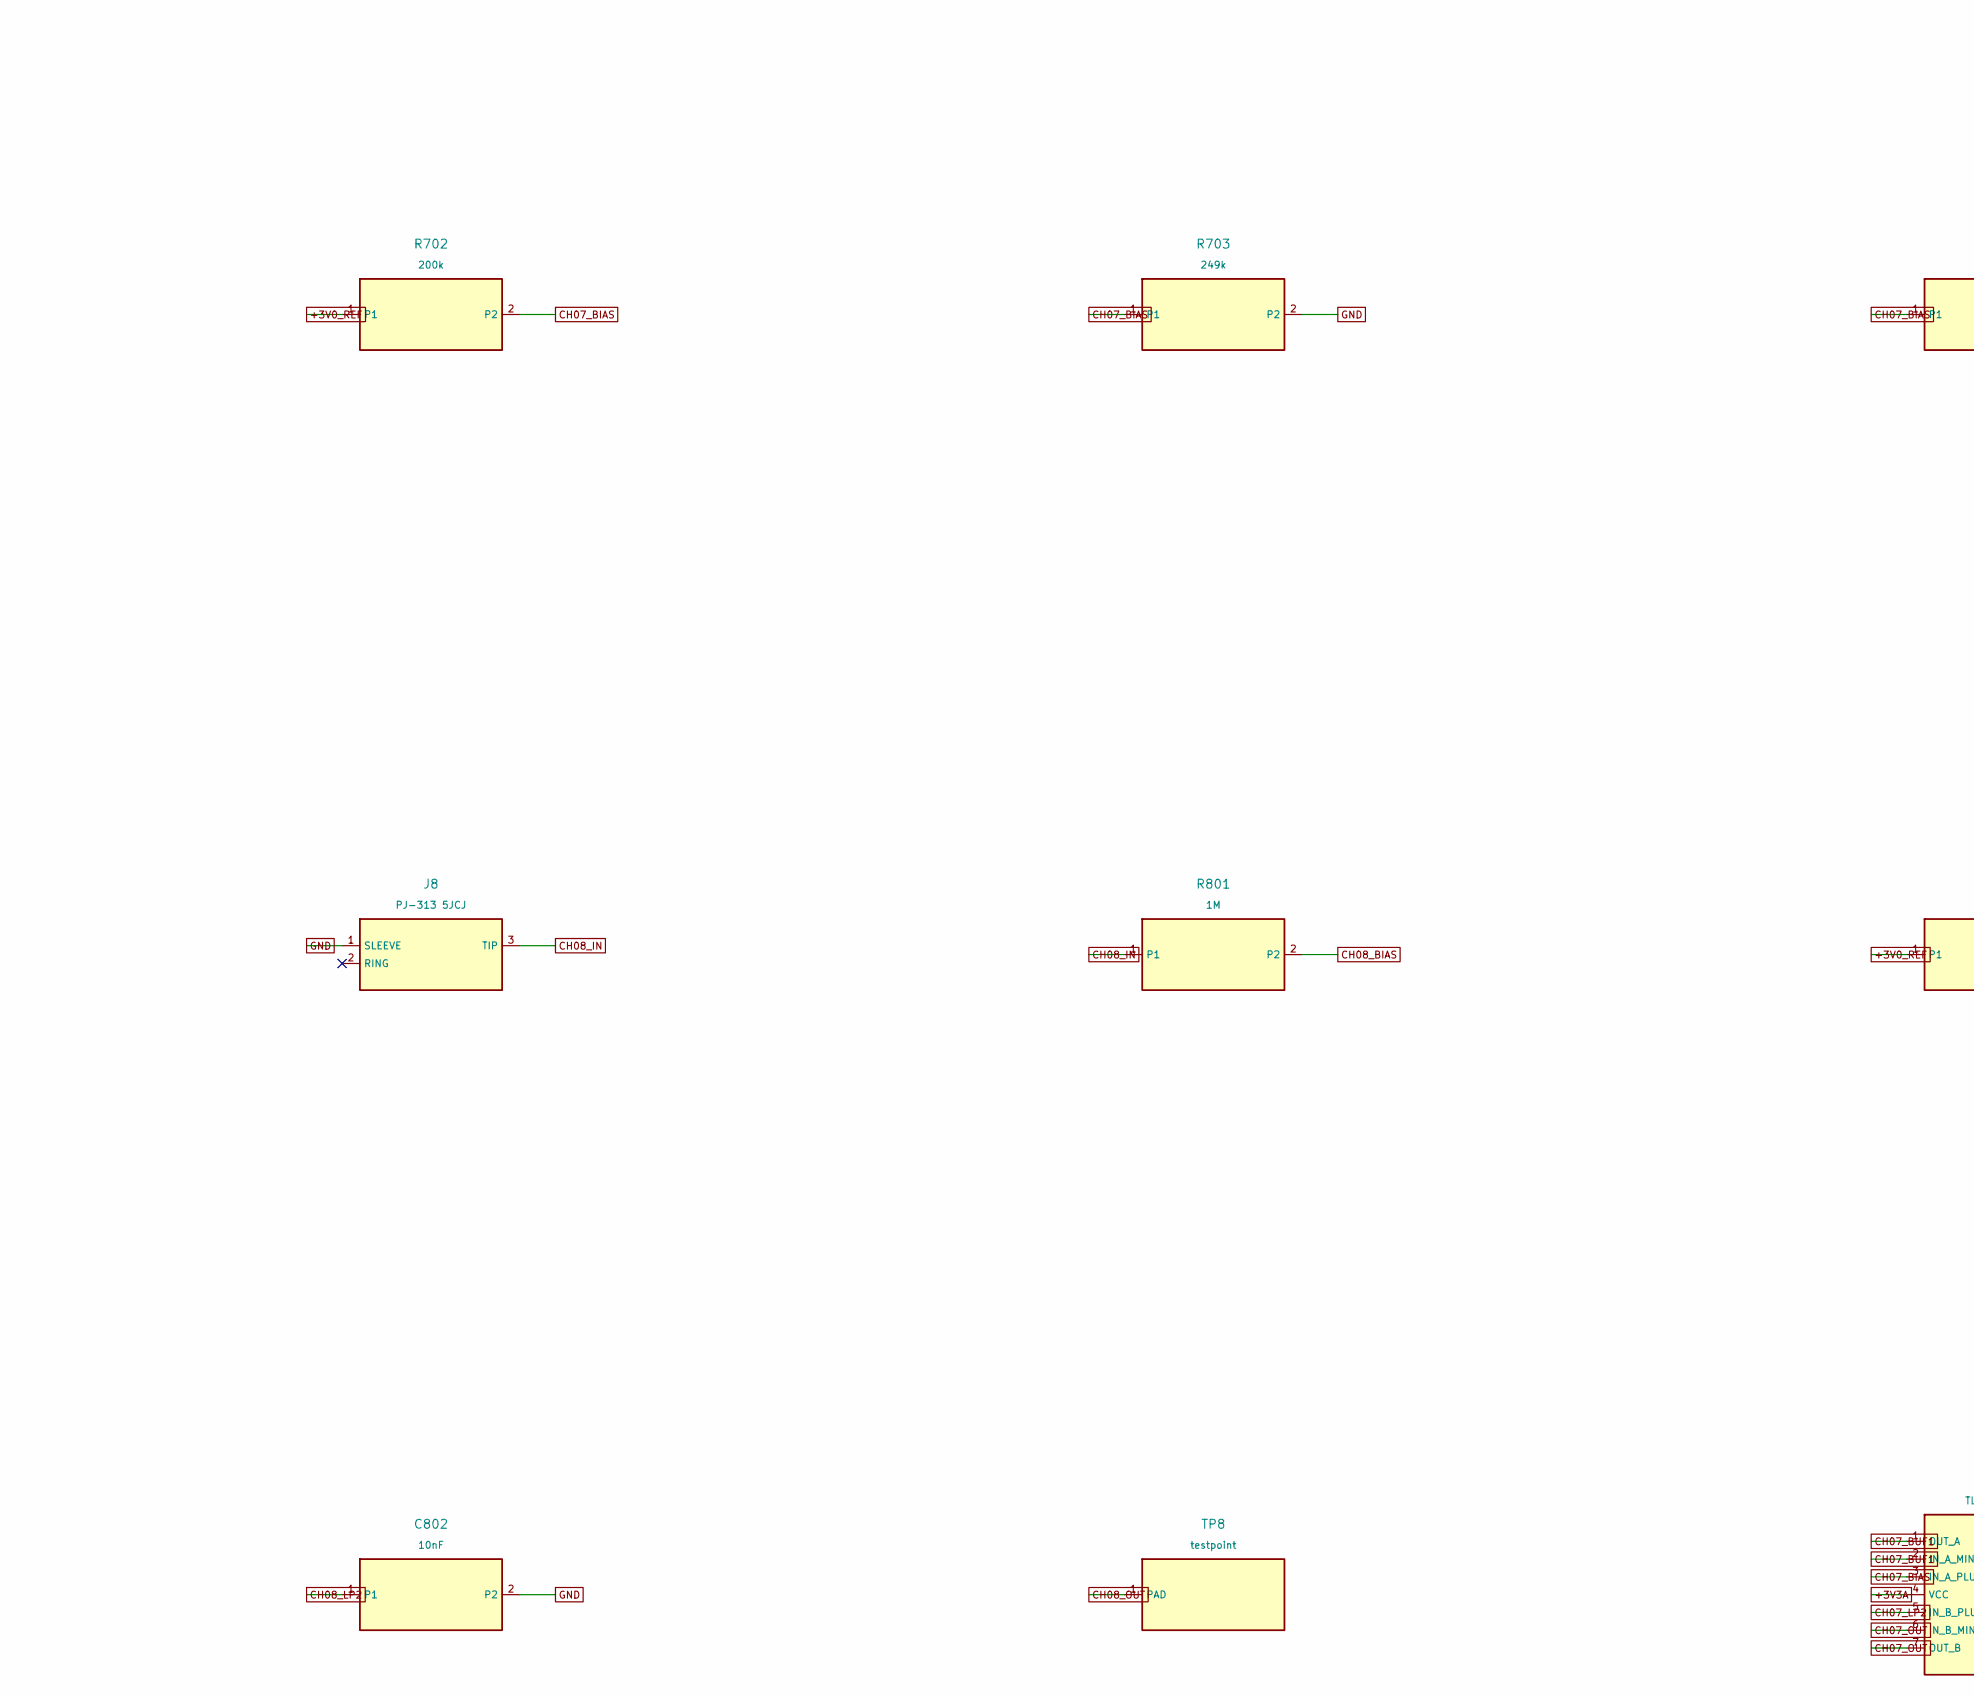
[picture p27: schematic inputs-07-08.kicad_sch, part in row 1, column 2]

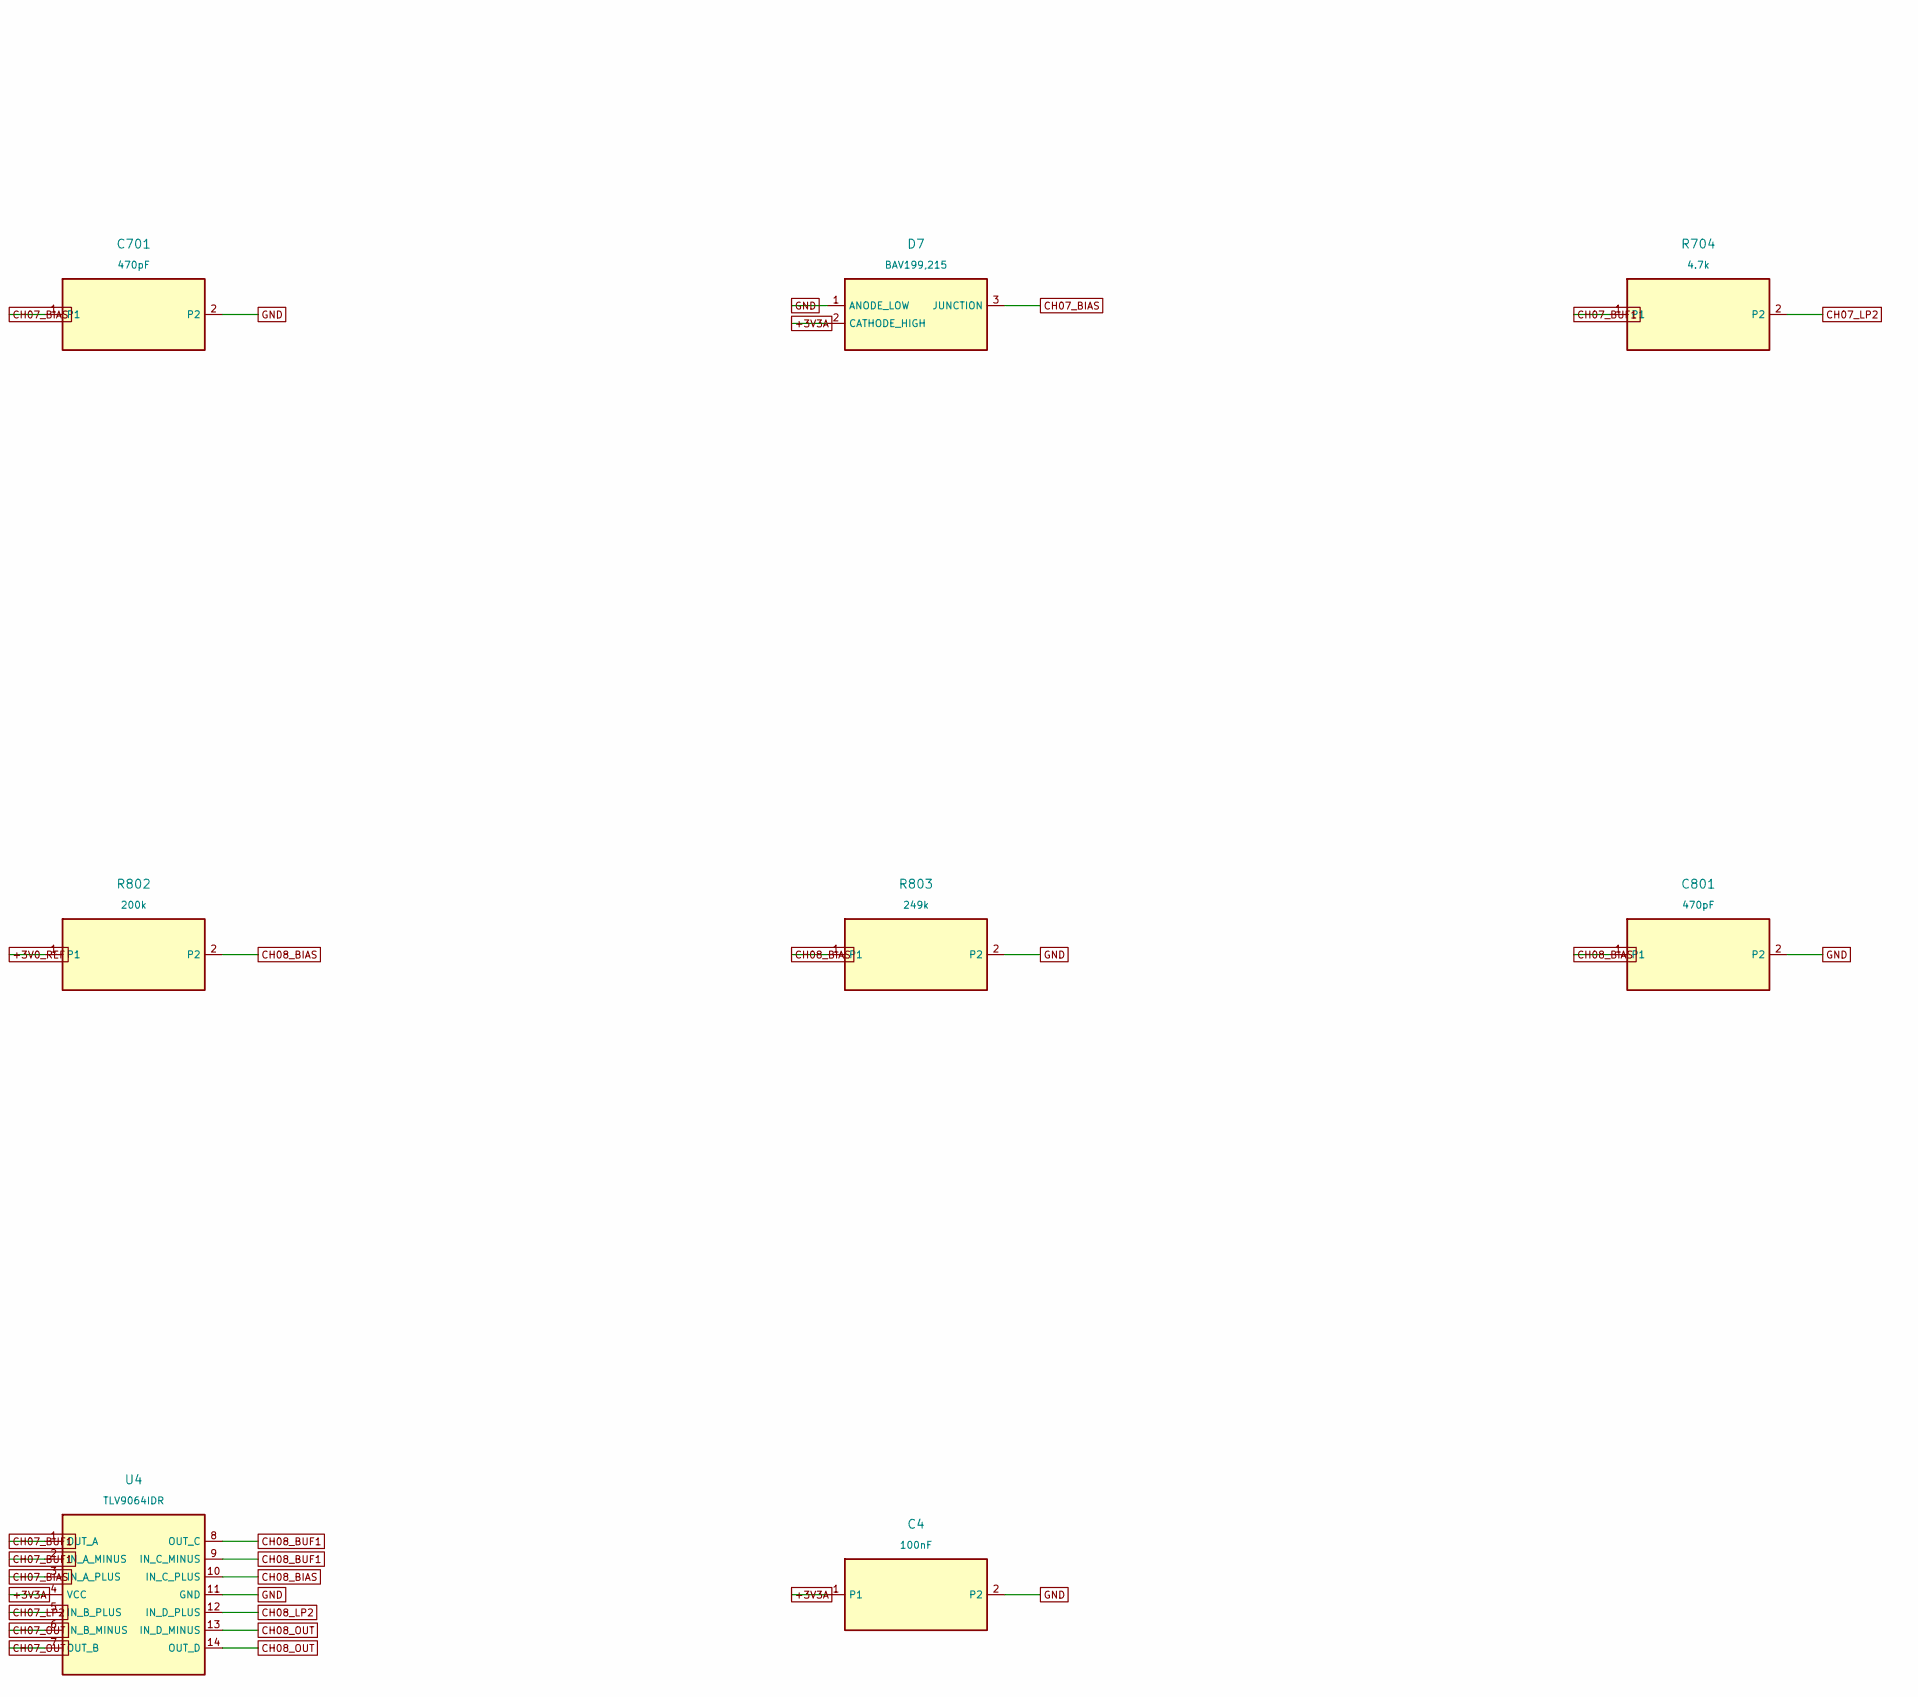
[picture p28: schematic inputs-07-08.kicad_sch, part in row 1, column 3]

Parts:
C4: 100nF; C_0603_1608Metric
C701, C801: 470pF; C_0603_1608Metric
C702, C802: 10nF; C_0603_1608Metric
D7, D8: BAV199,215; SOT-23
J7, J8: PJ-313 5JCJ
R701, R801: 1M; R_0603_1608Metric
R702, R802: 200k; R_0603_1608Metric
R703, R803: 249k; R_0603_1608Metric
R704, R804: 4.7k; R_0603_1608Metric
TP7, TP8: testpoint; TestPoint_Pad_D1.0mm
U4: TLV9064IDR; SOIC-14_3.9x8.7mm_P1.27mm

Connections:
+3V0_REF: R702.1, R802.1
+3V3A: C4.1, D7.2 (CATHODE_HIGH), D8.2 (CATHODE_HIGH), U4.4 (VCC)
CH07_BIAS: C701.1, D7.3 (JUNCTION), R701.2, R702.2, R703.1, U4.3 (IN_A_PLUS)
CH07_BUF1: R704.1, U4.1 (OUT_A), U4.2 (IN_A_MINUS)
CH07_IN: J7.3 (TIP), R701.1
CH07_LP2: C702.1, R704.2, U4.5 (IN_B_PLUS)
CH07_OUT: TP7.1, U4.6 (IN_B_MINUS), U4.7 (OUT_B)
CH08_BIAS: C801.1, D8.3 (JUNCTION), R801.2, R802.2, R803.1, U4.10 (IN_C_PLUS)
CH08_BUF1: R804.1, U4.8 (OUT_C), U4.9 (IN_C_MINUS)
CH08_IN: J8.3 (TIP), R801.1
CH08_LP2: C802.1, R804.2, U4.12 (IN_D_PLUS)
CH08_OUT: TP8.1, U4.13 (IN_D_MINUS), U4.14 (OUT_D)
GND: C4.2, C701.2, C702.2, C801.2, C802.2, D7.1 (ANODE_LOW), D8.1 (ANODE_LOW), J7.1 (SLEEVE), J8.1 (SLEEVE), R703.2, R803.2, U4.11 (GND)

Notes on the sheet:
NOT FOR FABRICATION - exact footprints and interface gates remain OPEN
