Takazudo/zudo-scope10/hardware/kicad/inputs-09-10.kicad_sch

## KiCad design hardware/kicad/inputs-09-10.kicad_sch (2026-09-26)

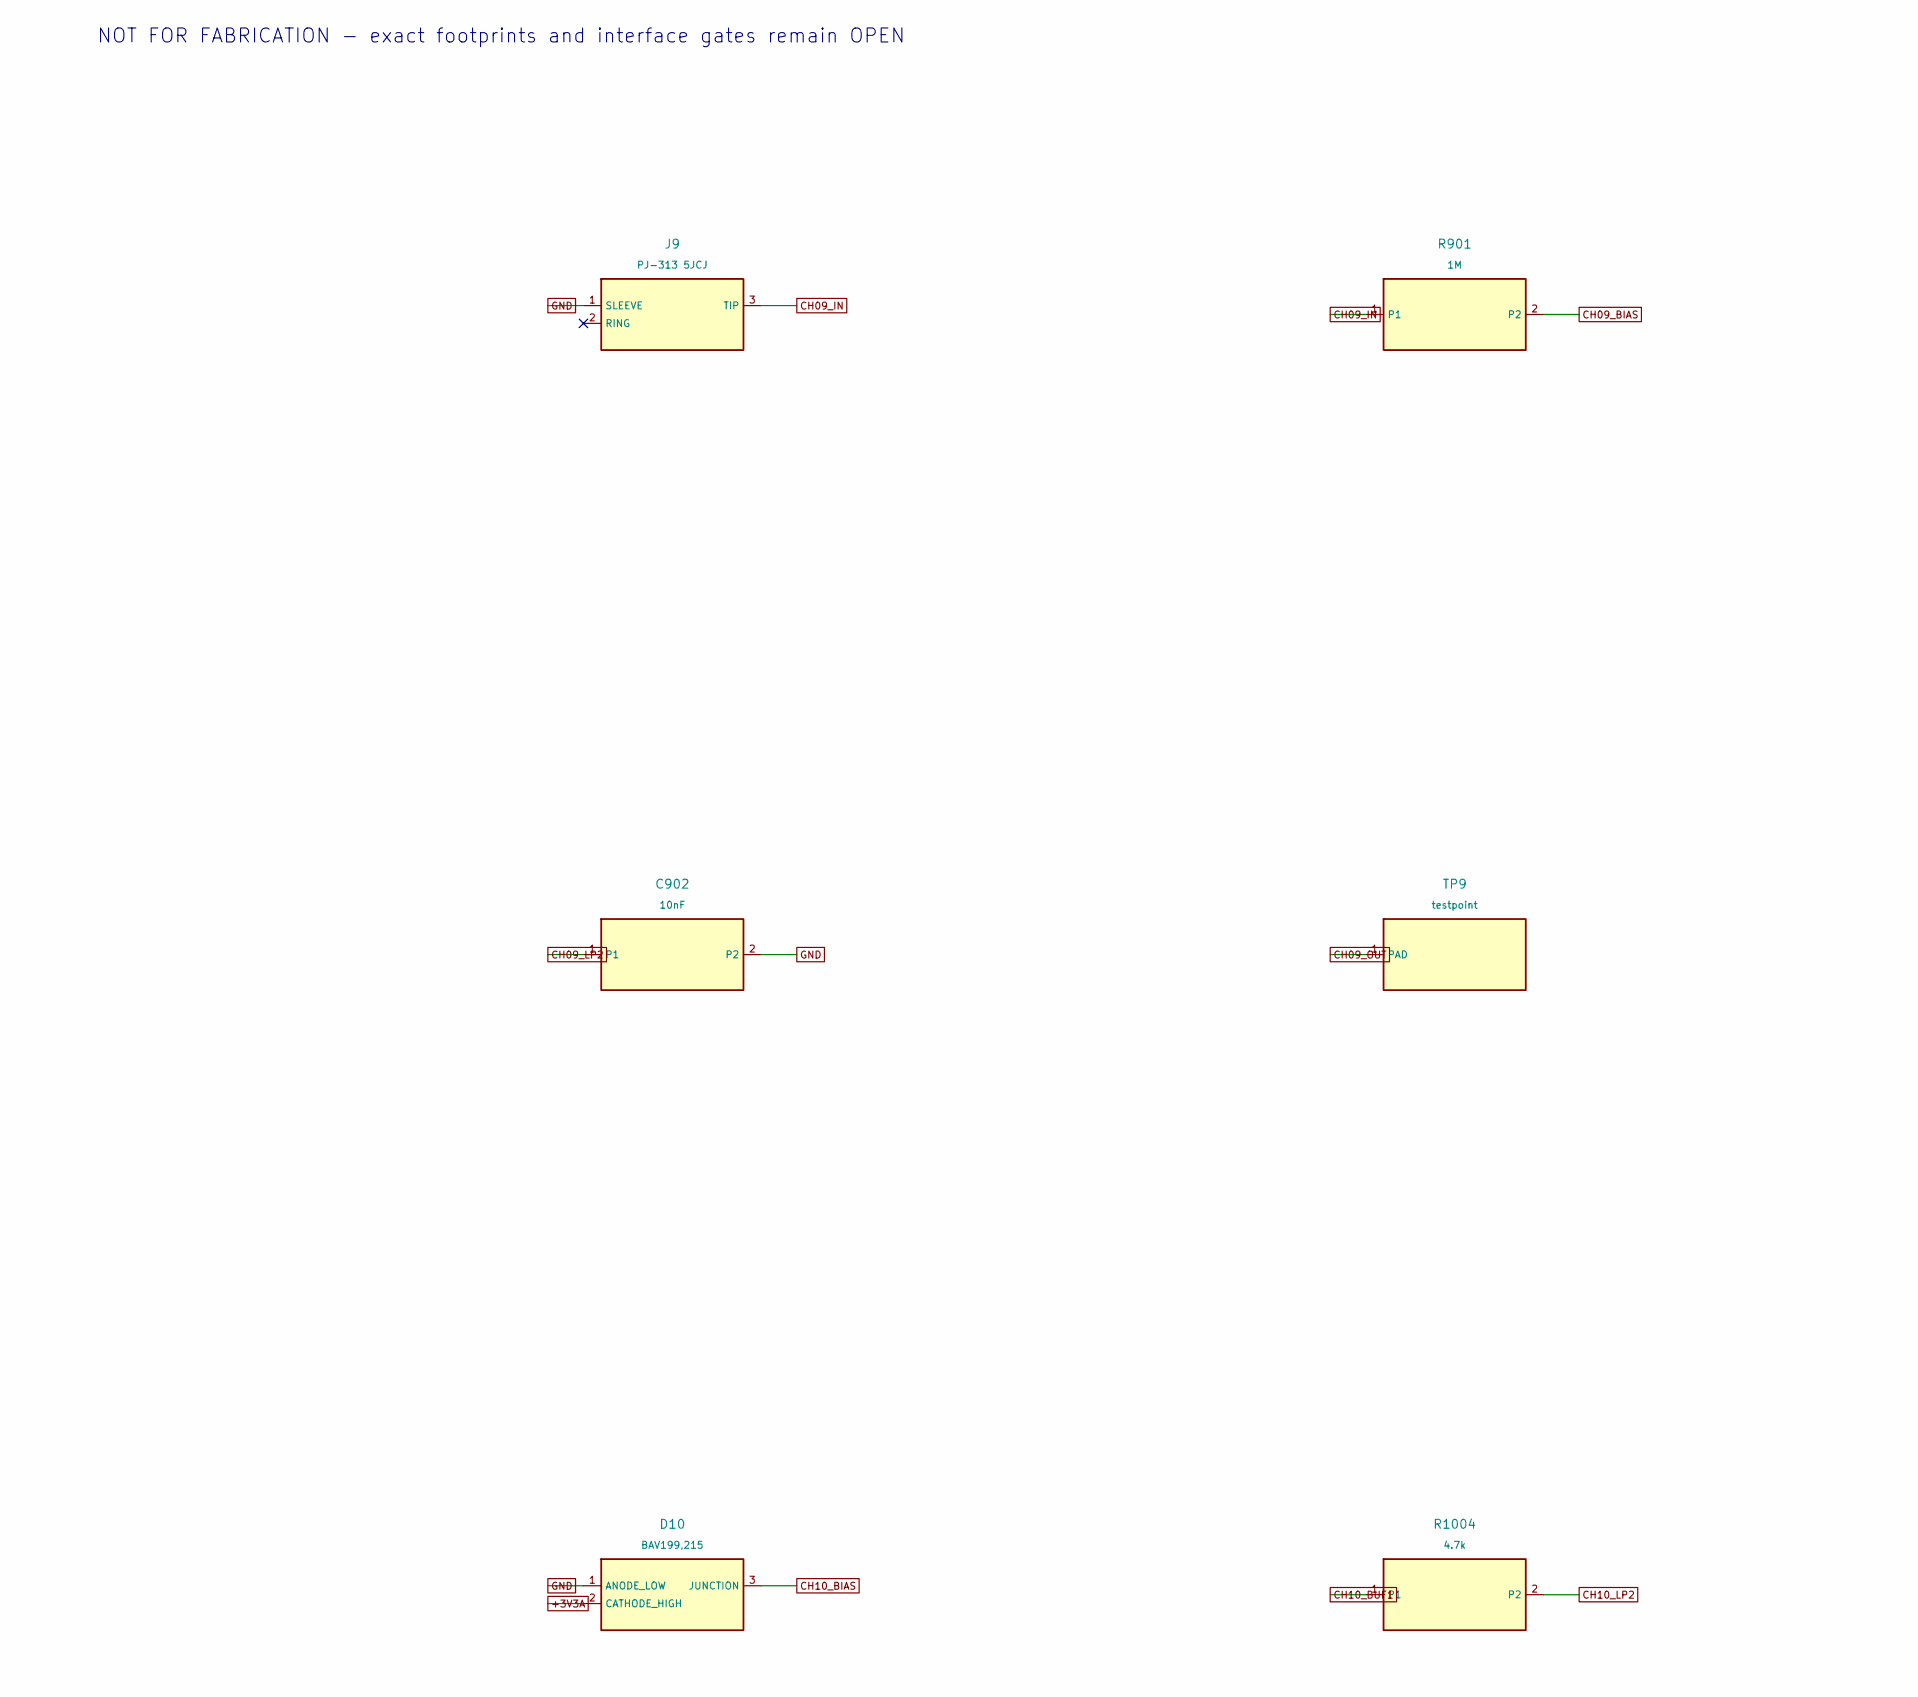
[picture p29: schematic inputs-09-10.kicad_sch, part in row 1, column 1]

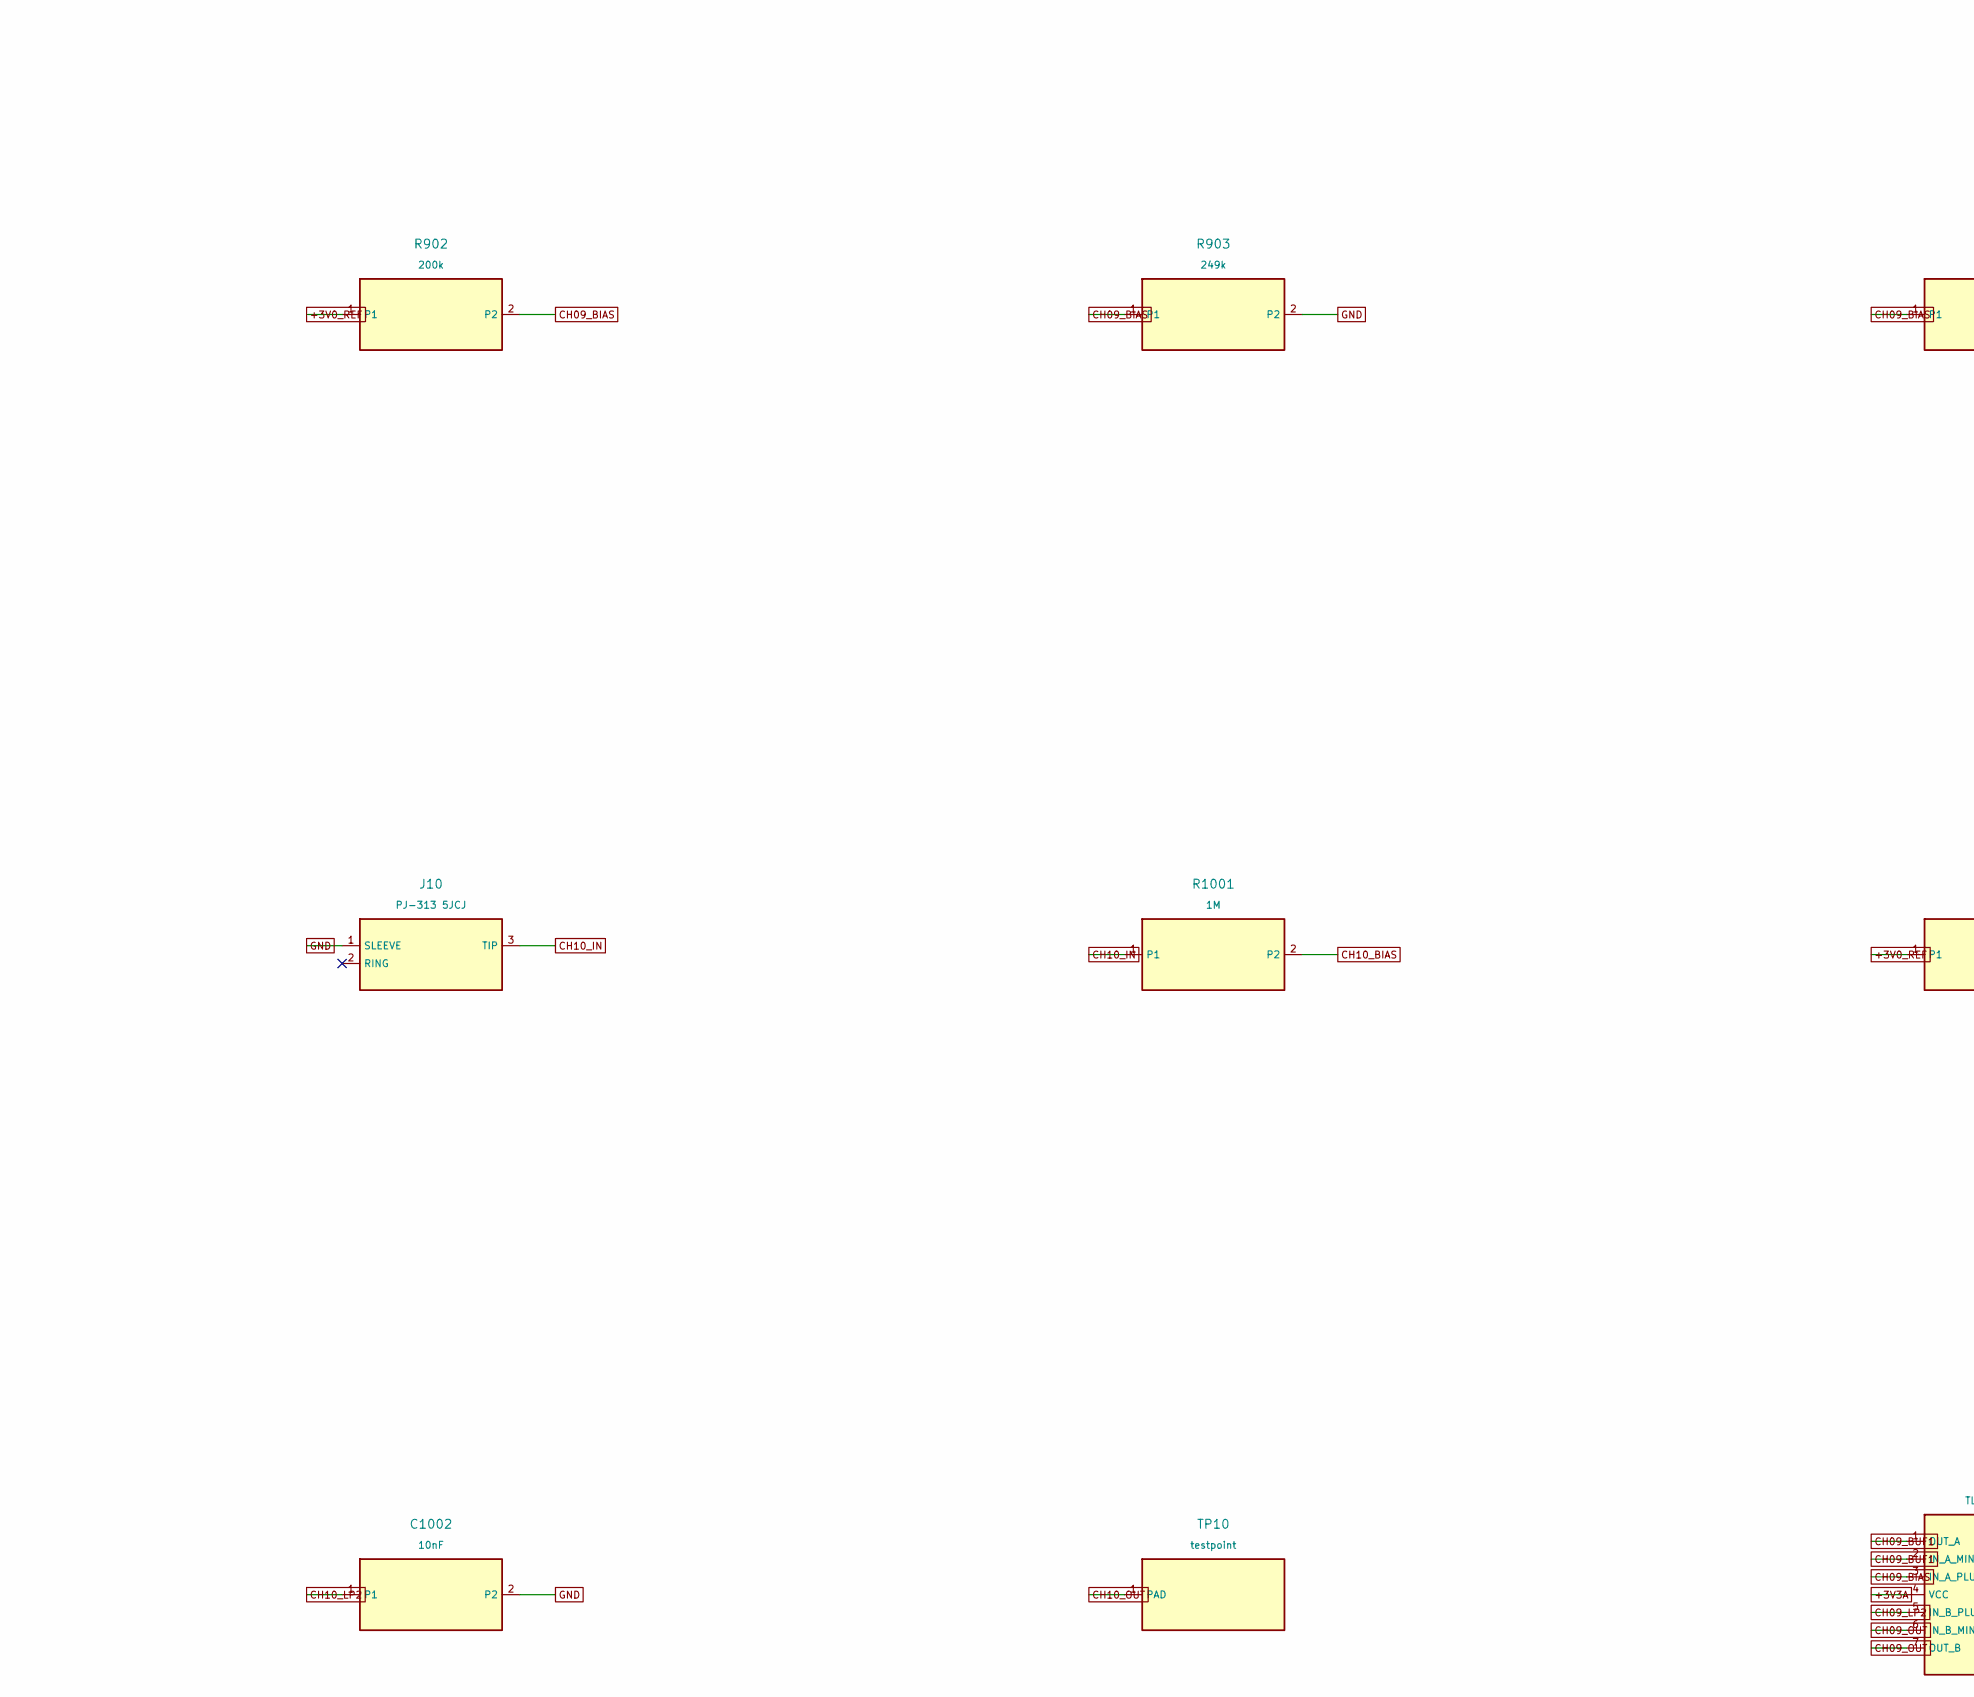
[picture p30: schematic inputs-09-10.kicad_sch, part in row 1, column 2]

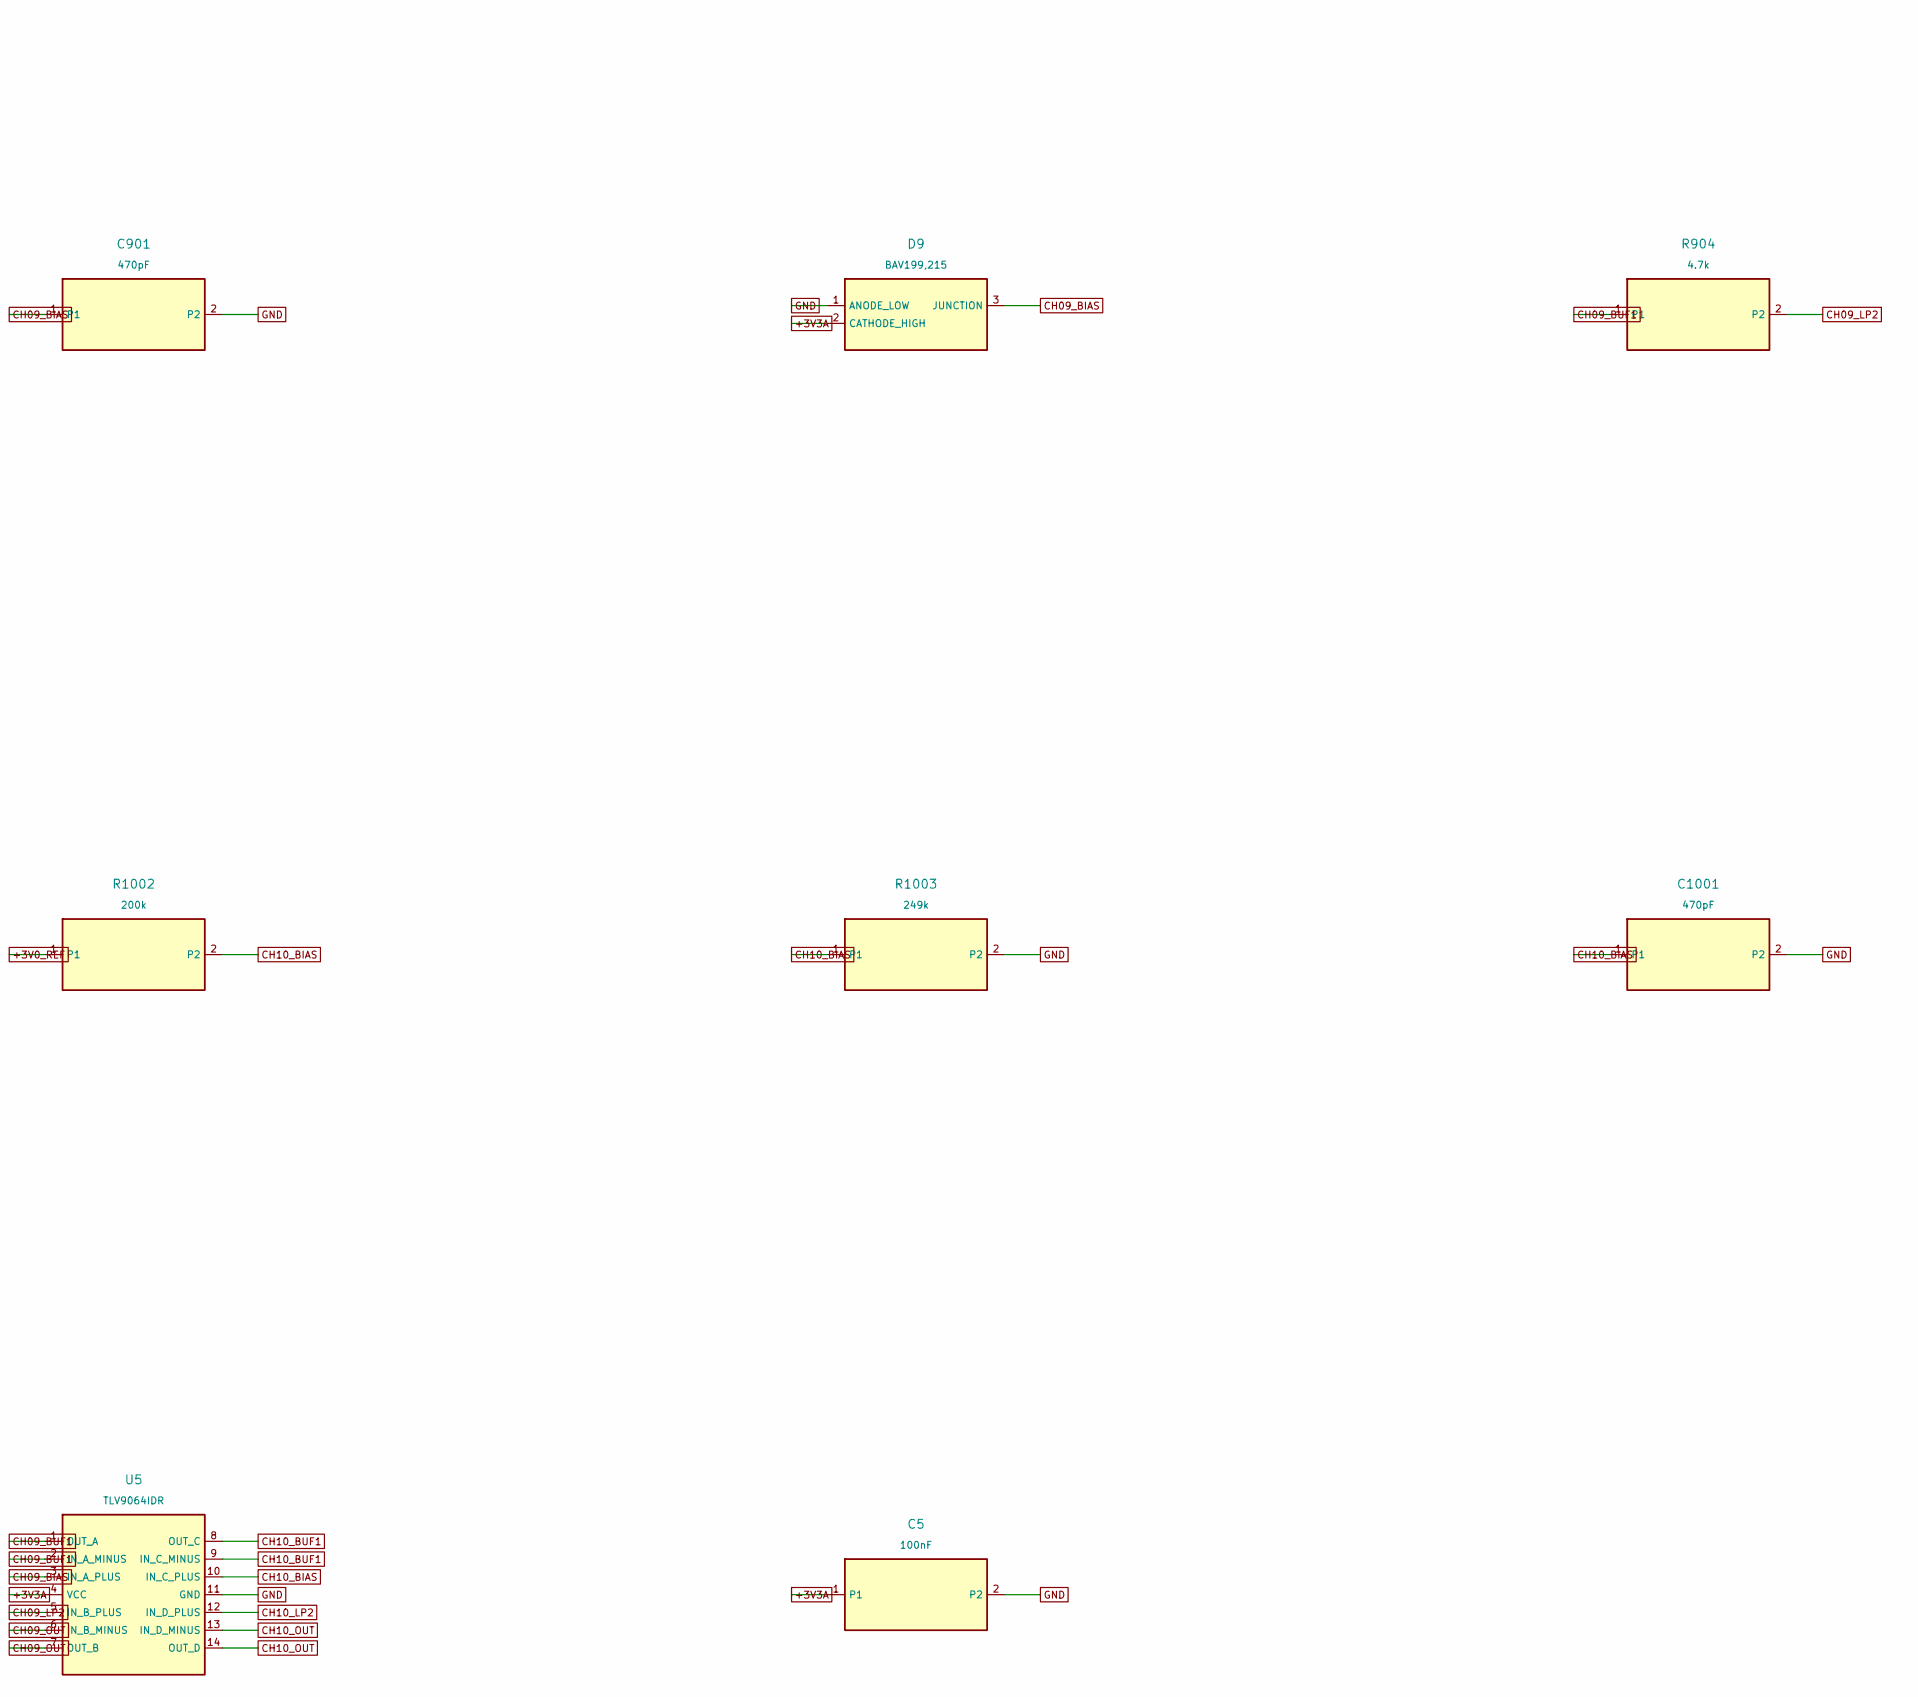
[picture p31: schematic inputs-09-10.kicad_sch, part in row 1, column 3]

Parts:
C5: 100nF; C_0603_1608Metric
C901, C1001: 470pF; C_0603_1608Metric
C902, C1002: 10nF; C_0603_1608Metric
D9, D10: BAV199,215; SOT-23
J9, J10: PJ-313 5JCJ
R901, R1001: 1M; R_0603_1608Metric
R902, R1002: 200k; R_0603_1608Metric
R903, R1003: 249k; R_0603_1608Metric
R904, R1004: 4.7k; R_0603_1608Metric
TP9, TP10: testpoint; TestPoint_Pad_D1.0mm
U5: TLV9064IDR; SOIC-14_3.9x8.7mm_P1.27mm

Connections:
+3V0_REF: R902.1, R1002.1
+3V3A: C5.1, D9.2 (CATHODE_HIGH), D10.2 (CATHODE_HIGH), U5.4 (VCC)
CH09_BIAS: C901.1, D9.3 (JUNCTION), R901.2, R902.2, R903.1, U5.3 (IN_A_PLUS)
CH09_BUF1: R904.1, U5.1 (OUT_A), U5.2 (IN_A_MINUS)
CH09_IN: J9.3 (TIP), R901.1
CH09_LP2: C902.1, R904.2, U5.5 (IN_B_PLUS)
CH09_OUT: TP9.1, U5.6 (IN_B_MINUS), U5.7 (OUT_B)
CH10_BIAS: C1001.1, D10.3 (JUNCTION), R1001.2, R1002.2, R1003.1, U5.10 (IN_C_PLUS)
CH10_BUF1: R1004.1, U5.8 (OUT_C), U5.9 (IN_C_MINUS)
CH10_IN: J10.3 (TIP), R1001.1
CH10_LP2: C1002.1, R1004.2, U5.12 (IN_D_PLUS)
CH10_OUT: TP10.1, U5.13 (IN_D_MINUS), U5.14 (OUT_D)
GND: C5.2, C901.2, C902.2, C1001.2, C1002.2, D9.1 (ANODE_LOW), D10.1 (ANODE_LOW), J9.1 (SLEEVE), J10.1 (SLEEVE), R903.2, R1003.2, U5.11 (GND)

Notes on the sheet:
NOT FOR FABRICATION - exact footprints and interface gates remain OPEN
