Takazudo/zudo-scope10/hardware/kicad/module-interfaces.kicad_sch

## KiCad design hardware/kicad/module-interfaces.kicad_sch (2026-09-26, an earlier design)

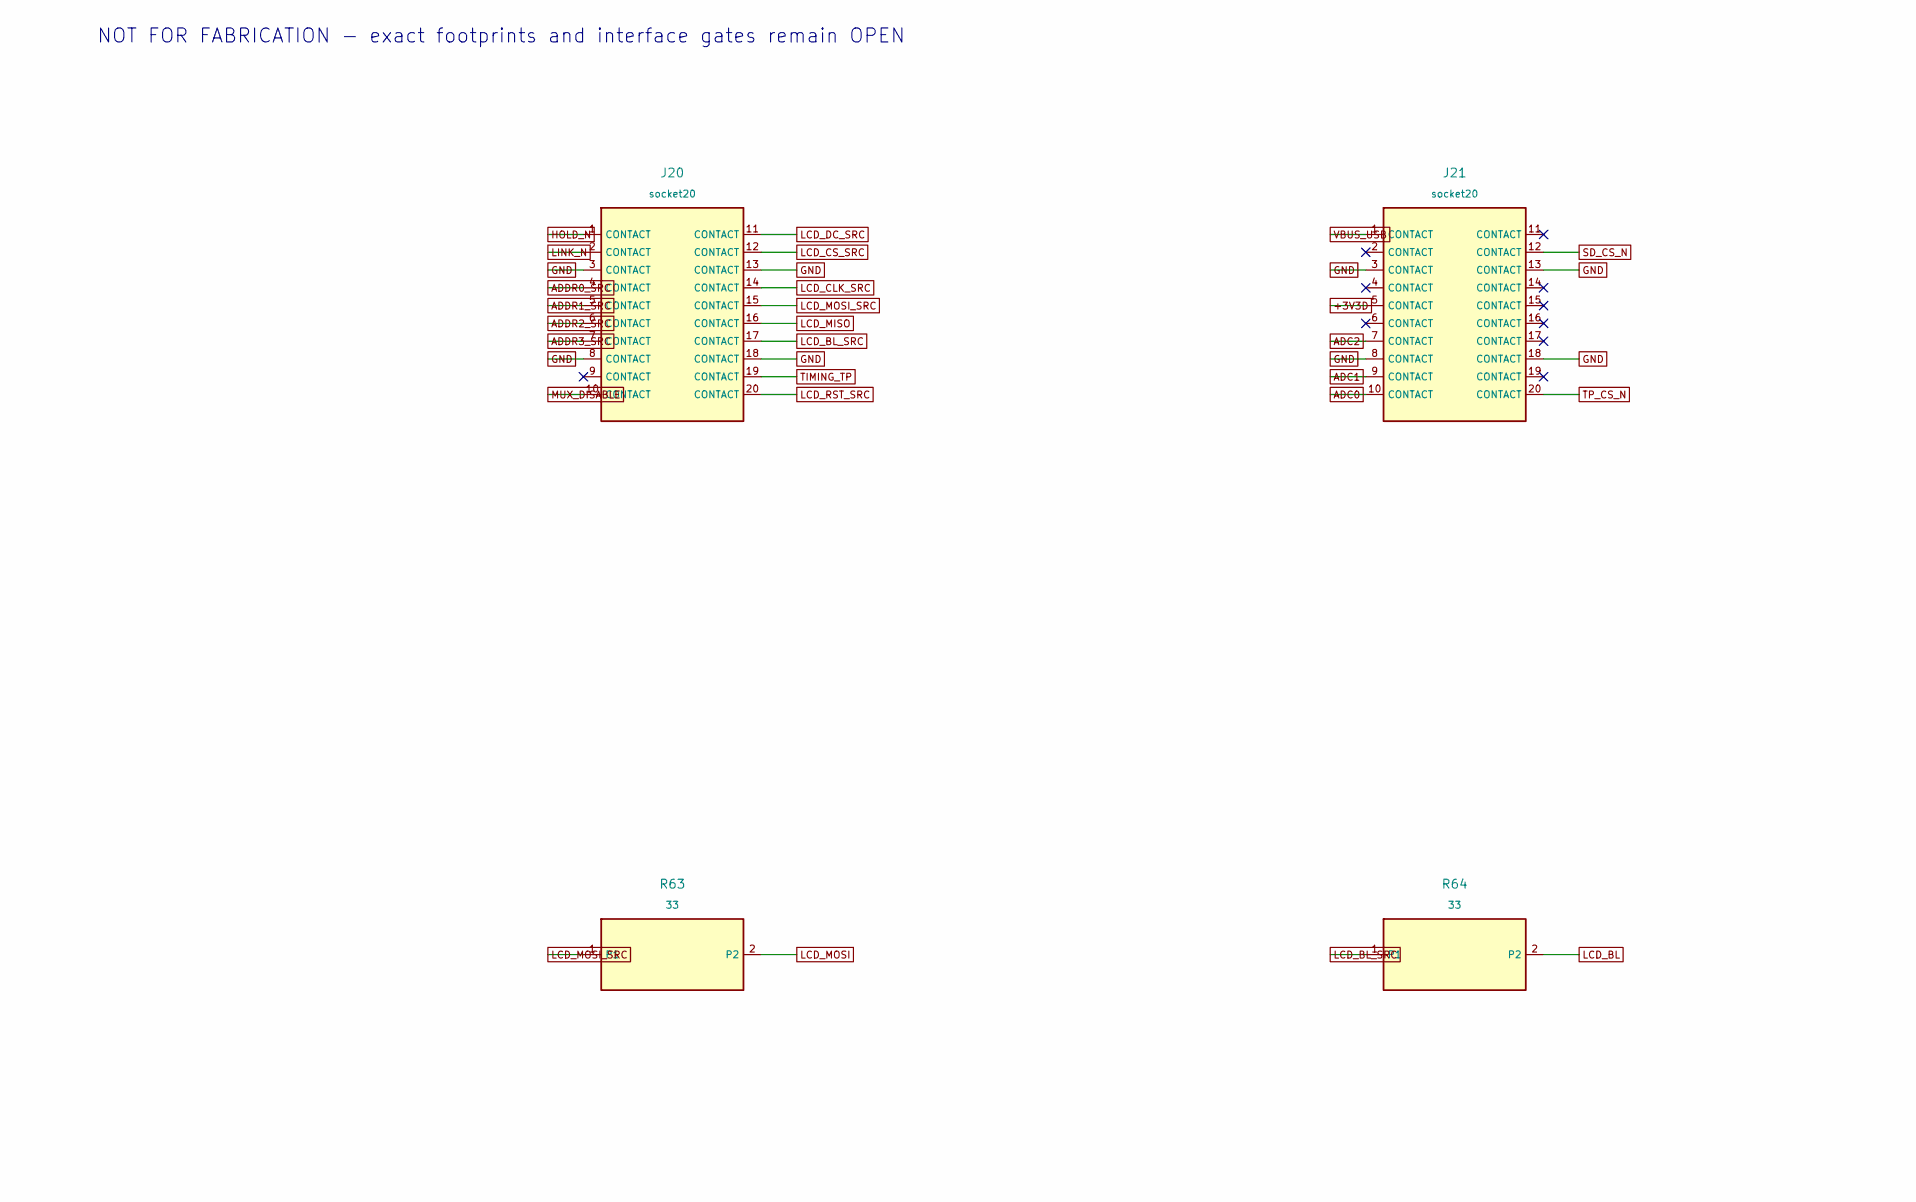
[picture p32: schematic module-interfaces.kicad_sch, part in row 1, column 1]

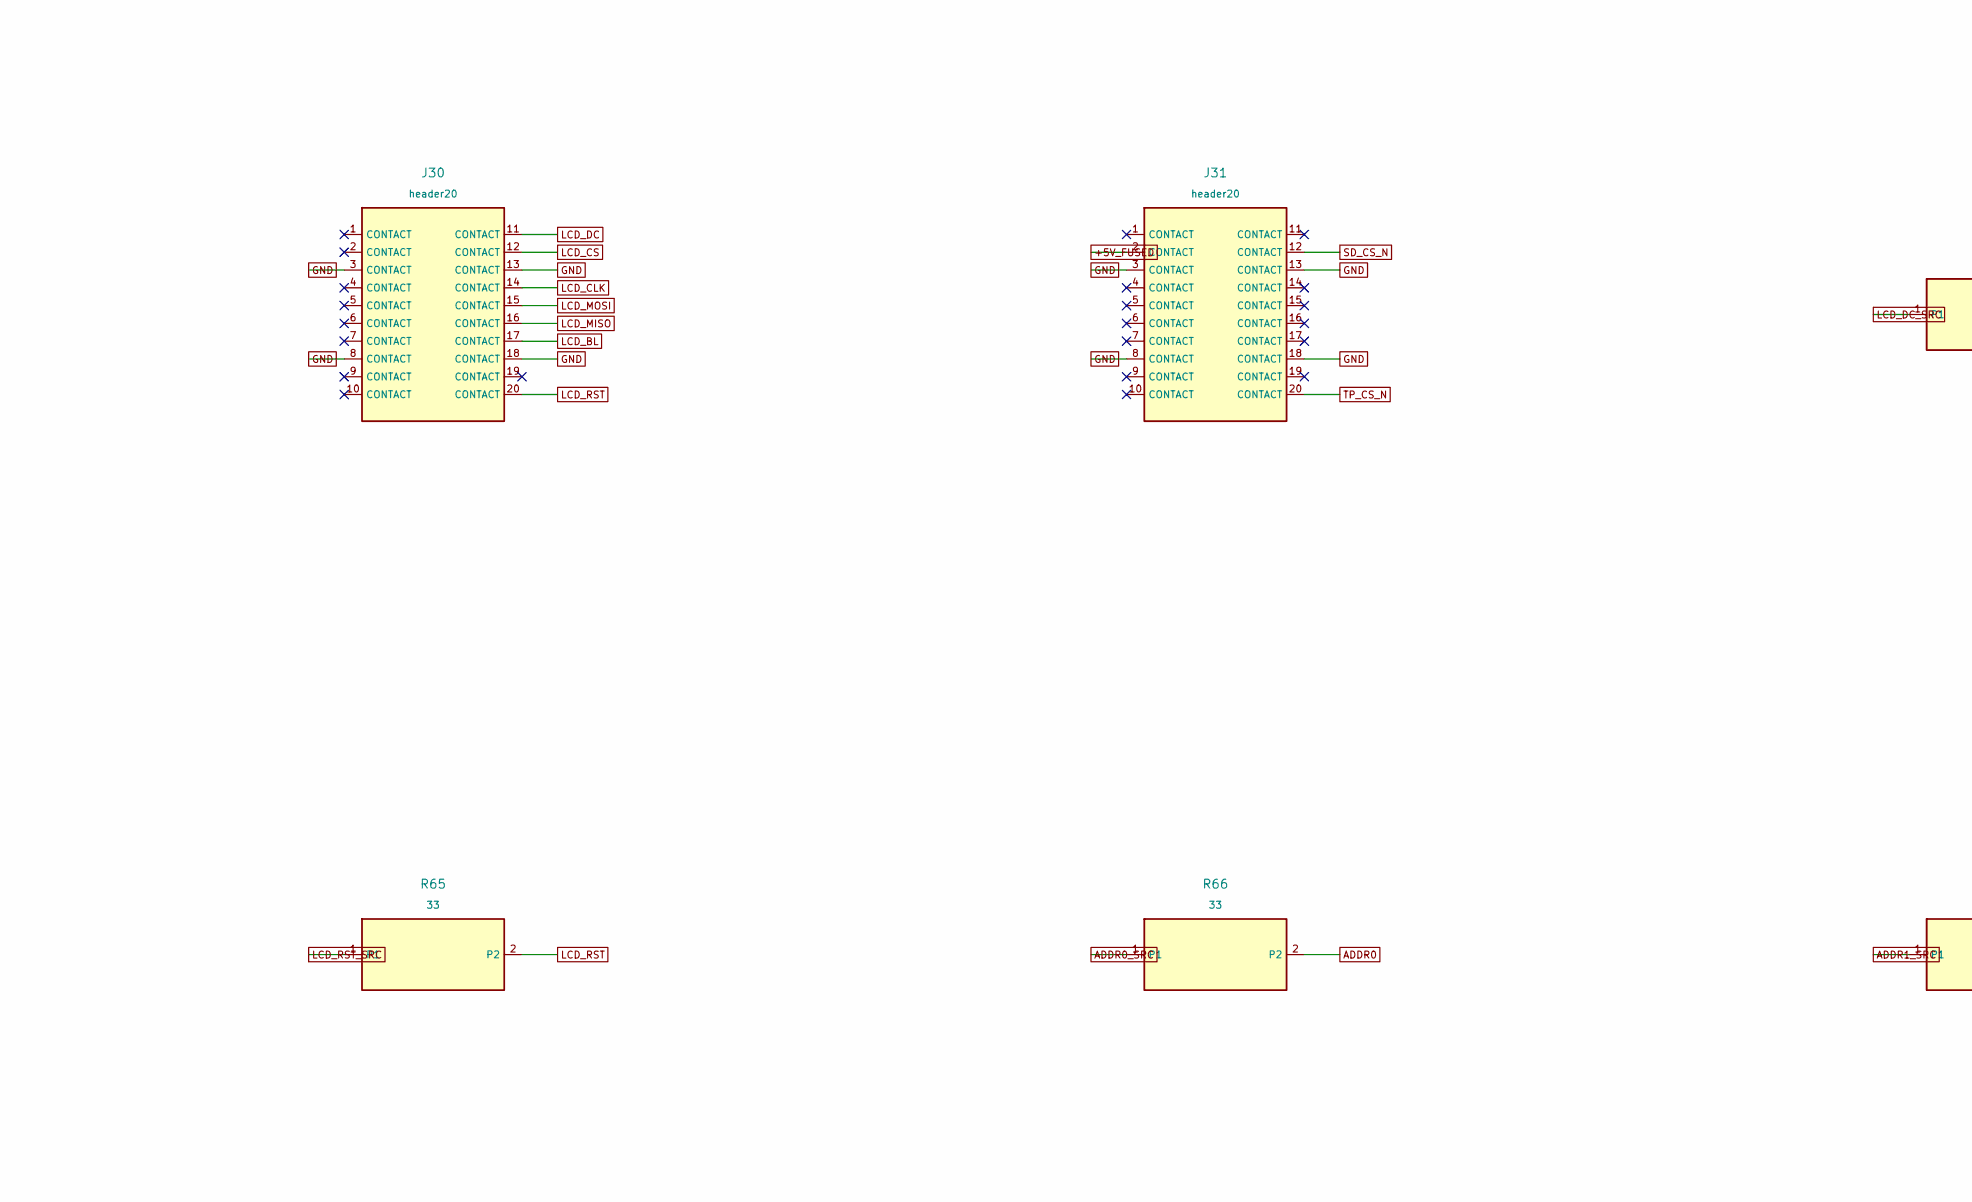
[picture p33: schematic module-interfaces.kicad_sch, part in row 1, column 2]

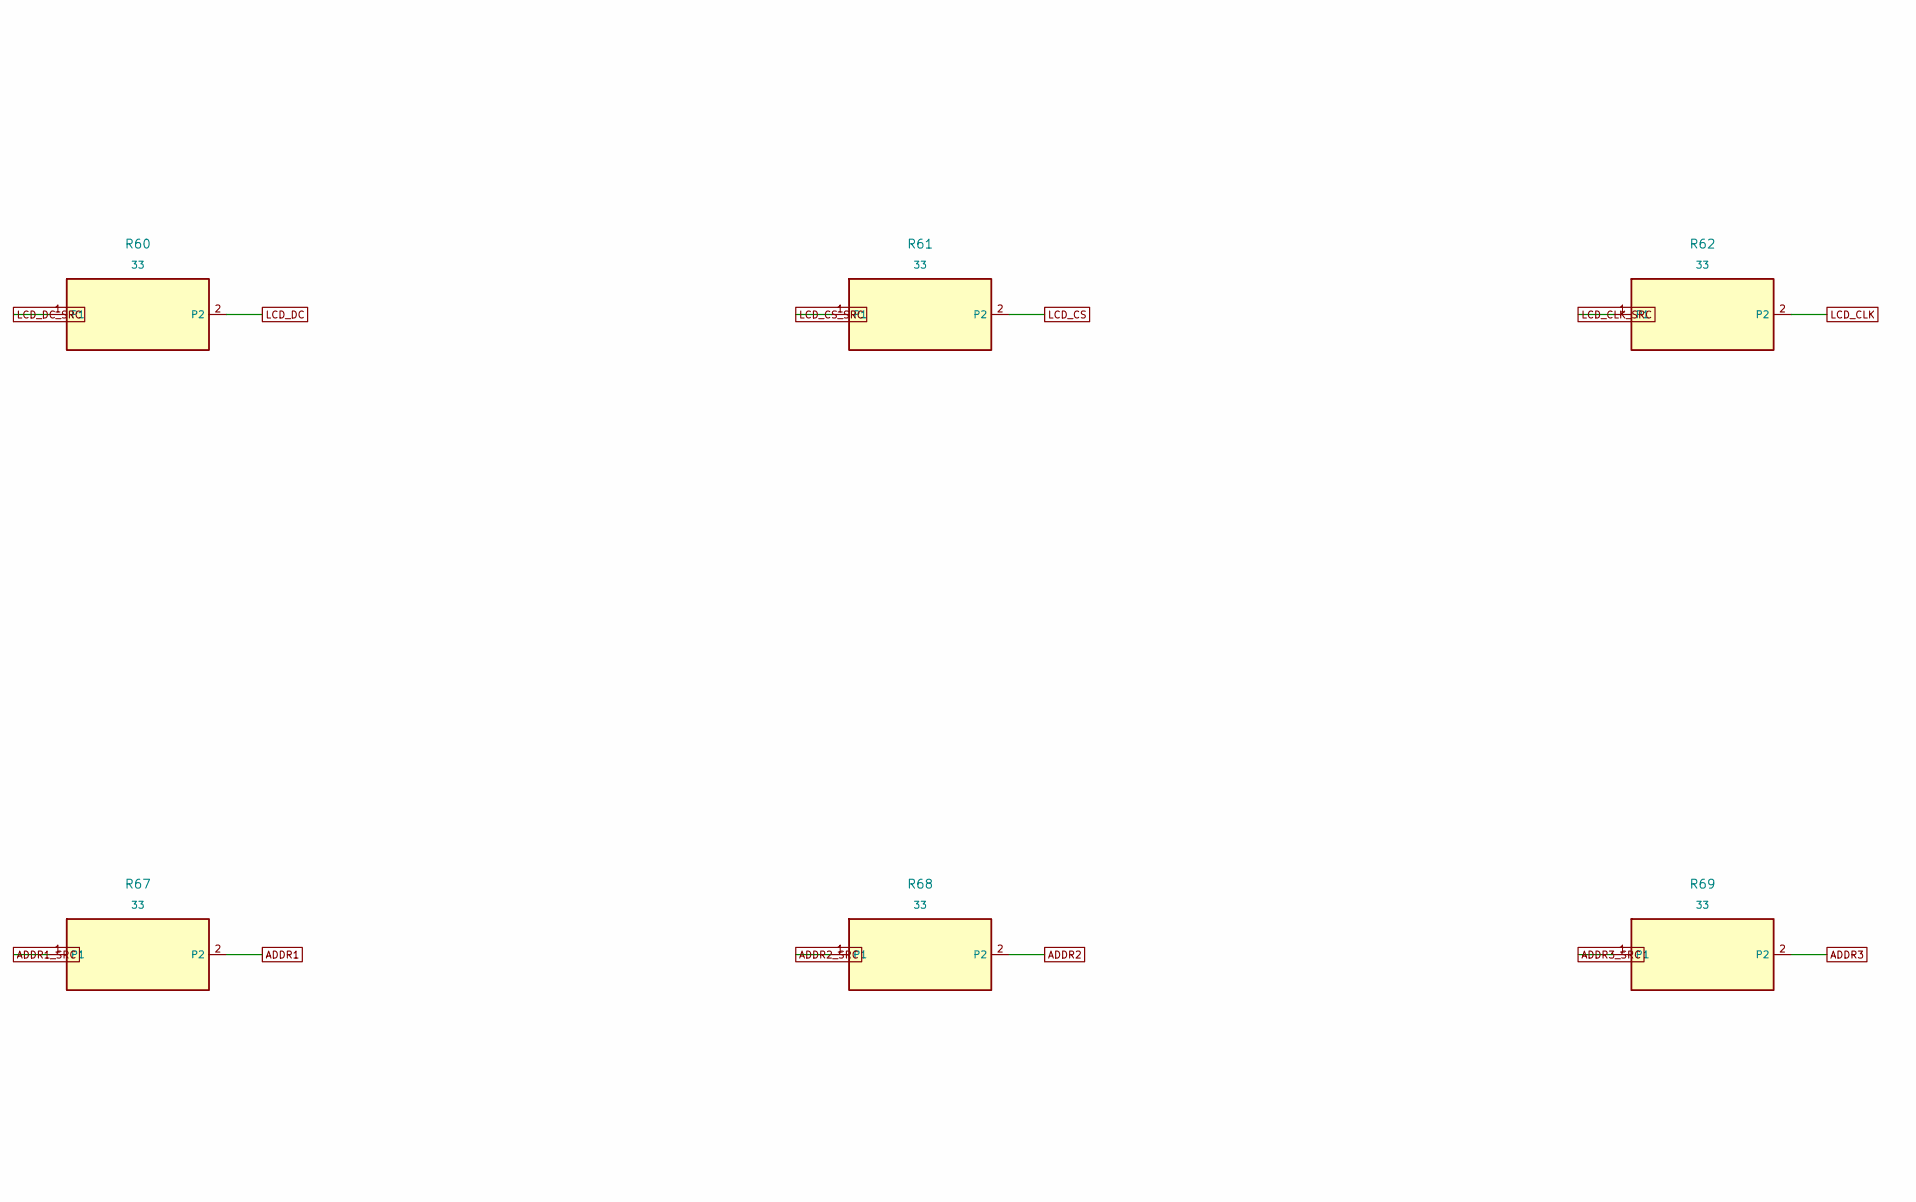
[picture p34: schematic module-interfaces.kicad_sch, part in row 1, column 3]

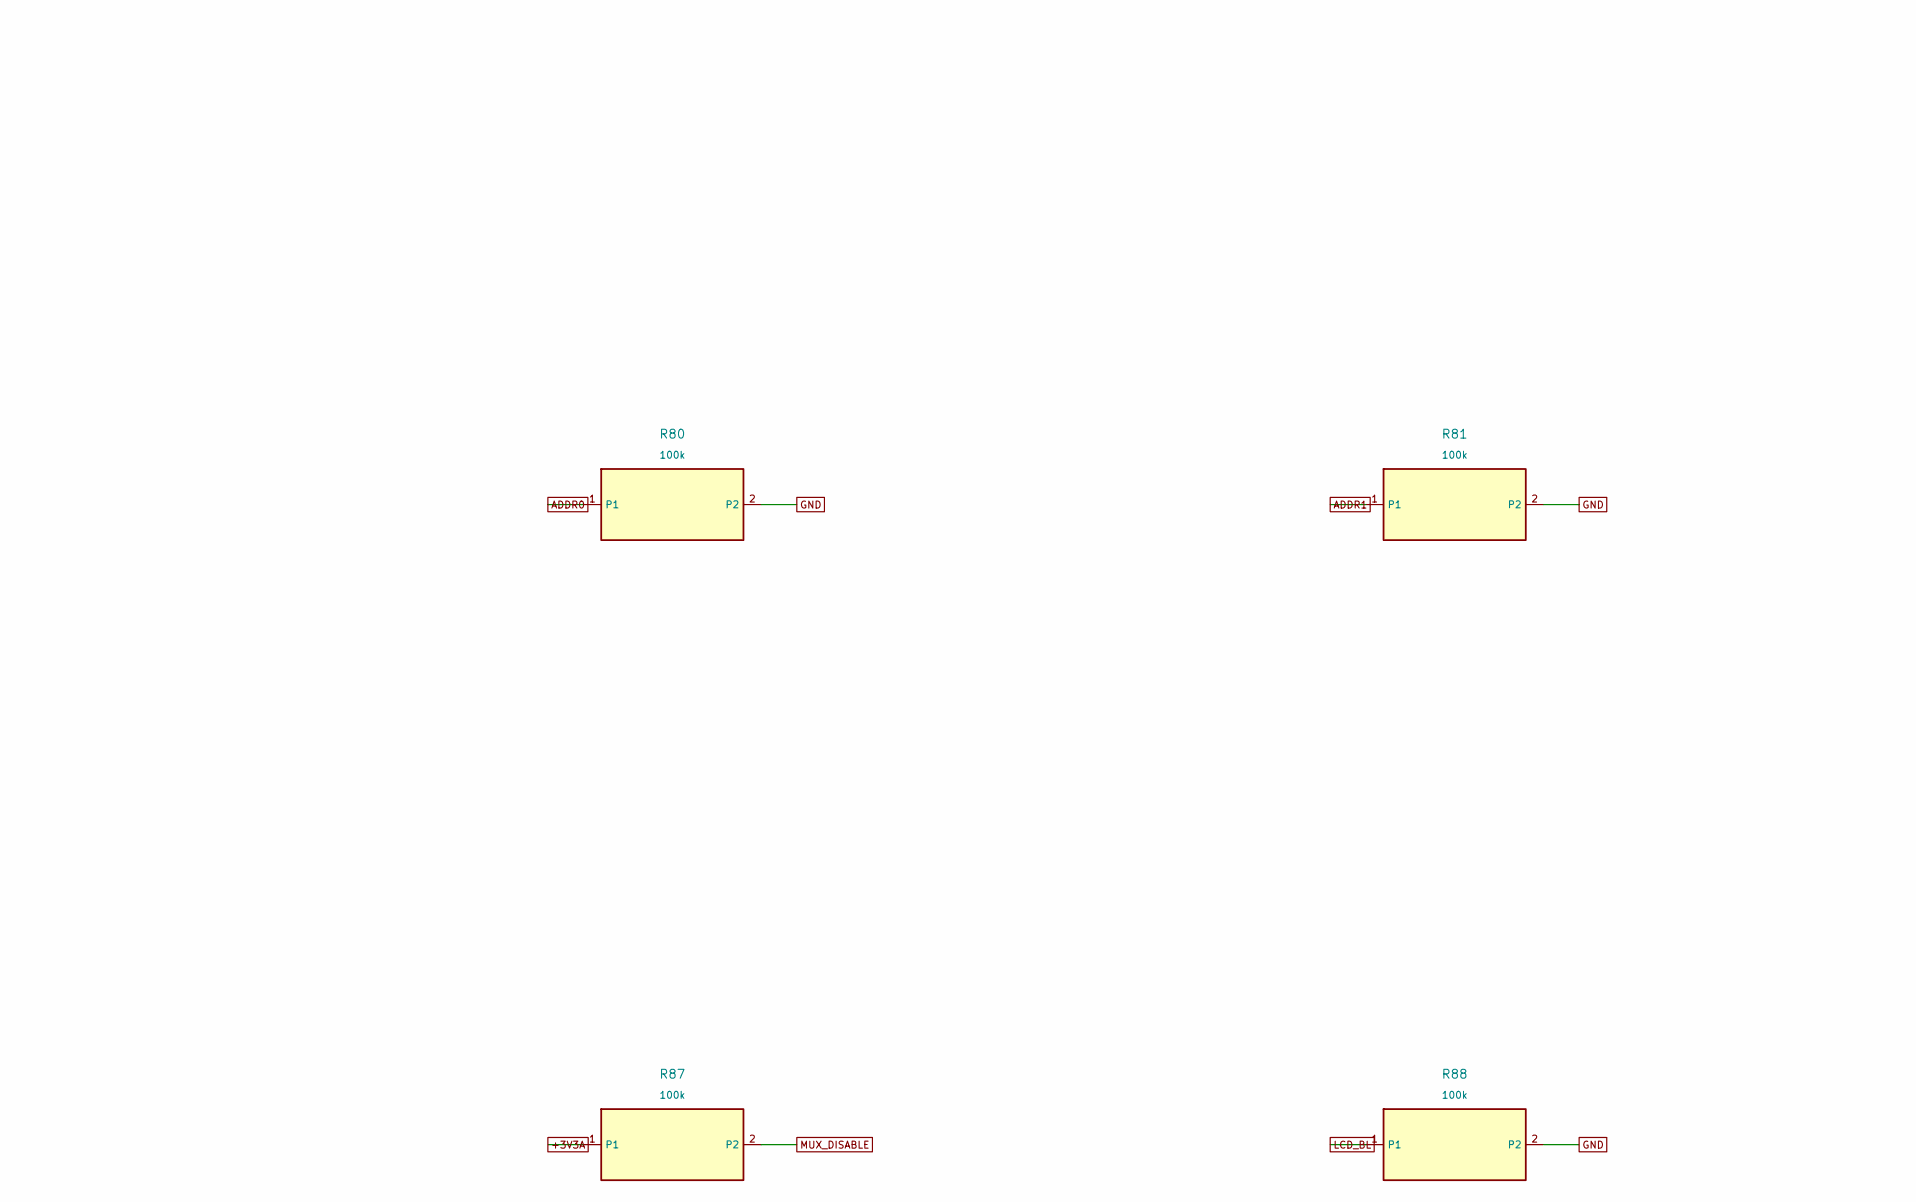
[picture p35: schematic module-interfaces.kicad_sch, part in row 2, column 1]

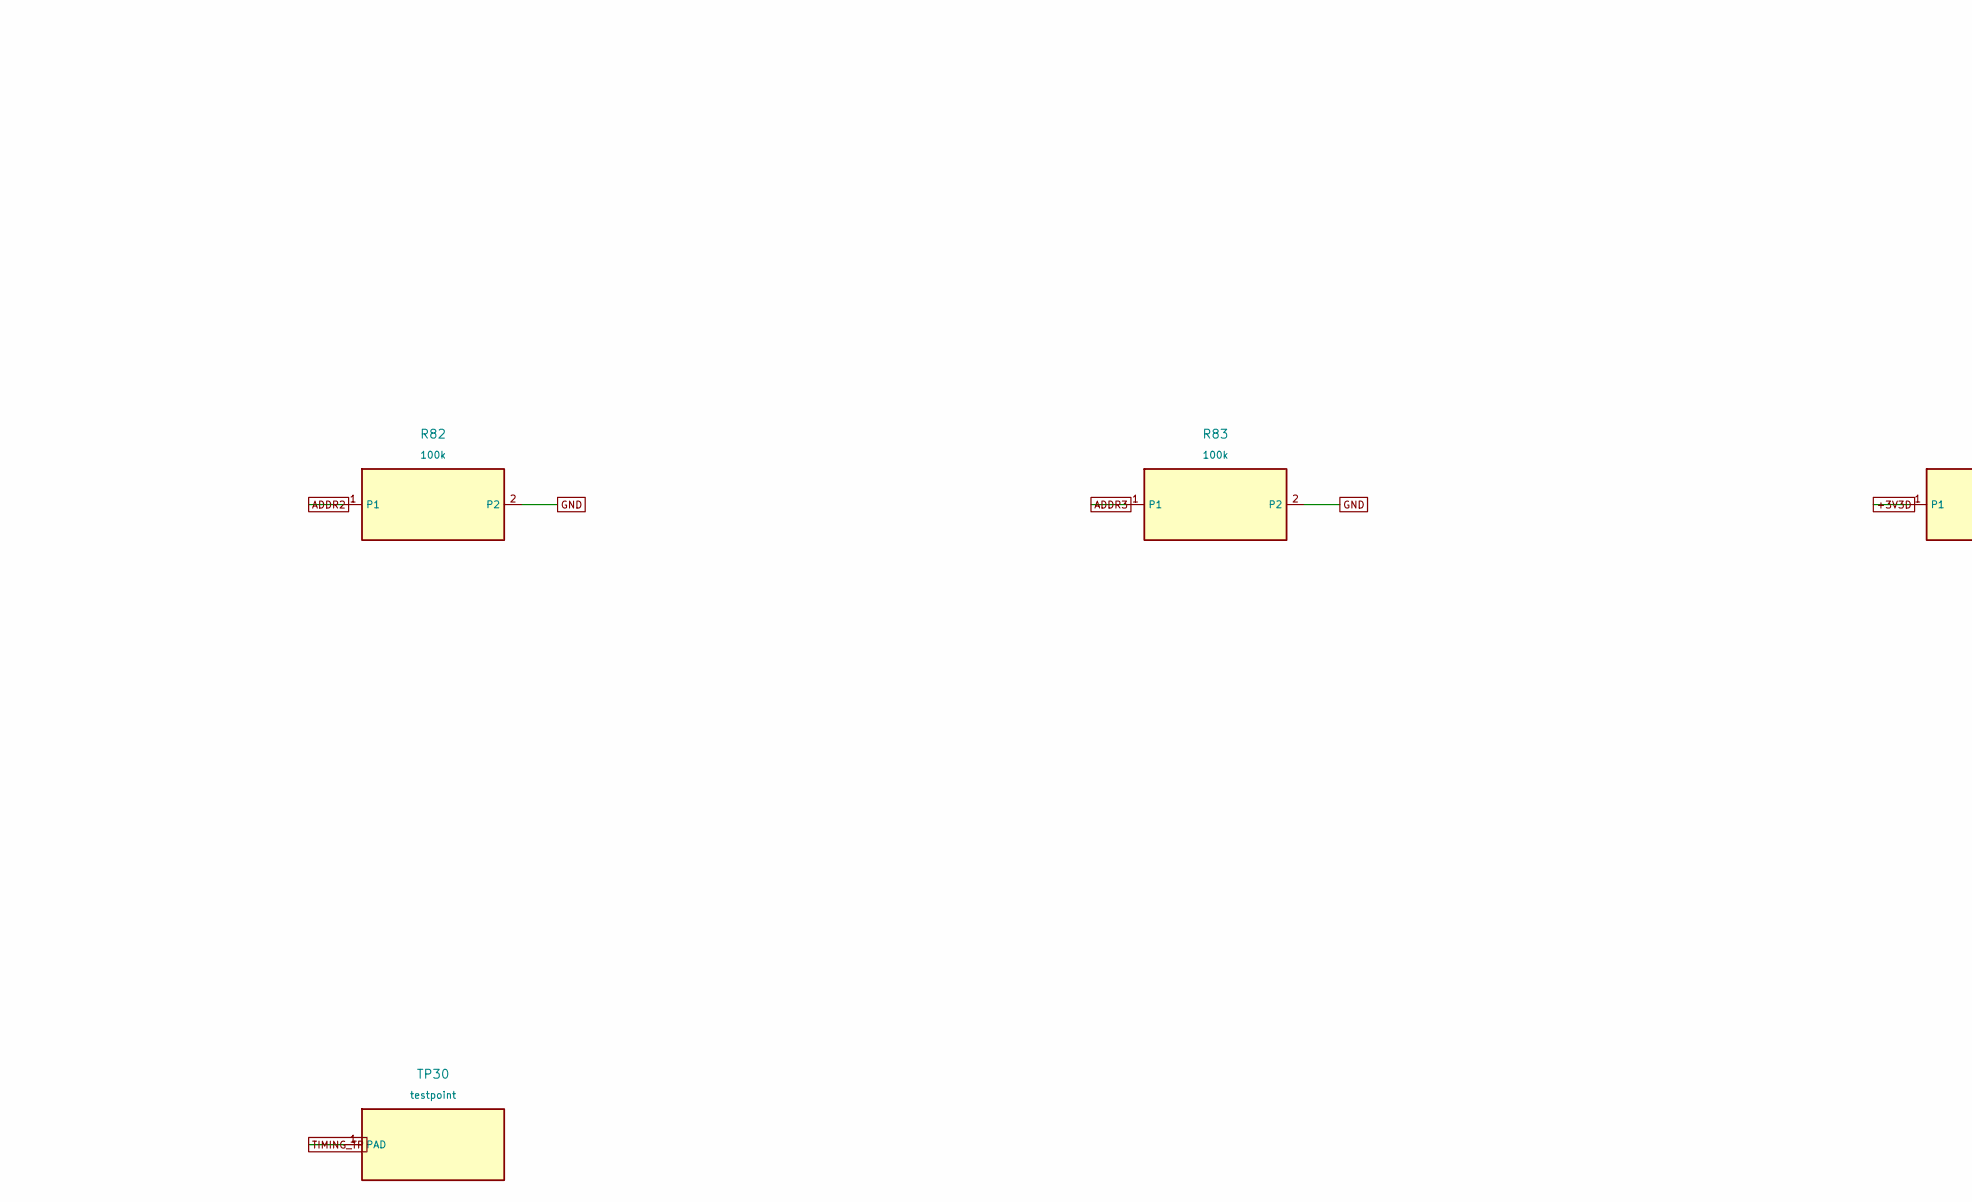
[picture p36: schematic module-interfaces.kicad_sch, part in row 2, column 2]

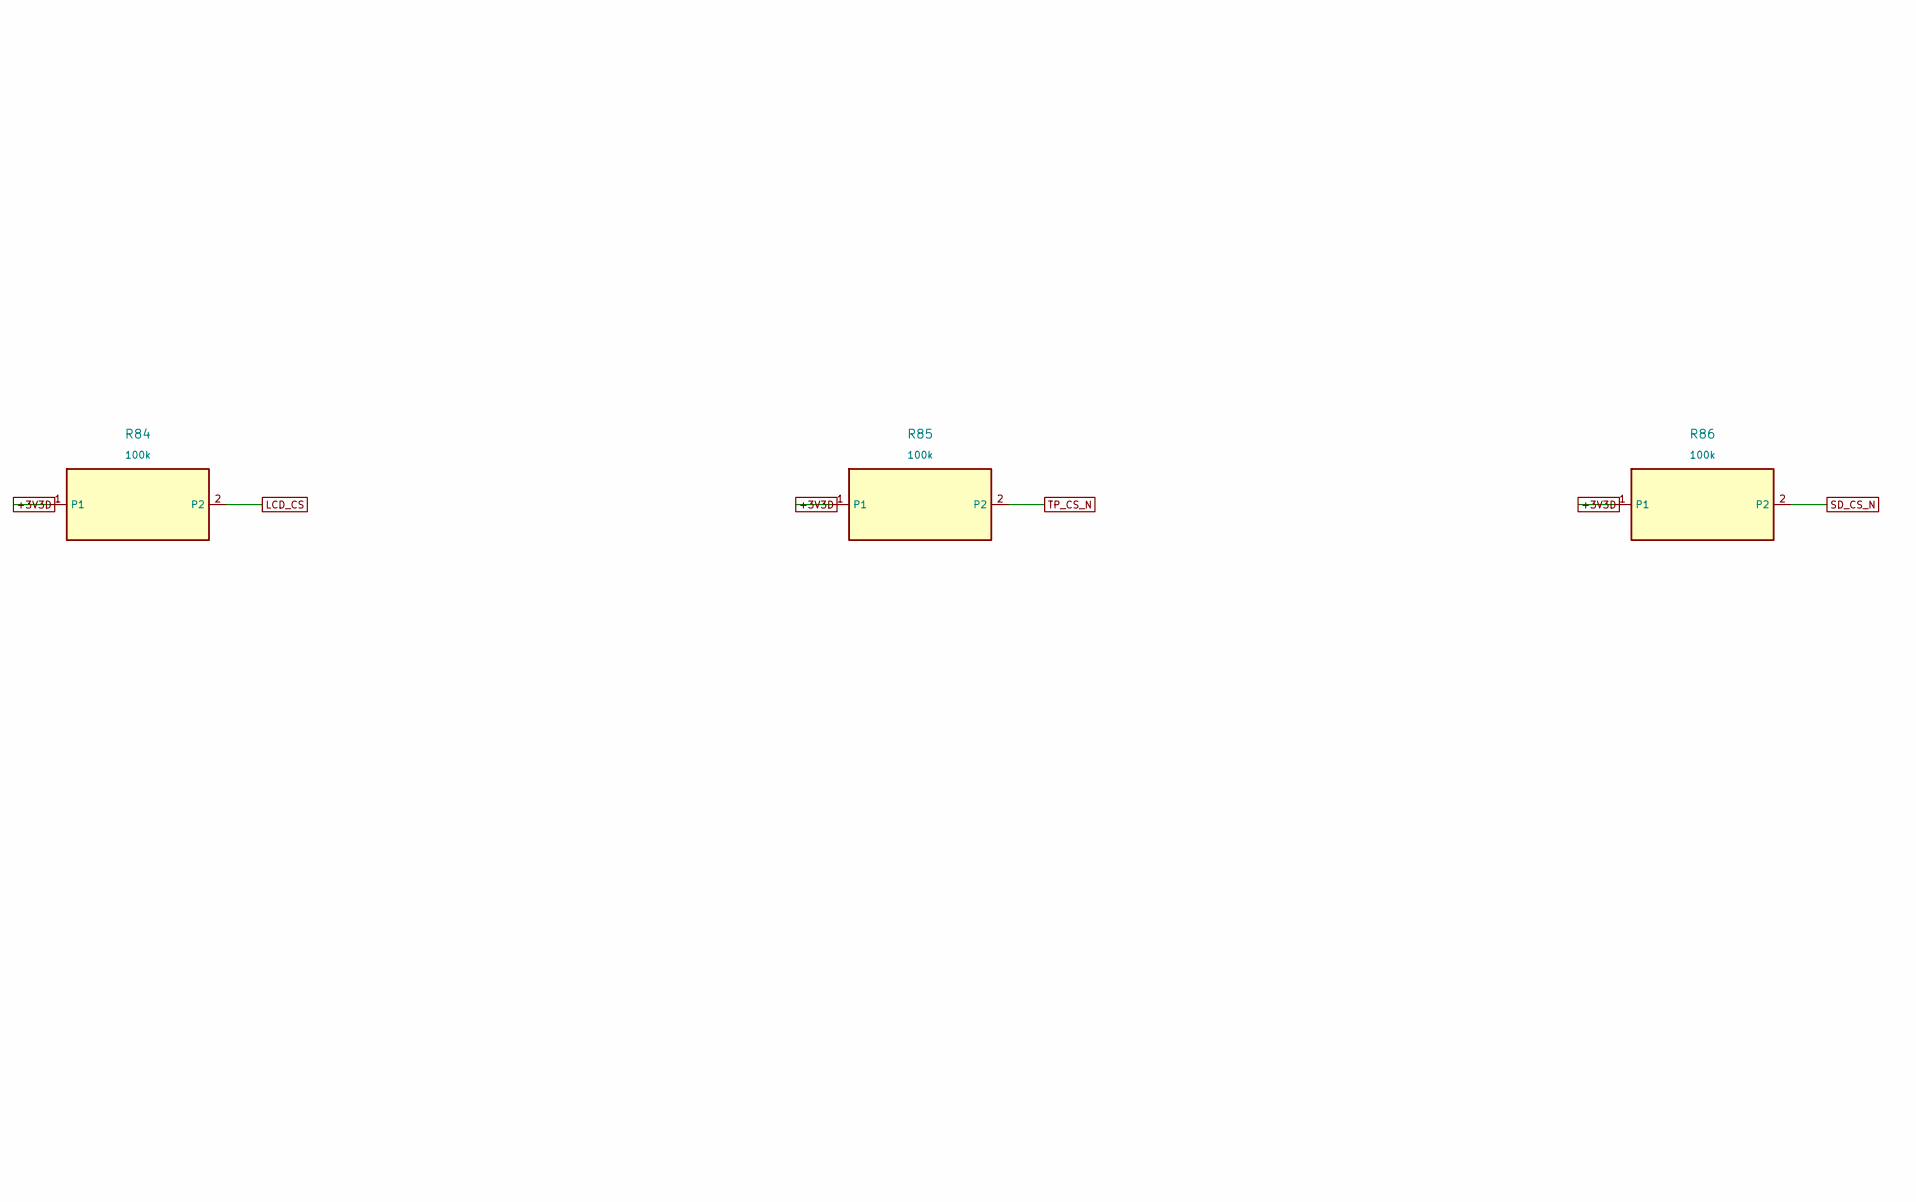
[picture p37: schematic module-interfaces.kicad_sch, part in row 2, column 3]

Parts:
J20, J21: socket20; PinSocket_1x20_P2.54mm_Vertical
J30, J31: header20; PinHeader_1x20_P2.54mm_Vertical
R60, R61, R62, R63, R64, R65, R66, R67, R68, R69: 33; R_0603_1608Metric
R80, R81, R82, R83, R84, R85, R86, R87, R88: 100k; R_0603_1608Metric
TP30: testpoint; TestPoint_Pad_D1.0mm

Connections:
+3V3A: R87.1
+3V3D: J21.5, R84.1, R85.1, R86.1
+5V_FUSED: J31.2
ADC0: J21.10
ADC1: J21.9
ADC2: J21.7
ADDR0: R66.2, R80.1
ADDR0_SRC: J20.4, R66.1
ADDR1: R67.2, R81.1
ADDR1_SRC: J20.5, R67.1
ADDR2: R68.2, R82.1
ADDR2_SRC: J20.6, R68.1
ADDR3: R69.2, R83.1
ADDR3_SRC: J20.7, R69.1
GND: J20.3, J20.8, J20.13, J20.18, J21.3, J21.8, J21.13, J21.18, J30.3, J30.8, J30.13, J30.18, J31.3, J31.8, J31.13, J31.18, R80.2, R81.2, R82.2, R83.2, R88.2
HOLD_N: J20.1
LCD_BL: J30.17, R64.2, R88.1
LCD_BL_SRC: J20.17, R64.1
LCD_CLK: J30.14, R62.2
LCD_CLK_SRC: J20.14, R62.1
LCD_CS: J30.12, R61.2, R84.2
LCD_CS_SRC: J20.12, R61.1
LCD_DC: J30.11, R60.2
LCD_DC_SRC: J20.11, R60.1
LCD_MISO: J20.16, J30.16
LCD_MOSI: J30.15, R63.2
LCD_MOSI_SRC: J20.15, R63.1
LCD_RST: J30.20, R65.2
LCD_RST_SRC: J20.20, R65.1
LINK_N: J20.2
MUX_DISABLE: J20.10, R87.2
SD_CS_N: J21.12, J31.12, R86.2
TIMING_TP: J20.19, TP30.1
TP_CS_N: J21.20, J31.20, R85.2
VBUS_USB: J21.1

Notes on the sheet:
NOT FOR FABRICATION - exact footprints and interface gates remain OPEN
