Takazudo/zudo-scope10/hardware/kicad/power.kicad_sch

## KiCad design hardware/kicad/power.kicad_sch (2026-09-26)

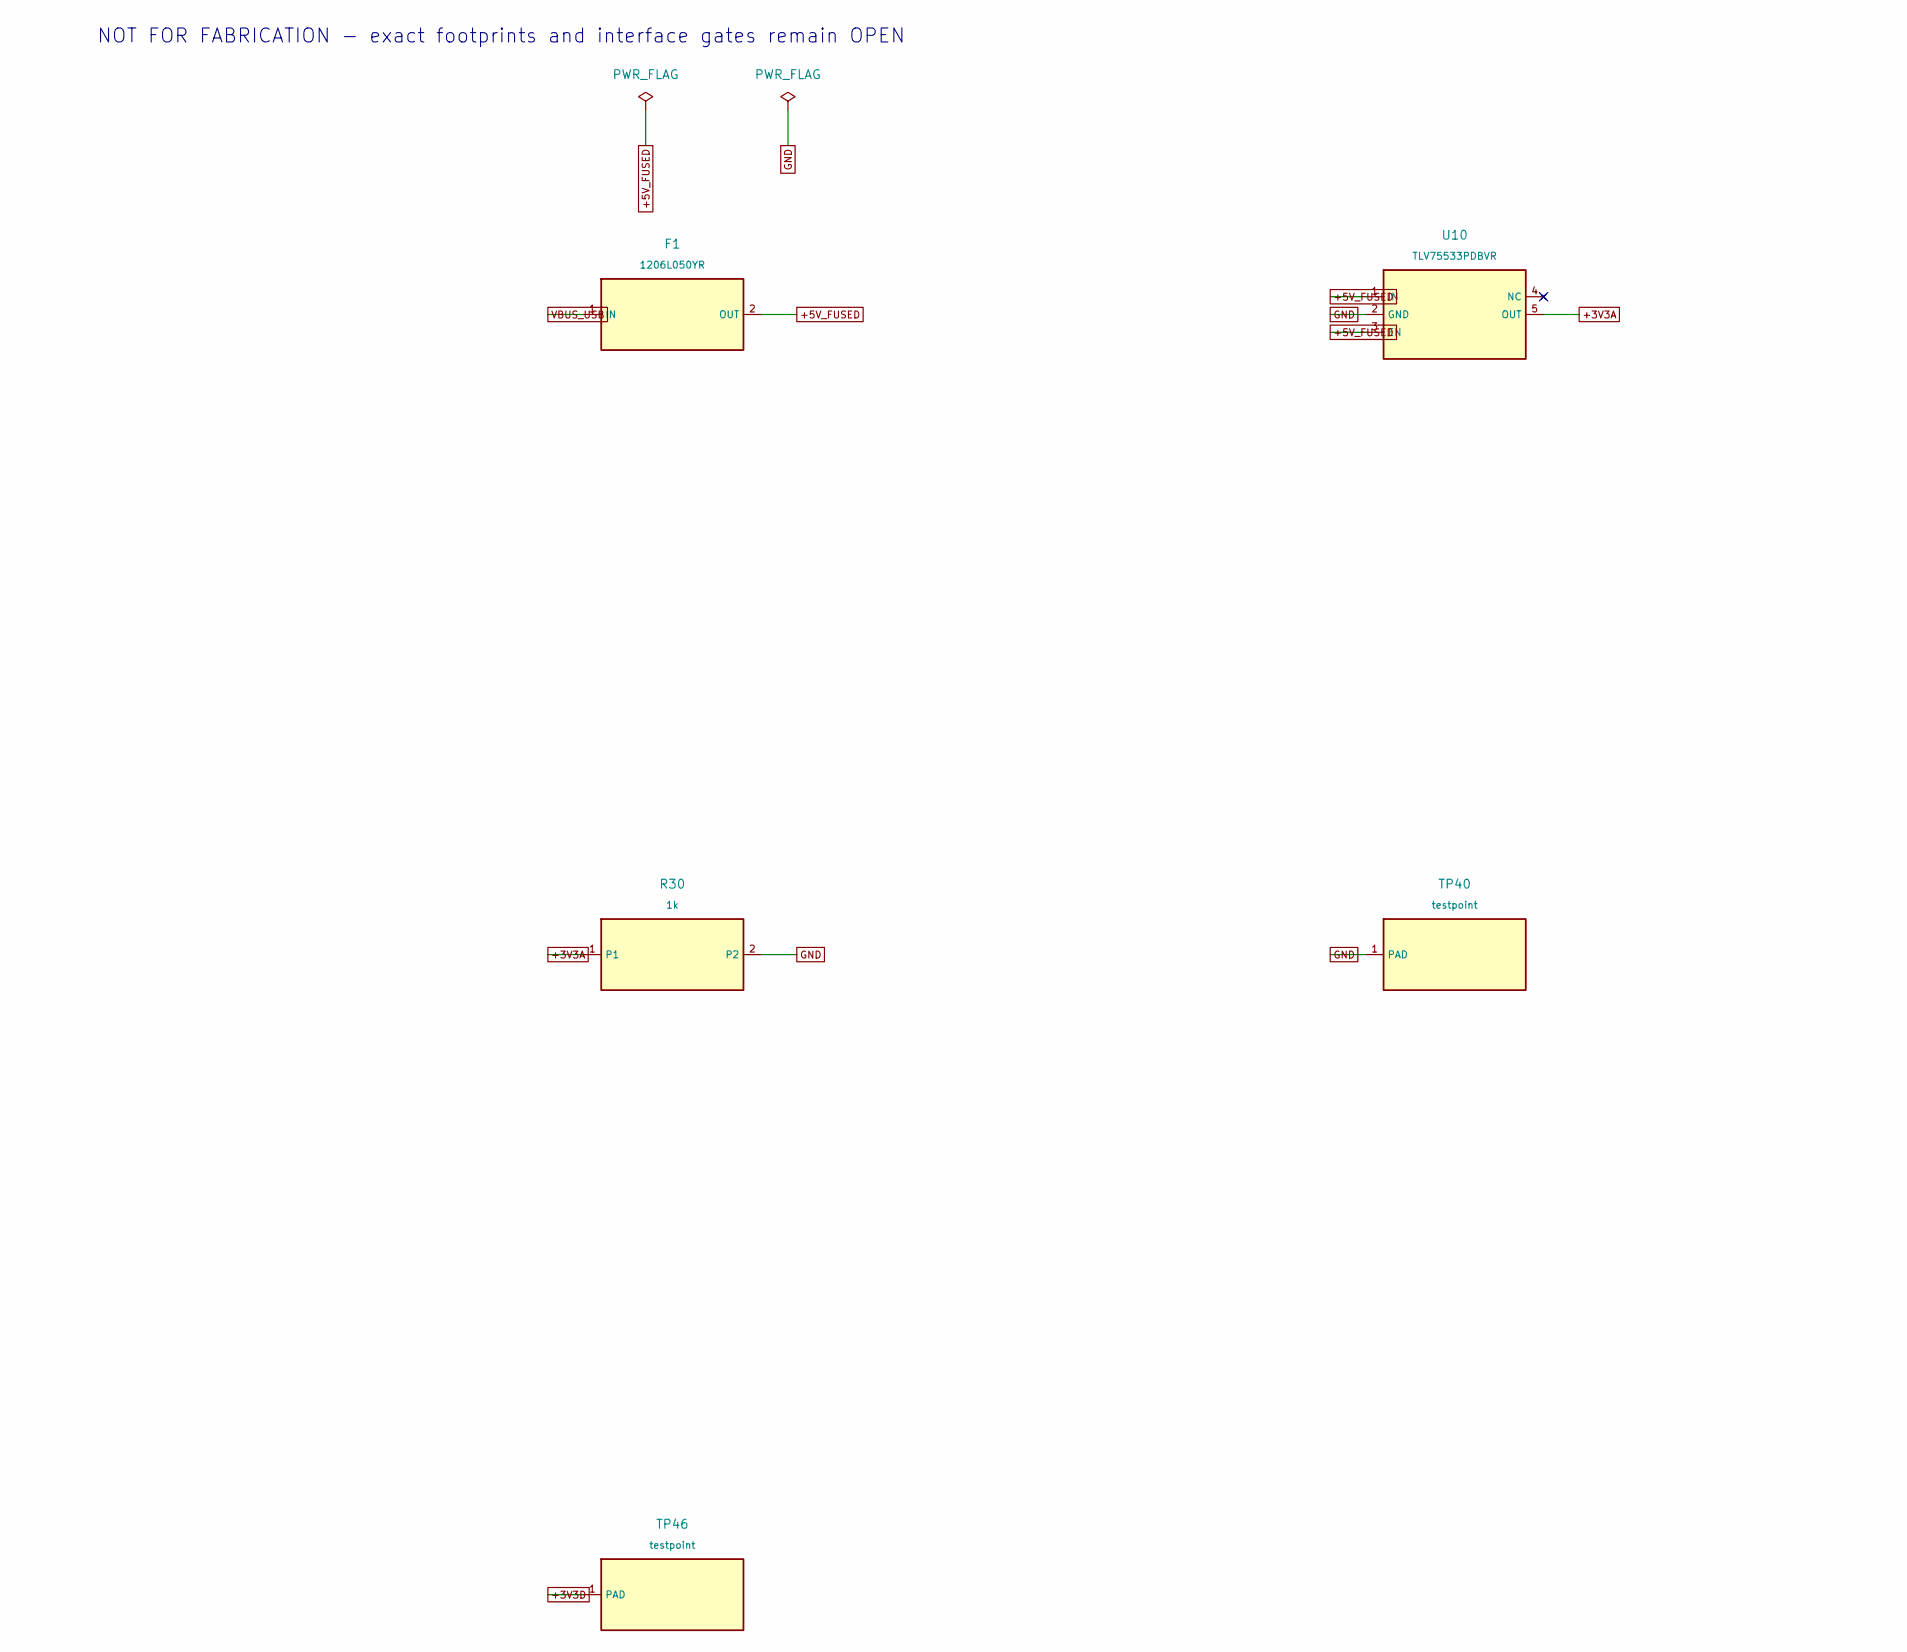
[picture p38: schematic power.kicad_sch, part in row 1, column 1]

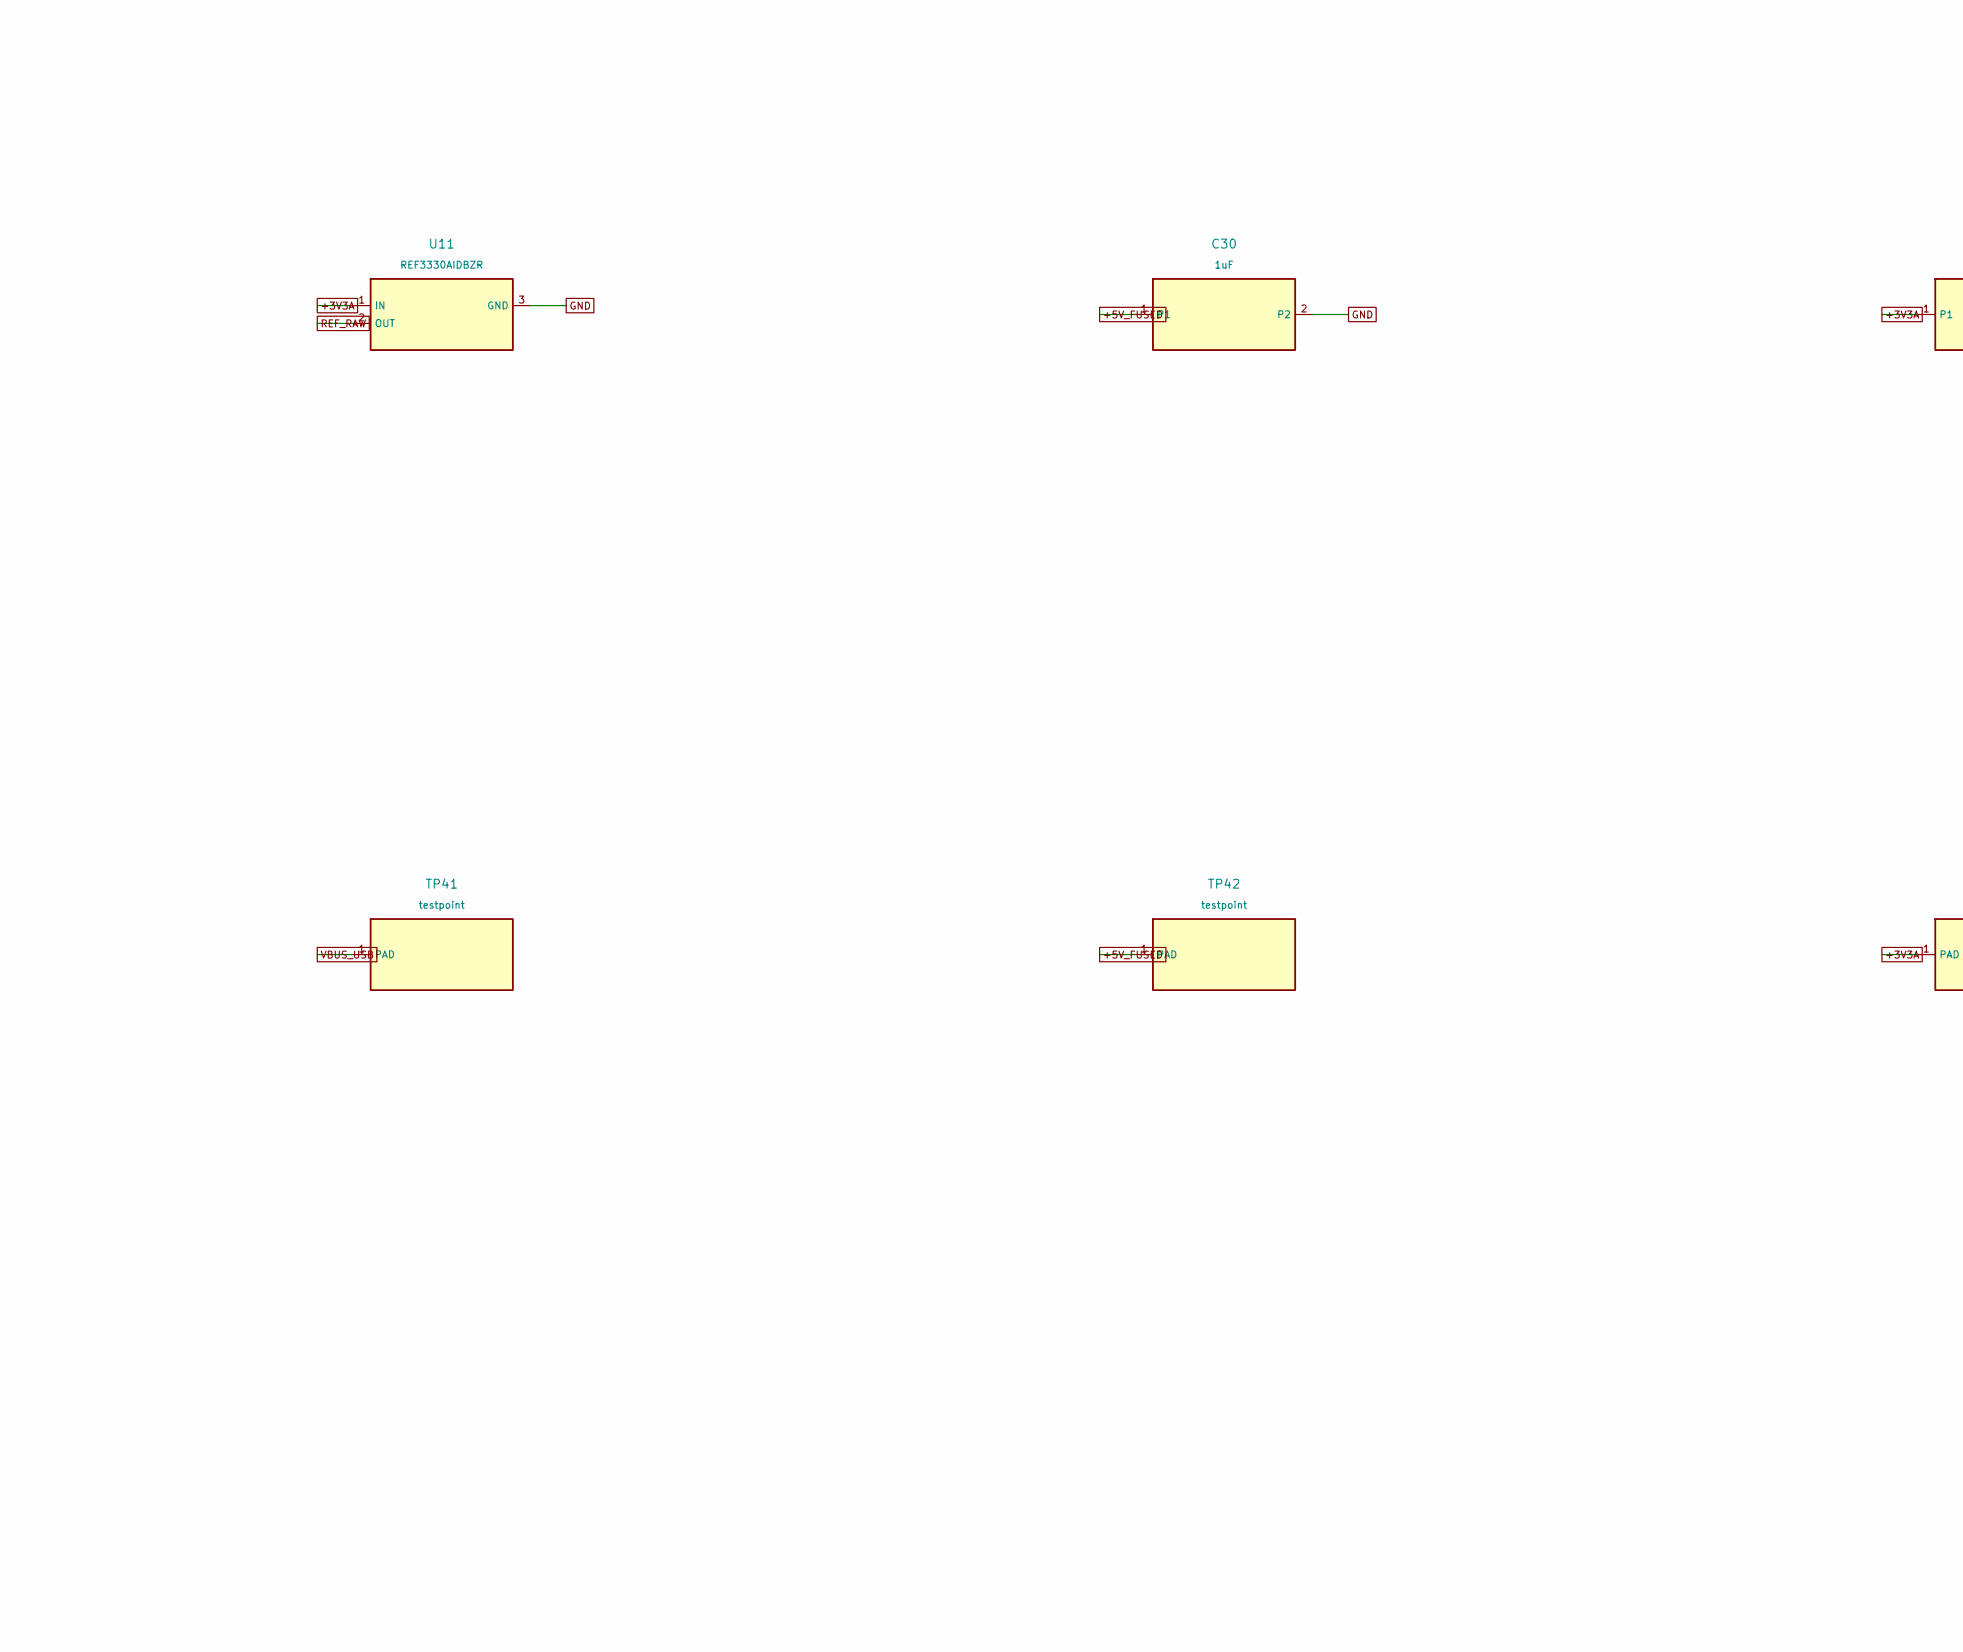
[picture p39: schematic power.kicad_sch, part in row 1, column 2]

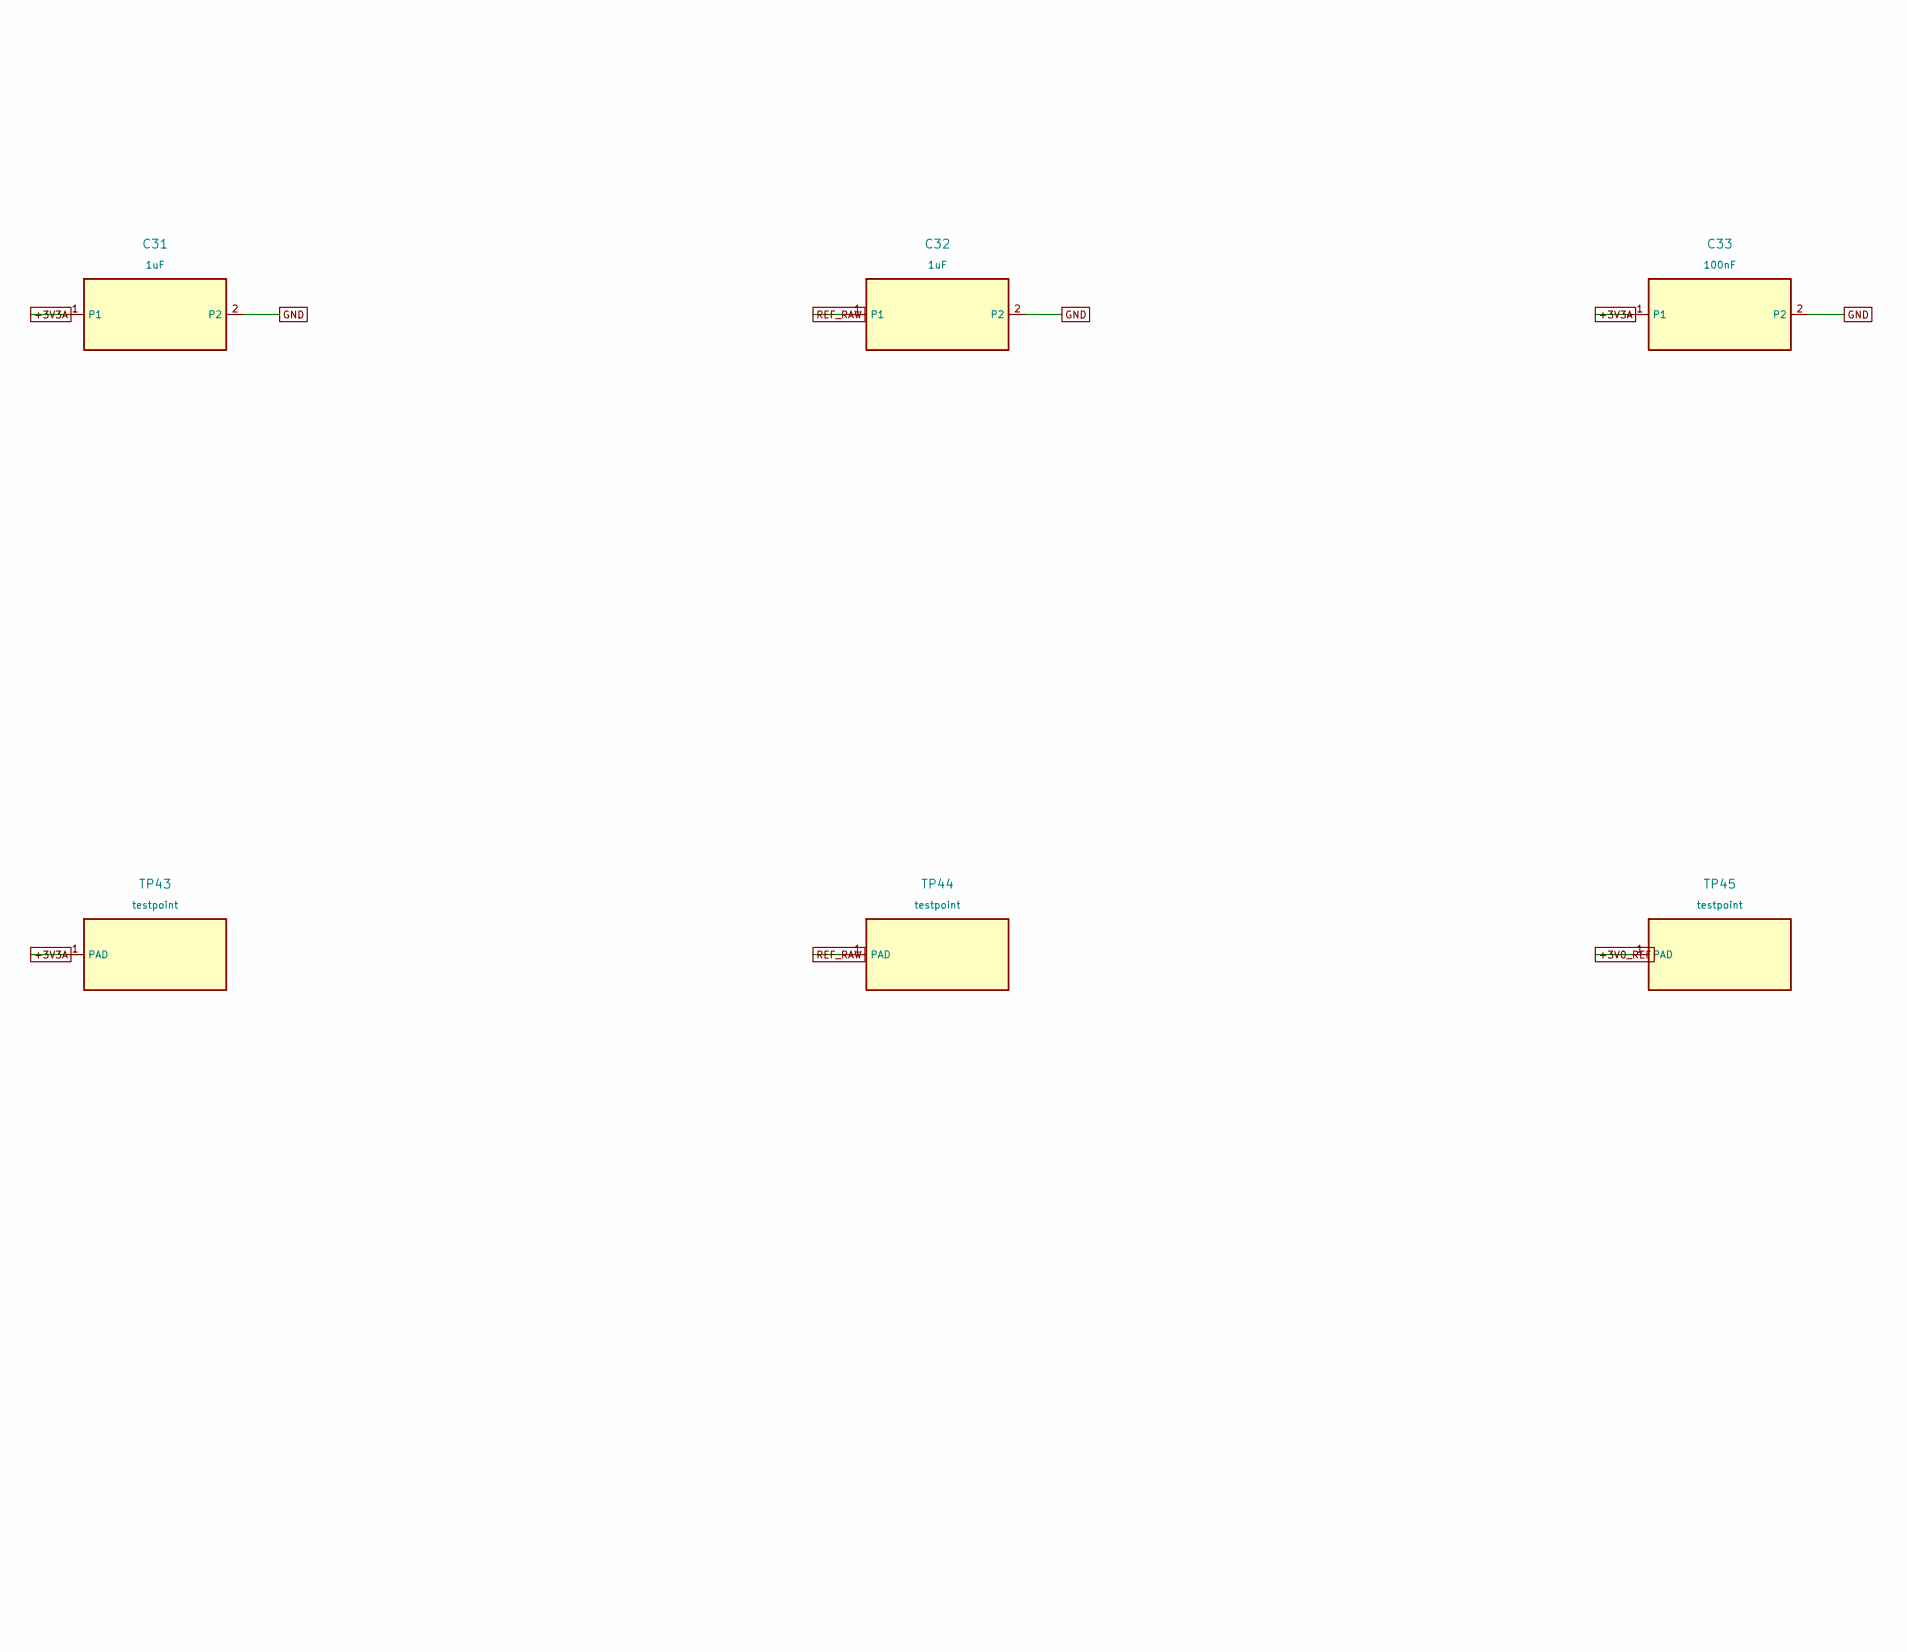
[picture p40: schematic power.kicad_sch, part in row 1, column 3]

Parts:
C30, C31, C32: 1uF; C_0805_2012Metric
C33: 100nF; C_0603_1608Metric
F1: 1206L050YR
R30: 1k; R_0603_1608Metric
TP40, TP41, TP42, TP43, TP44, TP45, TP46: testpoint; TestPoint_Pad_D1.0mm
U10: TLV75533PDBVR; SOT-23-5
U11: REF3330AIDBZR; SOT-23

Connections:
+3V0_REF: TP45.1
+3V3A: C31.1, C33.1, R30.1, TP43.1, U10.5 (OUT), U11.1 (IN)
+3V3D: TP46.1
+5V_FUSED: C30.1, F1.2 (OUT), TP42.1, U10.1 (IN), U10.3 (EN)
GND: C30.2, C31.2, C32.2, C33.2, R30.2, TP40.1, U10.2 (GND), U11.3 (GND)
REF_RAW: C32.1, TP44.1, U11.2 (OUT)
VBUS_USB: F1.1 (IN), TP41.1

Notes on the sheet:
NOT FOR FABRICATION - exact footprints and interface gates remain OPEN
