Takazudo/zudo-scope10/firmware/src/scope_render.c

#include "scope_render.h"
#include "display_port.h"
#include <string.h>

#define ITEM_STATIC 0u
#define ITEM_COL0 1u
#define ITEM_TEXT0 (ITEM_COL0 + SCOPE_PLOT_W)
#define ITEM_END (ITEM_TEXT0 + SCOPE_FIELD_COUNT)
#define CELLS_PER_CALL (SCOPE_RENDER_FILL_MAX / (SCOPE_CELL_W * SCOPE_CELL_H))

_Static_assert(SCOPE_PANE_COLS * SCOPE_PANE_ROWS == SCOPE_CHANNELS, "one pane per channel");
_Static_assert(SCOPE_PANE_COLS * SCOPE_PANE_W == SCOPE_DISPLAY_WIDTH, "two pane columns fill the width");
_Static_assert(SCOPE_PANE_ROWS * SCOPE_PANE_H == SCOPE_DISPLAY_HEIGHT, "five pane rows fill the height");
_Static_assert(SCOPE_TAG_X + SCOPE_TAG_W < SCOPE_PLOT_X, "tag and plot overlap");
_Static_assert(SCOPE_PLOT_X + SCOPE_PLOT_W <= SCOPE_PANE_W, "plot leaves its pane");
_Static_assert(SCOPE_LABEL_Y + SCOPE_LABEL_H < SCOPE_PLOT_Y, "label row and plot overlap");
_Static_assert(SCOPE_PLOT_Y + SCOPE_PLOT_H < SCOPE_STATUS_Y, "plot and status row overlap");
_Static_assert(SCOPE_STATUS_Y + SCOPE_STATUS_H < SCOPE_PANE_H - 1u, "status row hits separator");
_Static_assert(SCOPE_PLOT_H <= SCOPE_RENDER_FILL_MAX, "plot column exceeds one transfer");
_Static_assert(SCOPE_CELL_H == SCOPE_LABEL_H && SCOPE_CELL_H == SCOPE_STATUS_H, "text cells fill a text row");
_Static_assert(SCOPE_GLYPH_W < SCOPE_CELL_W && SCOPE_GLYPH_Y + SCOPE_GLYPH_H <= SCOPE_CELL_H, "glyph leaves its cell");
_Static_assert(CELLS_PER_CALL >= 1u, "one text cell exceeds one transfer");

/* Clean-room 5 x 7 glyphs drawn for this project (no third-party font data); bit 4 = left. */
static const struct { unsigned char c; uint8_t rows[SCOPE_GLYPH_H]; } font[] = {
    {' ', {0x00, 0x00, 0x00, 0x00, 0x00, 0x00, 0x00}},
    {'0', {0x0E, 0x11, 0x13, 0x15, 0x19, 0x11, 0x0E}},
    {'1', {0x04, 0x0C, 0x04, 0x04, 0x04, 0x04, 0x0E}},
    {'2', {0x0E, 0x11, 0x01, 0x02, 0x04, 0x08, 0x1F}},
    {'3', {0x1F, 0x02, 0x04, 0x02, 0x01, 0x11, 0x0E}},
    {'4', {0x02, 0x06, 0x0A, 0x12, 0x1F, 0x02, 0x02}},
    {'5', {0x1F, 0x10, 0x1E, 0x01, 0x01, 0x11, 0x0E}},
    {'6', {0x06, 0x08, 0x10, 0x1E, 0x11, 0x11, 0x0E}},
    {'7', {0x1F, 0x01, 0x02, 0x04, 0x08, 0x08, 0x08}},
    {'8', {0x0E, 0x11, 0x11, 0x0E, 0x11, 0x11, 0x0E}},
    {'9', {0x0E, 0x11, 0x11, 0x0F, 0x01, 0x02, 0x0C}},
    {'.', {0x00, 0x00, 0x00, 0x00, 0x00, 0x0C, 0x0C}},
    {'+', {0x00, 0x04, 0x04, 0x1F, 0x04, 0x04, 0x00}},
    {'-', {0x00, 0x00, 0x00, 0x1F, 0x00, 0x00, 0x00}},
    {(unsigned char)SCOPE_CHAR_PM, {0x04, 0x04, 0x1F, 0x04, 0x04, 0x00, 0x1F}},
    {'?', {0x0E, 0x11, 0x01, 0x02, 0x04, 0x00, 0x04}},
    {'V', {0x11, 0x11, 0x11, 0x11, 0x11, 0x0A, 0x04}},
    {'m', {0x00, 0x00, 0x1A, 0x15, 0x15, 0x11, 0x11}},
    {'s', {0x00, 0x00, 0x0E, 0x10, 0x0E, 0x01, 0x1E}},
    {'k', {0x10, 0x10, 0x12, 0x14, 0x18, 0x14, 0x12}},
    {'A', {0x0E, 0x11, 0x11, 0x1F, 0x11, 0x11, 0x11}},
    {'C', {0x0E, 0x11, 0x10, 0x10, 0x10, 0x11, 0x0E}},
    {'D', {0x1C, 0x12, 0x11, 0x11, 0x11, 0x12, 0x1C}},
    {'E', {0x1F, 0x10, 0x10, 0x1E, 0x10, 0x10, 0x1F}},
    {'H', {0x11, 0x11, 0x11, 0x1F, 0x11, 0x11, 0x11}},
    {'I', {0x0E, 0x04, 0x04, 0x04, 0x04, 0x04, 0x0E}},
    {'K', {0x11, 0x12, 0x14, 0x18, 0x14, 0x12, 0x11}},
    {'L', {0x10, 0x10, 0x10, 0x10, 0x10, 0x10, 0x1F}},
    {'N', {0x11, 0x11, 0x19, 0x15, 0x13, 0x11, 0x11}},
    {'O', {0x0E, 0x11, 0x11, 0x11, 0x11, 0x11, 0x0E}},
    {'P', {0x1E, 0x11, 0x11, 0x1E, 0x10, 0x10, 0x10}},
    {'S', {0x0F, 0x10, 0x10, 0x0E, 0x01, 0x01, 0x1E}},
    {'T', {0x1F, 0x04, 0x04, 0x04, 0x04, 0x04, 0x04}},
    {'U', {0x11, 0x11, 0x11, 0x11, 0x11, 0x11, 0x0E}},
    {'W', {0x11, 0x11, 0x11, 0x15, 0x15, 0x15, 0x0A}},
};

/* Text field placement in cells: row 0 = label row, 1 = status row. */
static const struct { uint8_t row, col, width; bool right; } fields[SCOPE_FIELD_COUNT] = {
    [SCOPE_FIELD_ID] = {0, 0, 2, false},
    [SCOPE_FIELD_RANGE] = {0, 4, 3, false},
    [SCOPE_FIELD_WINDOW] = {0, SCOPE_TEXT_CELLS - SCOPE_WINDOW_LABEL_MAX, SCOPE_WINDOW_LABEL_MAX, true},
    [SCOPE_FIELD_CAL] = {0, 8, 5, false},
    [SCOPE_FIELD_TOKEN] = {1, 0, SCOPE_FIELD_MAX, false},
    [SCOPE_FIELD_LINK] = {1, 15, 4, false},
    [SCOPE_FIELD_HOLD] = {1, SCOPE_TEXT_CELLS - 4u, 4, false},
};
_Static_assert(SCOPE_TEXT_CELLS == 24u, "field table assumes a 24-cell text row");

static const uint16_t palette[SCOPE_CHANNELS] = {
    SCOPE_RGB565(255, 220, 0),   SCOPE_RGB565(0, 220, 255),  SCOPE_RGB565(255, 80, 200),
    SCOPE_RGB565(80, 255, 80),   SCOPE_RGB565(255, 120, 40), SCOPE_RGB565(150, 120, 255),
    SCOPE_RGB565(255, 255, 255), SCOPE_RGB565(0, 255, 170),  SCOPE_RGB565(255, 60, 60),
    SCOPE_RGB565(160, 200, 255),
};

static uint16_t pane_left(unsigned pane) { return (uint16_t)((pane / SCOPE_PANE_ROWS) * SCOPE_PANE_W); }
static uint16_t pane_top(unsigned pane) { return (uint16_t)((pane % SCOPE_PANE_ROWS) * SCOPE_PANE_H); }
static scope_rect in_pane(unsigned pane, uint16_t x, uint16_t y, uint16_t w, uint16_t h) {
    return (scope_rect){(uint16_t)(pane_left(pane) + x), (uint16_t)(pane_top(pane) + y), w, h};
}

scope_rect scope_pane_rect(unsigned pane) { return in_pane(pane, 0, 0, SCOPE_PANE_W, SCOPE_PANE_H); }
scope_rect scope_pane_tag_rect(unsigned pane) {
    return in_pane(pane, SCOPE_TAG_X, SCOPE_PLOT_Y, SCOPE_TAG_W, SCOPE_PLOT_H);
}
scope_rect scope_pane_plot_rect(unsigned pane) {
    return in_pane(pane, SCOPE_PLOT_X, SCOPE_PLOT_Y, SCOPE_PLOT_W, SCOPE_PLOT_H);
}
scope_rect scope_pane_label_rect(unsigned pane) {
    return in_pane(pane, SCOPE_PLOT_X, SCOPE_LABEL_Y, SCOPE_PLOT_W, SCOPE_LABEL_H);
}
scope_rect scope_pane_status_rect(unsigned pane) {
    return in_pane(pane, SCOPE_PLOT_X, SCOPE_STATUS_Y, SCOPE_PLOT_W, SCOPE_STATUS_H);
}
scope_rect scope_pane_field_rect(unsigned pane, scope_text_field f) {
    if ((unsigned)f >= SCOPE_FIELD_COUNT) return (scope_rect){0, 0, 0, 0};
    scope_rect row = fields[f].row ? scope_pane_status_rect(pane) : scope_pane_label_rect(pane);
    return (scope_rect){(uint16_t)(row.x + fields[f].col * SCOPE_CELL_W), row.y,
                        (uint16_t)(fields[f].width * SCOPE_CELL_W), SCOPE_CELL_H};
}
scope_rect scope_pane_separator_rect(unsigned pane) {
    return in_pane(pane, 0, (uint16_t)(SCOPE_PANE_H - 1u), SCOPE_PANE_W, 1);
}

uint16_t scope_channel_colour(unsigned ch) { return palette[ch % SCOPE_CHANNELS]; }

float scope_range_volts(int range) {
    static const float volts[3] = {3.0f, 5.0f, 8.0f};
    return volts[range >= 0 && range < 3 ? range : SCOPE_RANGE_STARTUP];
}

uint16_t scope_volts_to_row(float volts, float range_v, uint16_t h) {
    int half = h ? (h - 1) / 2 : 0;
    float off = volts / range_v * (float)half;
    if (!half || !(range_v > 0.0f) || off != off) return (uint16_t)half;
    if (off >= (float)half) return 0;
    if (off <= -(float)half) return (uint16_t)(2 * half);
    int k = (int)(off + (off < 0.0f ? -0.5f : 0.5f)); /* symmetric: -v mirrors +v */
    return (uint16_t)(half - k);
}

void scope_render_column(const scope_bin *bin, scope_calibration cal, float range_v, uint16_t h, uint16_t colour,
                         uint16_t *out) {
    for (uint16_t r = 0; r < h; r++) out[r] = SCOPE_COLOUR_BG;
    if (h) out[scope_volts_to_row(0.0f, range_v, h)] = SCOPE_COLOUR_GRID;
    if (!bin) return;
    float vhi = scope_code_to_volts(bin->hi, cal), vlo = scope_code_to_volts(bin->lo, cal);
    uint16_t a = scope_volts_to_row(vhi, range_v, h), b = scope_volts_to_row(vlo, range_v, h);
    if (a > b) { uint16_t t = a; a = b; b = t; }
    for (uint16_t r = a; r <= b && r < h; r++) out[r] = colour;
    uint16_t bottom = scope_volts_to_row(-range_v, range_v, h);
    if (vhi > range_v) {
        if (b > 0u) out[1] = SCOPE_COLOUR_BG;
        out[0] = SCOPE_COLOUR_CLIP;
    }
    if (vlo < -range_v && bottom < h) {
        if (a < bottom) out[bottom - 1u] = SCOPE_COLOUR_BG;
        out[bottom] = SCOPE_COLOUR_CLIP;
    }
}

scope_status_token scope_bins_status(const scope_bin *bins, unsigned n, scope_calibration cal, float range_v) {
    scope_status_token t = SCOPE_STATUS_NONE;
    for (unsigned i = 0; bins && i < n; i++) {
        if (bins[i].lo == 0u || bins[i].hi >= 4095u) return SCOPE_STATUS_ADC_SAT;
        float vlo = scope_code_to_volts(bins[i].lo, cal), vhi = scope_code_to_volts(bins[i].hi, cal);
        if (vhi > range_v || vlo < -range_v) t = SCOPE_STATUS_VIEW_CLIP;
    }
    return t;
}

uint16_t scope_render_time_code(const scope_render_input *in, unsigned pane) {
    return in->link ? in->time_code[0] : in->time_code[pane % SCOPE_CHANNELS];
}

unsigned scope_render_window_label(uint16_t time_code, uint32_t samples_per_s, char out[SCOPE_WINDOW_LABEL_MAX + 1u]) {
    uint32_t us = samples_per_s
        ? (uint32_t)(((uint64_t)scope_window_samples(time_code, samples_per_s) * 1000000u + samples_per_s / 2u)
                     / samples_per_s)
        : (uint32_t)(scope_time_seconds(time_code) * 1e6f + 0.5f);
    unsigned n = 0;
    char d[8];
    unsigned nd = 0, point, value;
    const char *unit;
    if (us < 99950u) { value = (us + 50u) / 100u; point = 1; unit = "ms"; }          /* 2.0ms .. 99.9ms */
    else if (us < 999500u) { value = (us + 500u) / 1000u; point = 0; unit = "ms"; }  /* 100ms .. 999ms */
    else { value = (us + 5000u) / 10000u; point = 2; unit = "s"; }                     /* 1.00s .. 8.19s */
    do { d[nd++] = (char)('0' + value % 10u); value /= 10u; } while (value || nd <= point);
    while (nd && n < SCOPE_WINDOW_LABEL_MAX) {
        out[n++] = d[--nd];
        if (nd == point && point && n < SCOPE_WINDOW_LABEL_MAX) out[n++] = '.';
    }
    for (; *unit && n < SCOPE_WINDOW_LABEL_MAX; unit++) out[n++] = *unit;
    out[n] = '\0';
    return n;
}

const char *scope_status_token_text(unsigned token) {
    switch (token) {
    case SCOPE_STATUS_UNCAL: return "UNCAL";
    case SCOPE_STATUS_VIEW_CLIP: return "VIEW CLIP";
    case SCOPE_STATUS_ADC_SAT: return "ADC SAT";
    default: return "";
    }
}

const uint8_t *scope_font_glyph(unsigned char c) {
    for (unsigned i = 0; i < sizeof font / sizeof font[0]; i++)
        if (font[i].c == c) return font[i].rows;
    return NULL;
}

void scope_render_init(scope_render_state *s) {
    *s = (scope_render_state){0};
    for (unsigned ch = 0; ch < SCOPE_CHANNELS; ch++) s->view_range[ch] = SCOPE_RANGE_STARTUP;
}

static void count(scope_render_state *s, bool ok) {
    if (ok) s->rects_sent++; else s->rects_failed++;
}

static unsigned fill(scope_render_state *s, scope_rect r, uint16_t colour) {
    static uint16_t solid[SCOPE_RENDER_FILL_MAX];
    for (unsigned i = 0; i < SCOPE_RENDER_FILL_MAX; i++) solid[i] = colour;
    unsigned calls = 0;
    for (uint16_t x = 0; x < r.w; x = (uint16_t)(x + SCOPE_RENDER_FILL_MAX)) {
        unsigned left = (unsigned)r.w - x;
        uint16_t w = (uint16_t)(left < SCOPE_RENDER_FILL_MAX ? left : SCOPE_RENDER_FILL_MAX);
        uint16_t rows = (uint16_t)(SCOPE_RENDER_FILL_MAX / w);
        for (uint16_t y = 0; y < r.h; y = (uint16_t)(y + rows)) {
            unsigned down = (unsigned)r.h - y;
            uint16_t h = (uint16_t)(down < rows ? down : rows);
            count(s, scope_display_rect((uint16_t)(r.x + x), (uint16_t)(r.y + y), w, h, solid));
            calls++;
        }
    }
    return calls;
}

/* Draws cells of text (unknown characters as blanks), CELLS_PER_CALL cells per display call. */
static unsigned draw_text(scope_render_state *s, uint16_t x, uint16_t y, const char *text, unsigned ncells,
                          uint16_t colour, bool *ok) {
    uint16_t px[CELLS_PER_CALL * SCOPE_CELL_W * SCOPE_CELL_H];
    unsigned calls = 0;
    for (unsigned c0 = 0; c0 < ncells; c0 += CELLS_PER_CALL) {
        unsigned n = ncells - c0 < CELLS_PER_CALL ? ncells - c0 : CELLS_PER_CALL;
        uint16_t w = (uint16_t)(n * SCOPE_CELL_W);
        for (unsigned i = 0; i < (unsigned)w * SCOPE_CELL_H; i++) px[i] = SCOPE_COLOUR_BG;
        for (unsigned k = 0; k < n; k++) {
            const uint8_t *g = scope_font_glyph((unsigned char)text[c0 + k]);
            if (!g) continue;
            for (unsigned r = 0; r < SCOPE_GLYPH_H; r++)
                for (unsigned b = 0; b < SCOPE_GLYPH_W; b++)
                    if (g[r] & (0x10u >> b)) px[(SCOPE_GLYPH_Y + r) * w + k * SCOPE_CELL_W + b] = colour;
        }
        bool sent = scope_display_rect((uint16_t)(x + c0 * SCOPE_CELL_W), y, w, SCOPE_CELL_H, px);
        count(s, sent);
        if (!sent) *ok = false;
        calls++;
    }
    return calls;
}

static void copy_text(char *raw, const char *t) {
    unsigned i = 0;
    for (; t[i] && i < SCOPE_FIELD_MAX; i++) raw[i] = t[i];
    raw[i] = '\0';
}

static void field_content(const scope_render_state *s, const scope_render_input *in, unsigned pane,
                          scope_text_field f, char *raw, uint16_t *colour) {
    static const char range_digit[3] = {'3', '5', '8'};
    *colour = SCOPE_COLOUR_TEXT;
    raw[0] = '\0';
    switch (f) {
    case SCOPE_FIELD_ID:
        raw[0] = (char)('0' + (pane + 1u) / 10u);
        raw[1] = (char)('0' + (pane + 1u) % 10u);
        raw[2] = '\0';
        *colour = scope_channel_colour(pane);
        break;
    case SCOPE_FIELD_RANGE: {
        int r = s->view_range[pane];
        raw[0] = SCOPE_CHAR_PM;
        raw[1] = r >= 0 && r < 3 ? range_digit[r] : '?';
        raw[2] = 'V';
        raw[3] = '\0';
        if (!s->range_known[pane]) *colour = SCOPE_COLOUR_WARN; /* startup scale, switch not yet read */
        break;
    }
    case SCOPE_FIELD_WINDOW: {
        /* Latched with the plot (frozen under HOLD); live only before the pane is first mapped. */
        bool known = s->window_known[pane];
        uint16_t code = known ? s->view_time_code[pane] : scope_render_time_code(in, pane);
        scope_render_window_label(code, in->samples_per_s, raw);
        if (known ? s->view_linked[pane] : in->link) *colour = SCOPE_COLOUR_LINK; /* window from CH1's TIME */
        break;
    }
    case SCOPE_FIELD_CAL:
        if (!scope_calibration_valid(in->cal[pane])) copy_text(raw, scope_status_token_text(SCOPE_STATUS_UNCAL));
        *colour = SCOPE_COLOUR_WARN;
        break;
    case SCOPE_FIELD_TOKEN:
        copy_text(raw, scope_status_token_text(s->signal[pane]));
        *colour = SCOPE_COLOUR_WARN;
        break;
    case SCOPE_FIELD_LINK:
        if (in->link) { raw[0] = 'L'; raw[1] = 'I'; raw[2] = 'N'; raw[3] = 'K'; raw[4] = '\0'; }
        *colour = SCOPE_COLOUR_LINK;
        break;
    case SCOPE_FIELD_HOLD:
        if (in->hold) { raw[0] = 'H'; raw[1] = 'O'; raw[2] = 'L'; raw[3] = 'D'; raw[4] = '\0'; }
        *colour = SCOPE_COLOUR_HOLD;
        break;
    default:
        break;
    }
}

/* One text field: pad to the field width, then redraw only if string or colour changed. */
static unsigned draw_field(scope_render_state *s, const scope_render_input *in, unsigned pane, scope_text_field f) {
    char raw[SCOPE_FIELD_MAX + 1u], text[SCOPE_FIELD_MAX + 1u];
    uint16_t colour;
    field_content(s, in, pane, f, raw, &colour);
    unsigned width = fields[f].width, len = 0;
    while (raw[len] && len < width) len++;
    unsigned lead = fields[f].right ? width - len : 0;
    for (unsigned i = 0; i < width; i++) text[i] = i >= lead && i - lead < len ? raw[i - lead] : ' ';
    text[width] = '\0';
    if (s->shown[pane][f].drawn && s->shown[pane][f].colour == colour && !strcmp(s->shown[pane][f].text, text))
        return 0;
    scope_rect r = scope_pane_field_rect(pane, f);
    bool ok = true;
    unsigned calls = draw_text(s, r.x, r.y, text, width, colour, &ok);
    s->text_rects += calls;
    memcpy(s->shown[pane][f].text, text, width + 1u);
    s->shown[pane][f].colour = colour;
    s->shown[pane][f].drawn = ok; /* a failed transfer is retried on the next pass */
    return calls;
}

static unsigned draw_column(scope_render_state *s, unsigned pane, unsigned col) {
    uint16_t px[SCOPE_PLOT_H];
    const scope_bin *bin = col >= s->window.first_col ? &s->cols[col] : NULL;
    scope_rect p = scope_pane_plot_rect(pane);
    scope_render_column(bin, s->cal, scope_range_volts(s->view_range[pane]), SCOPE_PLOT_H,
                        scope_channel_colour(pane), px);
    count(s, scope_display_rect((uint16_t)(p.x + col), p.y, 1, SCOPE_PLOT_H, px));
    return 1;
}

unsigned scope_render_step(scope_render_state *s, const scope_render_input *in, unsigned max_items) {
    unsigned calls = 0;
    if (!s || !in || !in->hist) return 0;
    for (unsigned n = 0; n < max_items; n++) {
        unsigned pane = s->pane;
        if (s->item == ITEM_STATIC) {
            if (!s->static_done[pane]) {
                calls += fill(s, scope_pane_tag_rect(pane), scope_channel_colour(pane));
                calls += fill(s, scope_pane_separator_rect(pane), SCOPE_COLOUR_SEPARATOR);
                s->static_done[pane] = true;
            }
            if (in->hold) {
                s->item = ITEM_TEXT0;
                continue;
            }
            s->view_time_code[pane] = scope_render_time_code(in, pane);
            s->view_linked[pane] = in->link;
            s->window_known[pane] = true;
            uint32_t window = scope_window_samples(s->view_time_code[pane], in->samples_per_s);
            s->window = scope_window_map(&in->hist[pane], window, SCOPE_PLOT_W, s->cols);
            int r = in->range[pane];
            if (r >= 0 && r < 3) { /* -1 (deadband / not yet decoded) keeps the last valid scale */
                s->view_range[pane] = (int8_t)r;
                s->range_known[pane] = true;
            }
            s->cal = scope_calibration_effective(in->cal[pane]);
            s->signal[pane] = (uint8_t)scope_bins_status(&s->cols[s->window.first_col],
                                                         SCOPE_PLOT_W - s->window.first_col, s->cal,
                                                         scope_range_volts(s->view_range[pane]));
            s->item = ITEM_COL0;
        } else if (s->item < ITEM_TEXT0) {
            if (in->hold) { /* HOLD mid-pane: freeze now, leave the rest of the plot as drawn */
                s->item = ITEM_TEXT0;
                continue;
            }
            calls += draw_column(s, pane, s->item - ITEM_COL0);
            s->item++;
        } else {
            calls += draw_field(s, in, pane, (scope_text_field)(s->item - ITEM_TEXT0));
            if (++s->item < ITEM_END) continue;
            s->item = ITEM_STATIC;
            if (++s->pane == SCOPE_CHANNELS) {
                s->pane = 0;
                s->passes++;
            }
        }
    }
    return calls;
}

bool scope_button_update(scope_button *b, bool pressed, uint32_t now_ms) {
    if (pressed != b->raw) {
        b->raw = pressed;
        b->since_ms = now_ms;
    } else if (b->raw != b->stable && (uint32_t)(now_ms - b->since_ms) >= SCOPE_BUTTON_DEBOUNCE_MS) {
        b->stable = b->raw;
        if (b->stable) b->toggled = !b->toggled;
    }
    return b->toggled;
}
